AubergineShallow/digital8mm/CLOUD-START-HERE.md

# GS8 D2 · cloud-polish copy

**Fork: `r5-cloud-polish-20261007`.** This independent copy starts from the stable desktop r5 capture of
6 October 2026, 14:04–14:05 UTC, with verified CAD exports captured by 14:11:53 UTC. Later desktop work is a separate
history. Extract into a new folder; do not overwrite or blindly merge into the active desktop project.

## Current result

**r6 (2026-10-08)** settles the print order and orientation and fixes the minor findings of the 2026-10-06 audit
(`cad/gs8-d2-v1/HANDOFF.md`, top section; `audit/d2-readiness-2026-10-06/RESPONSE.md`):
- **Kowa:** 28 categories, 27 passing plus `mass_com`, which is now report-only. 833 pass + 19 information rows, no
  failures, stubs or unclassified thin spots.
- **Fujinon:** 28 categories, 830 pass + 19 information rows.
- The new `print_overhang` category passes for all 12 parts and the centring gauge.
- The release audit passes 20 / 86 / 4.

The cloud-polish result it builds on, kept for the record:
- **Kowa:** 27 passing CAD categories; 748 pass + 18 information rows, no failures, stubs or unclassified thin spots.
- **Fujinon:** 27 passing categories; 745 pass + 18 information rows, no failures, stubs or unclassified thin spots.
- Independent audits verify every required source/output/gate-document hash, actual STL meshes, fresh STEP,
  producer-bound coupons/common tests, both-lens linkage and complete runtime/manifest coverage.
- **Tests:** 65 CAD regressions + 73 focused tests; the full collar check passes for both lenses. The D2/EVF package
  passes 256 host tests; the post planner passes 66, the existing recorder 110, and native numerical models 69.
- **Physical qualification: unchanged.** All 53 physical gates remain open. Nothing was printed, sliced, measured,
  assembled, powered, purchased or deployed by this pass. These results do not establish fabrication or operation readiness.
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
