AubergineShallow/digital8mm/visual-review/REVIEW.md

# D2 visual and ergonomic review

Final review, 2026-10-07 SGT. Reviewed the original r5 render pixels, source design/control contracts, corrected panel pixels, and the final cloud-polish assembly/part STEP. The final Kowa receipt is 806c7b381e1133a5e69c2d1547d915ac305bec2e1cb5e5cf168f74d81eae4832. All dimensions below are CAD/source values, not physical measurements.

Both lens variants have passing computed CAD/integrity reports. All 53 physical gates remain open. The gallery is an intended-finish visualization of the separate cloud-polish fork, not a fabricated or commissioned camera.
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
