AubergineShallow/digital8mm/cad/gs8-d2-v1/airflow/out/domain/slice-1.5-xm7.png

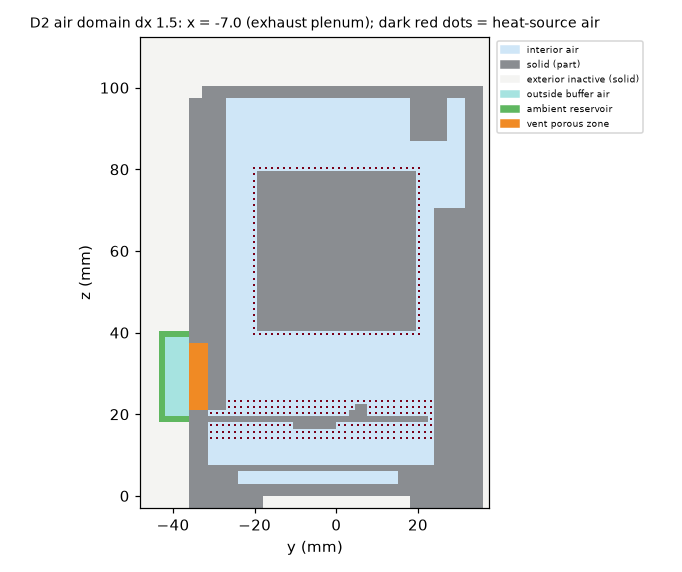
cad/gs8-d2-v1/airflow/out/domain/slice-1.5-xm7.png
