AubergineShallow/digital8mm/cad/gs8-d2-v1/airflow/out/domain/slice-1.5-ym10.png

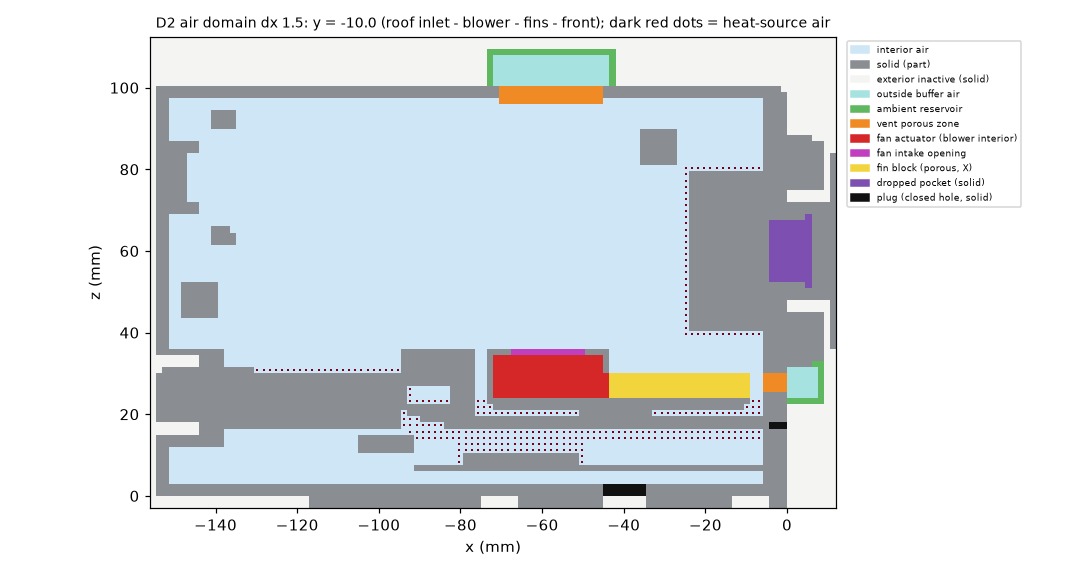
cad/gs8-d2-v1/airflow/out/domain/slice-1.5-ym10.png
