AubergineShallow/digital8mm/cad/gs8-d2-v1/airflow/out/domain/slice-2.0-ym10.png

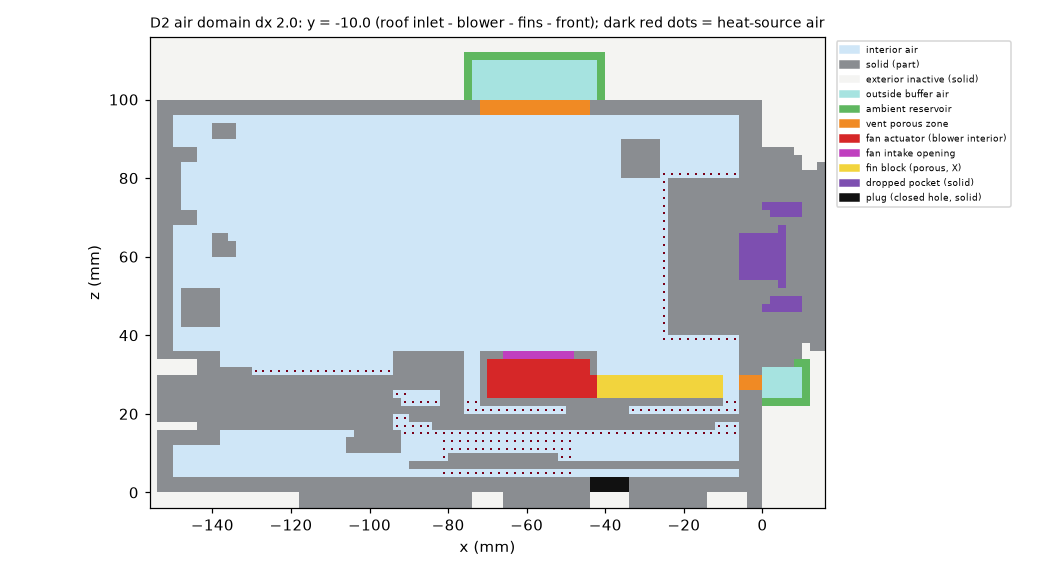
cad/gs8-d2-v1/airflow/out/domain/slice-2.0-ym10.png
