AubergineShallow/digital8mm/cad/gs8-d2-v1/airflow/out/figures/2.0-finaxis/pressure_slices.png

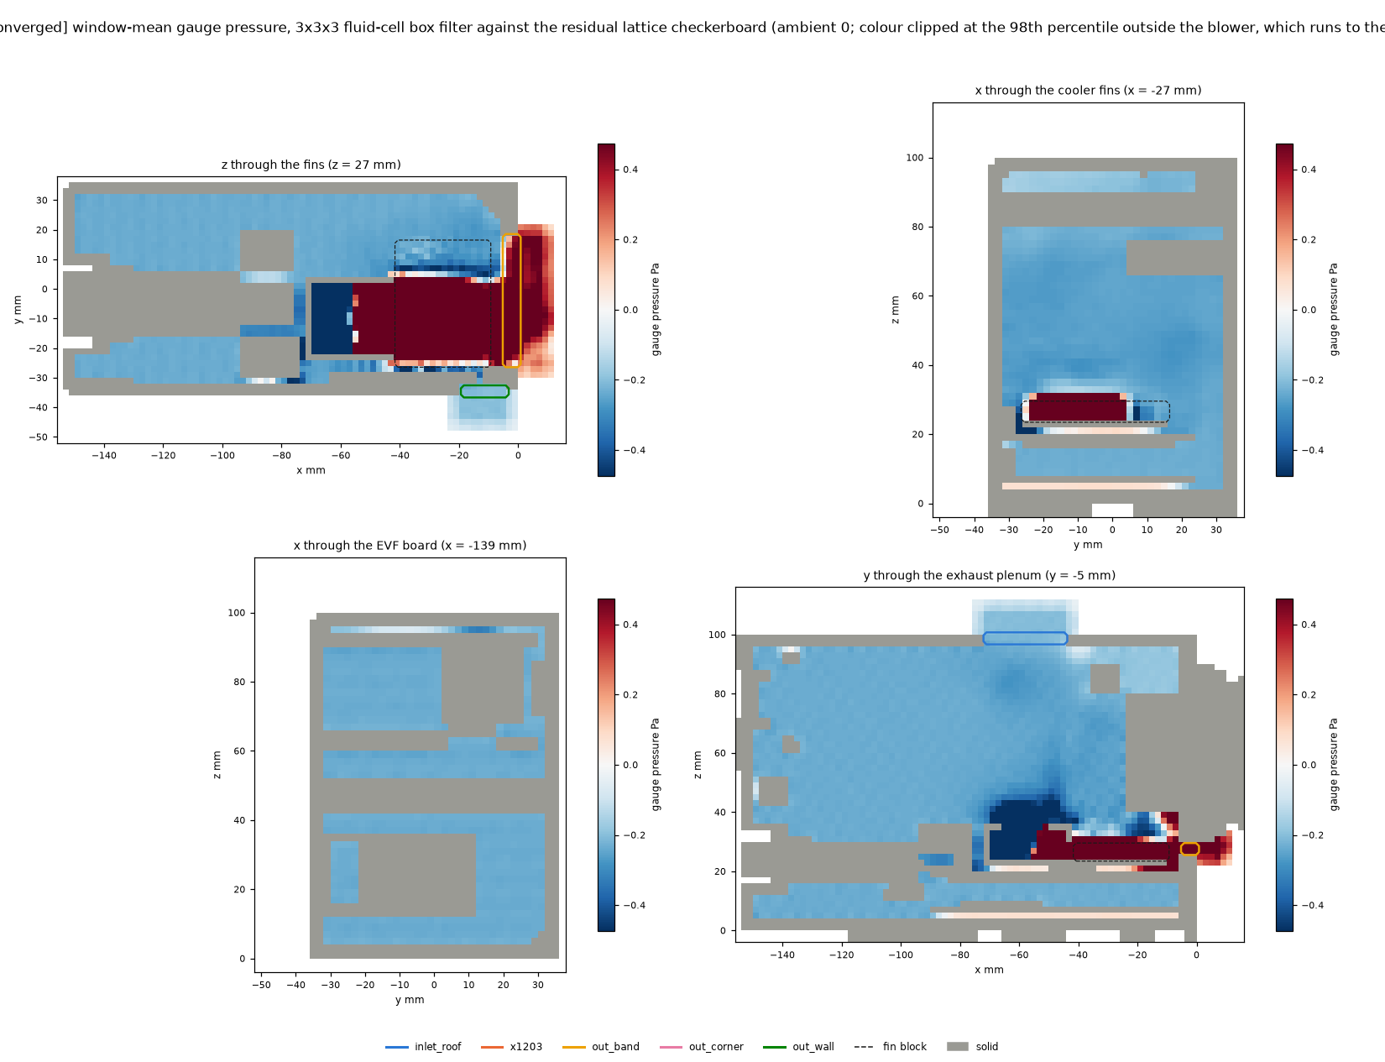
cad/gs8-d2-v1/airflow/out/figures/2.0-finaxis/pressure_slices.png
