AubergineShallow/digital8mm/cad/gs8-d2-v1/airflow/out/figures/2.0-finaxis/temp_S2__adiabatic.png

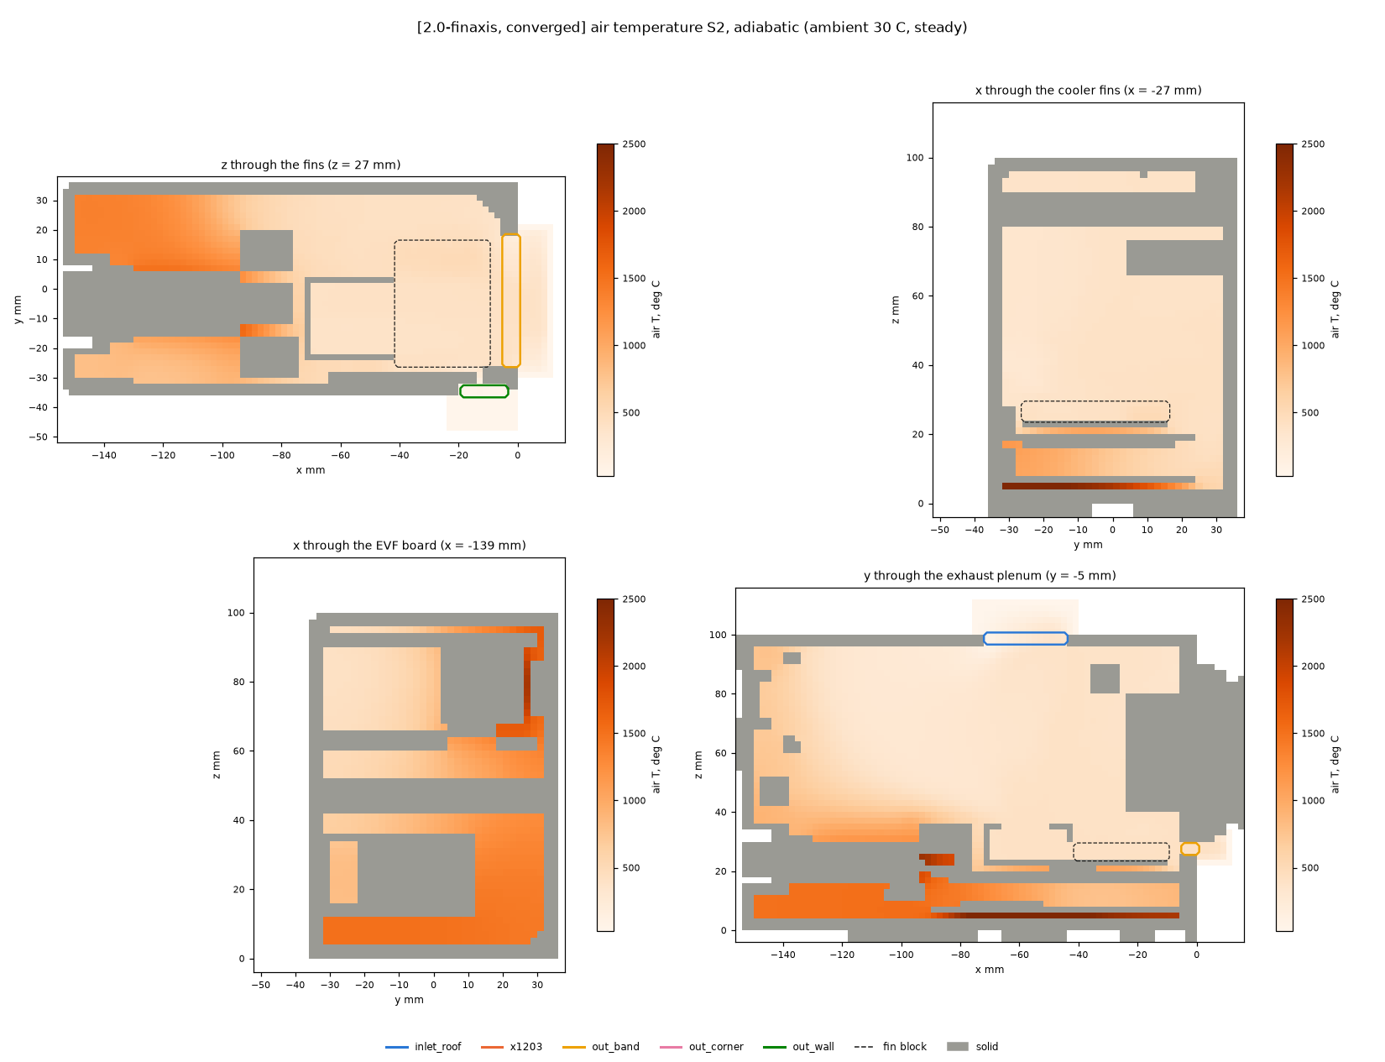
cad/gs8-d2-v1/airflow/out/figures/2.0-finaxis/temp_S2__adiabatic.png
