AubergineShallow/digital8mm/cad/gs8-d2-v1/airflow/out/figures/zzztest/speed_slices.png

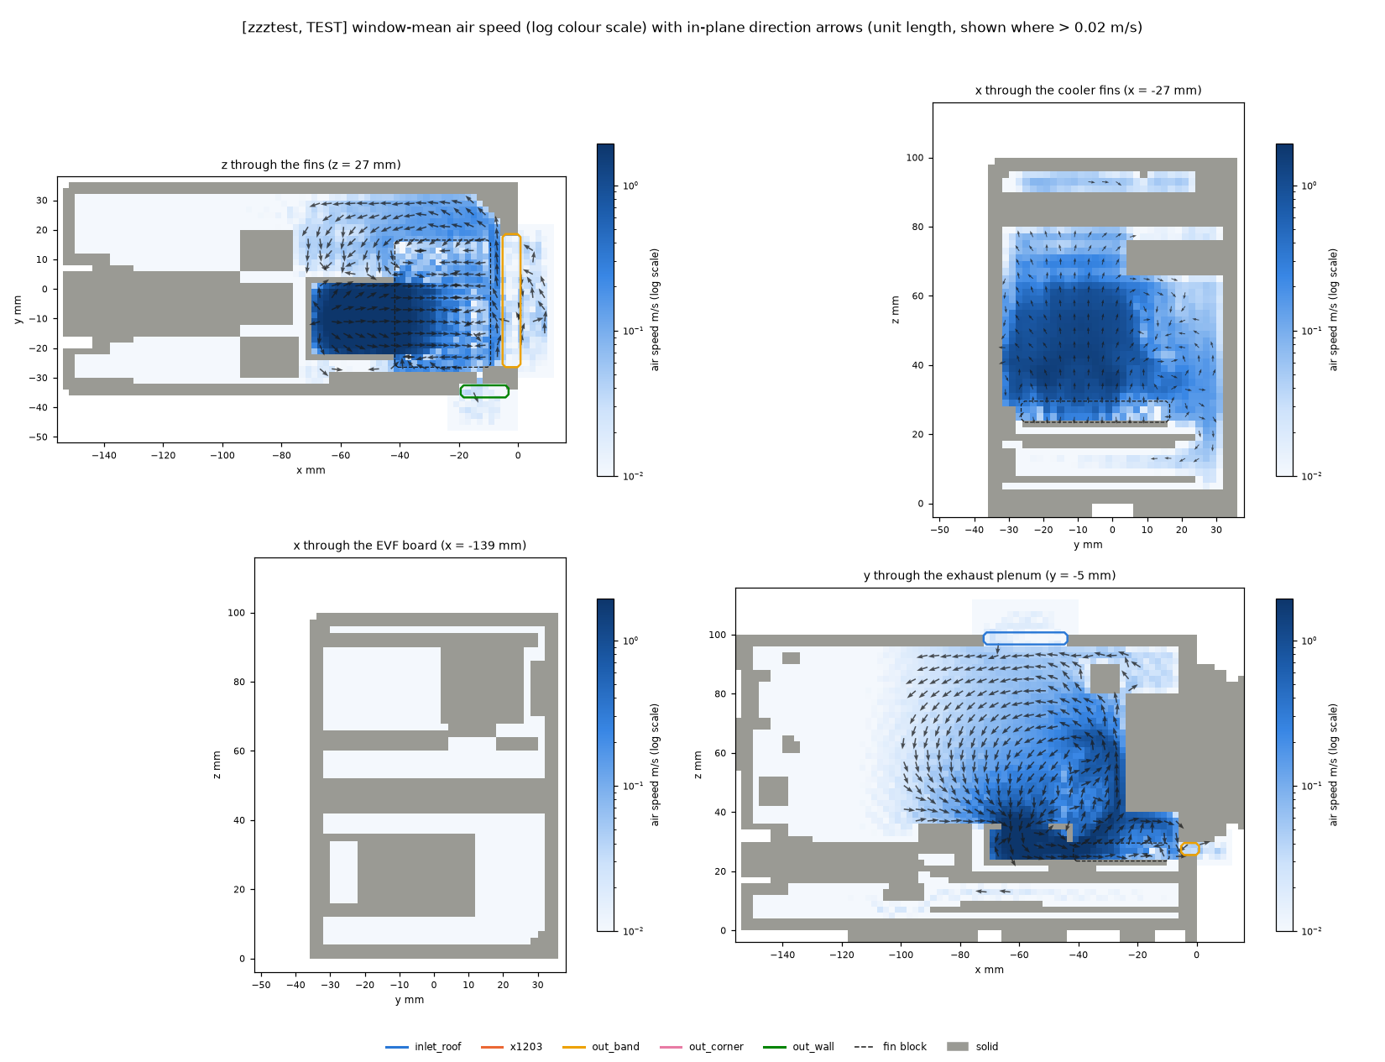
cad/gs8-d2-v1/airflow/out/figures/zzztest/speed_slices.png
