AubergineShallow/digital8mm/cad/gs8-d2-v1/airflow/out/figures/zzztest/streamlines.png

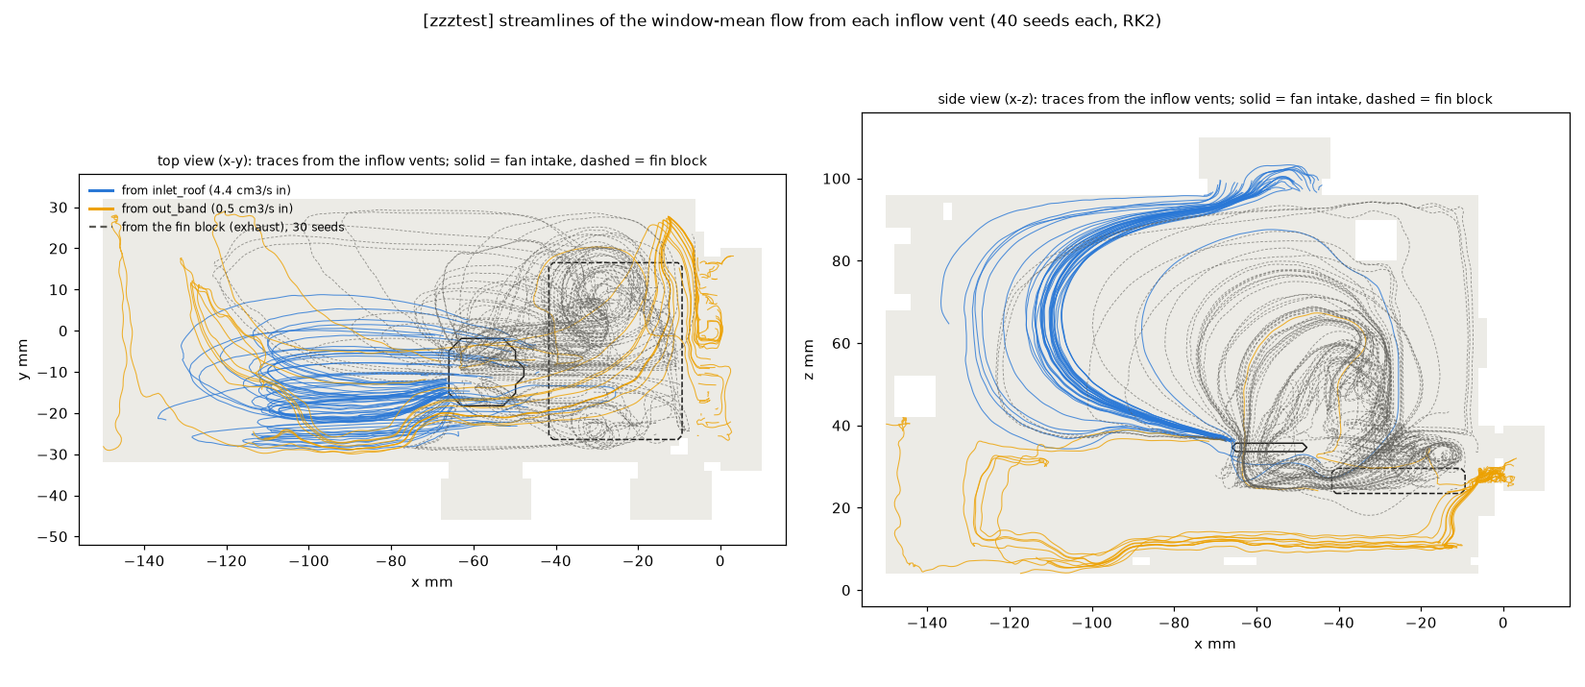
cad/gs8-d2-v1/airflow/out/figures/zzztest/streamlines.png
