AubergineShallow/digital8mm/cad/gs8-d2-v1/airflow/out/variants/compare-throughflow-soc.png

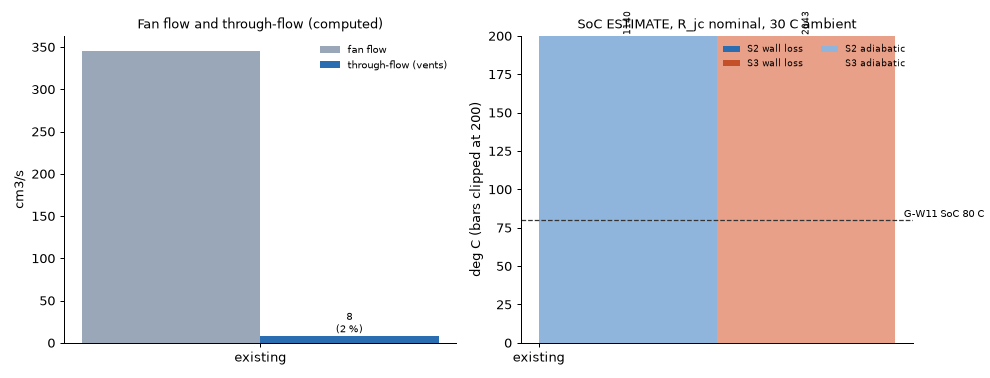
cad/gs8-d2-v1/airflow/out/variants/compare-throughflow-soc.png
