AubergineShallow/digital8mm/cad/gs8-d2-v1/airflow/out/variants/domain-edit-V1.png

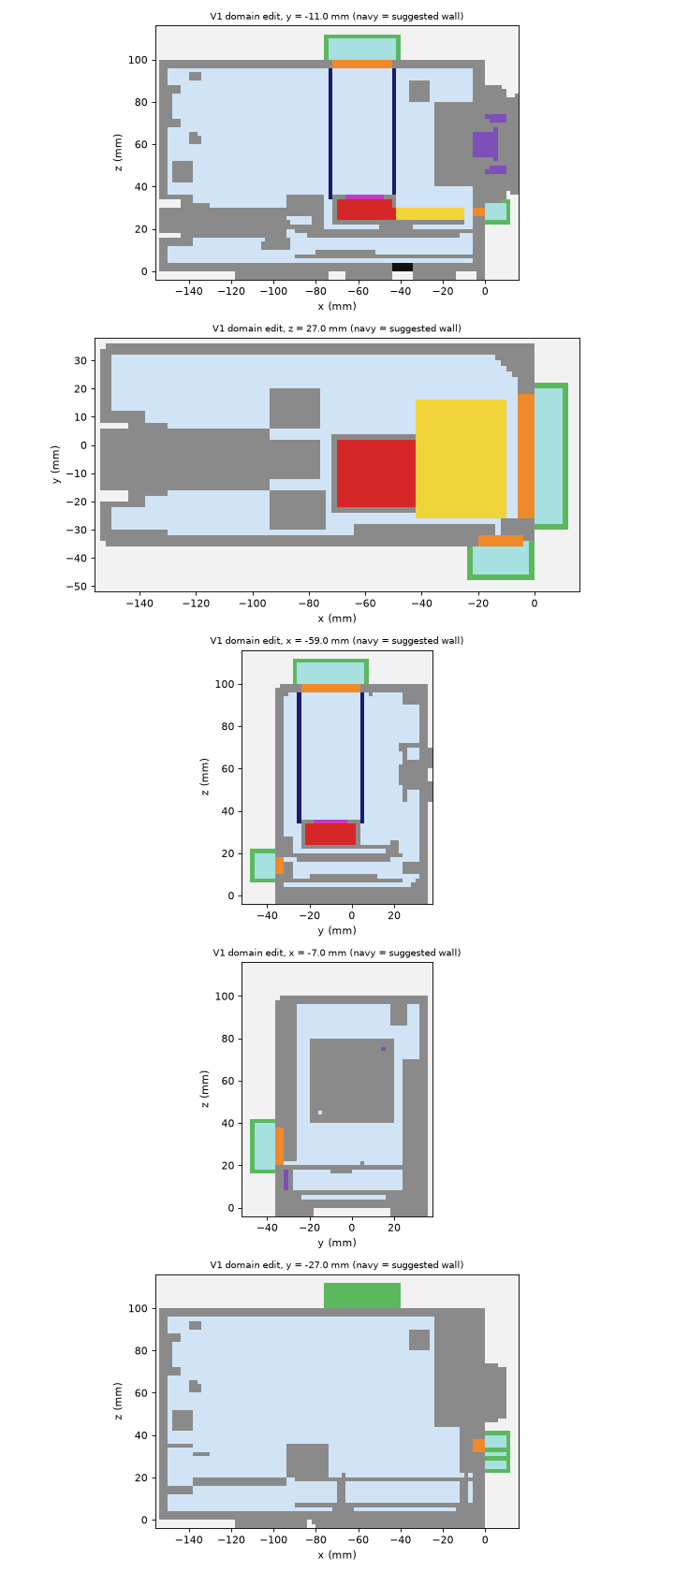
cad/gs8-d2-v1/airflow/out/variants/domain-edit-V1.png
