AubergineShallow/digital8mm/cad/gs8-d2-v1/airflow/out/variants/velocity-z27.png

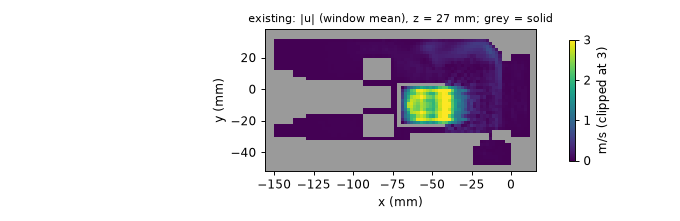
cad/gs8-d2-v1/airflow/out/variants/velocity-z27.png
