AubergineShallow/digital8mm/cad/gs8-d2-v1/candidate-fr1/preview/mobile.png

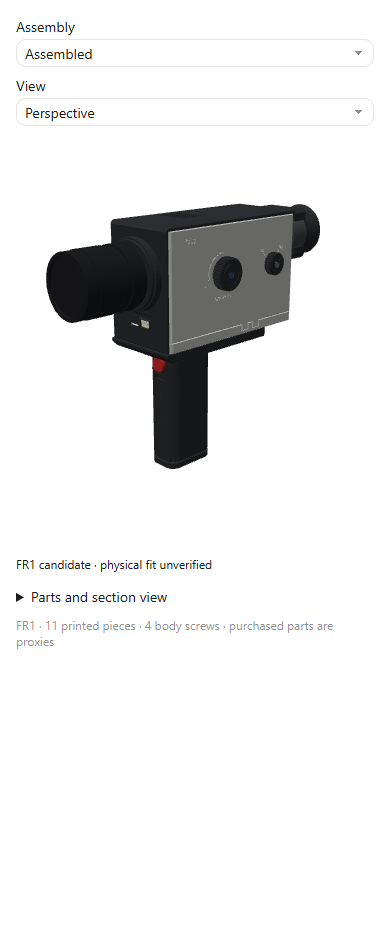
cad/gs8-d2-v1/candidate-fr1/preview/mobile.png
