AubergineShallow/digital8mm/cad/gs8-d2-v1/out/_fujinon-cloud-polish-20261007/renders/section-base-edge-x91.png

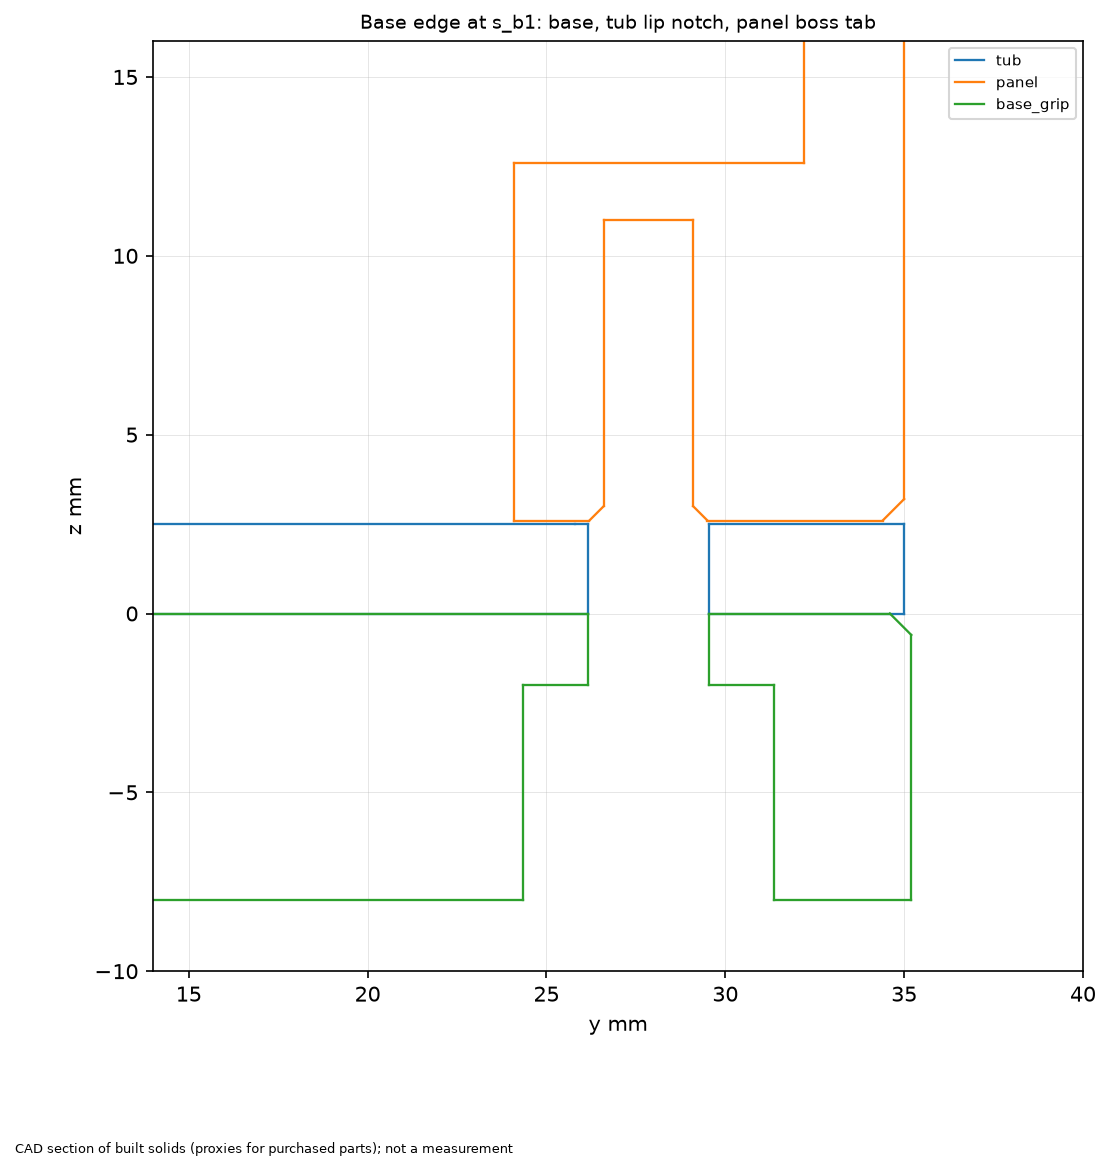
cad/gs8-d2-v1/out/_fujinon-cloud-polish-20261007/renders/section-base-edge-x91.png
