AubergineShallow/digital8mm/visual-review/renders/collar_pinch.png

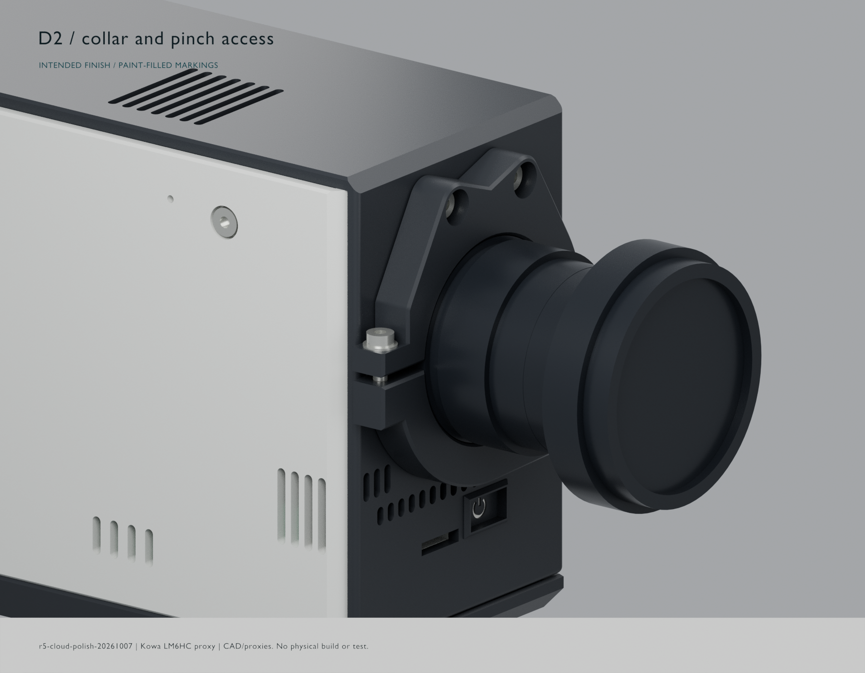
visual-review/renders/collar_pinch.png
