AubergineShallow/digital8mm/visual-review/renders/controls-raw.png

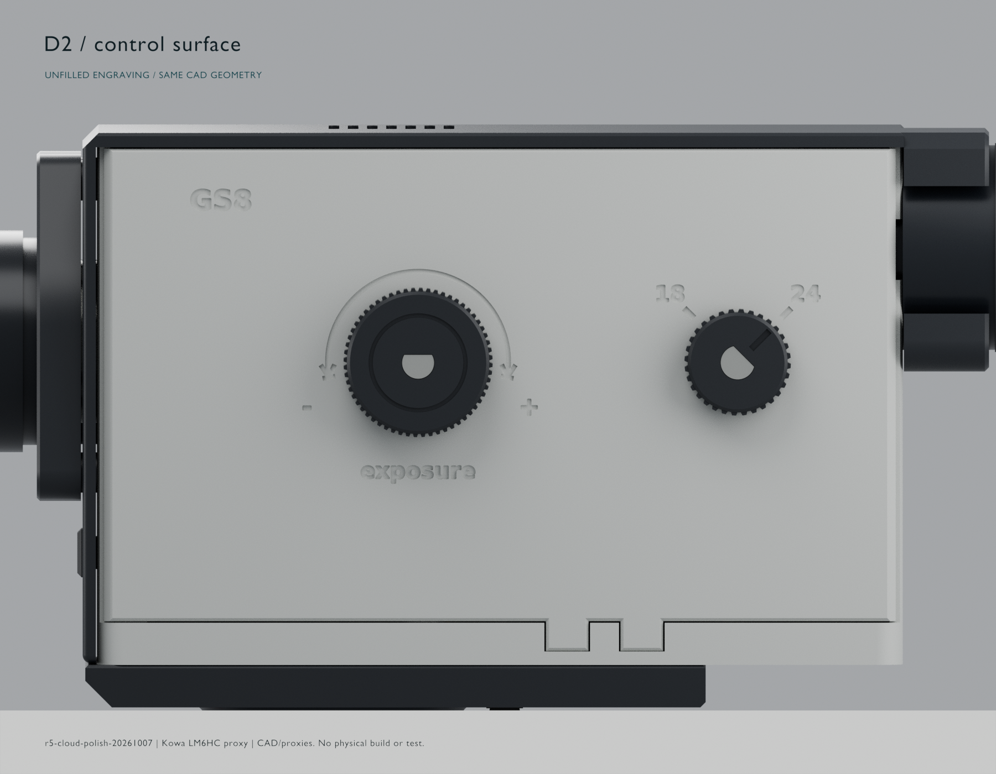
visual-review/renders/controls-raw.png
