AubergineShallow/digital8mm/visual-review/renders/hero.png

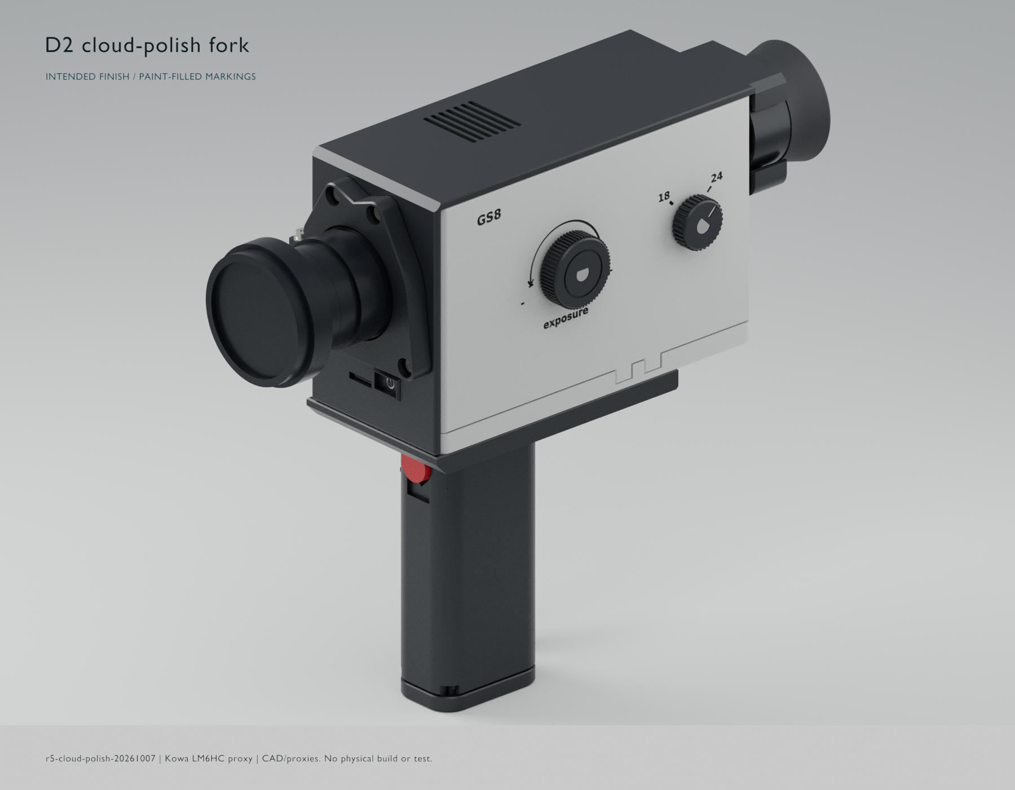
visual-review/renders/hero.png
