AubergineShallow/digital8mm/visual-review/renders/rear.png

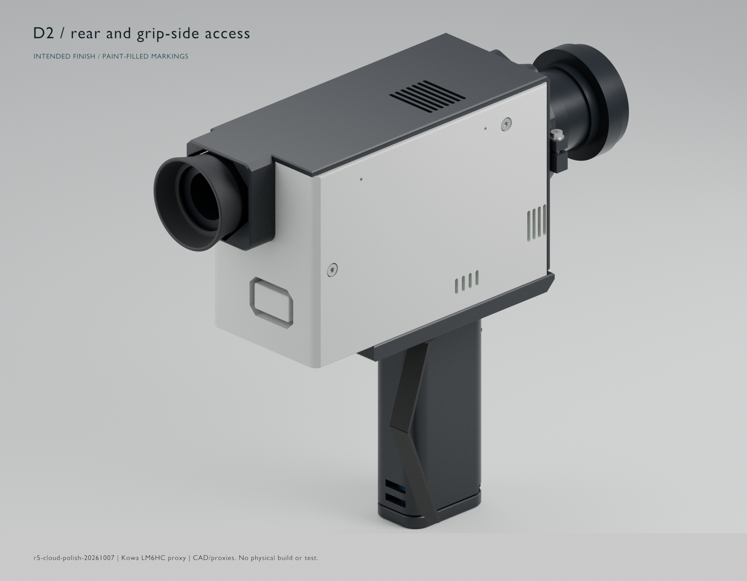
visual-review/renders/rear.png
