AubergineShallow/digital8mm/visual-review/renders/service.png

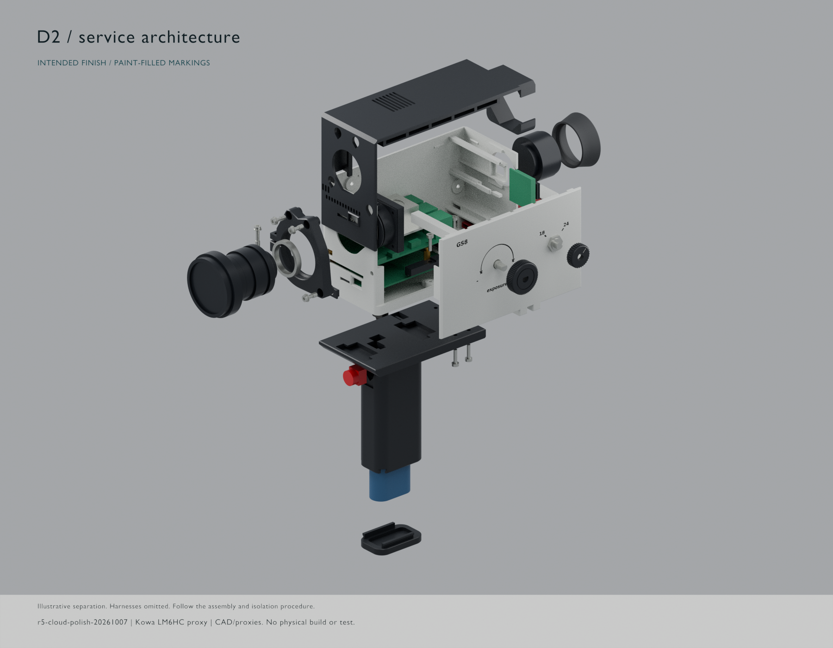
visual-review/renders/service.png
