AubergineShallow/digital8mm/cad/gs8-d2-v1/airflow/out/meshes/plunger.stl

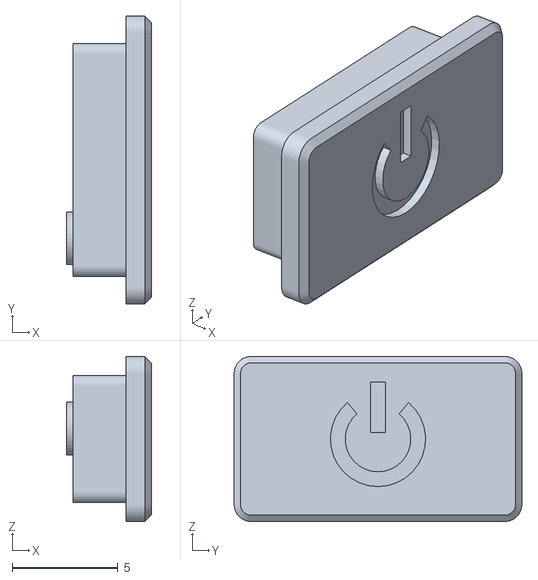
[picture p52: CAD file, 2026-10-08]
cad/gs8-d2-v1/airflow/out/meshes/plunger.stl
4.00 x 13.6 x 7.80
