AubergineShallow/digital8mm/cad/gs8-d2-v1/out/_fujinon-cloud-polish-20261007/stl/modifiers/tub__mod_s_r1.stl

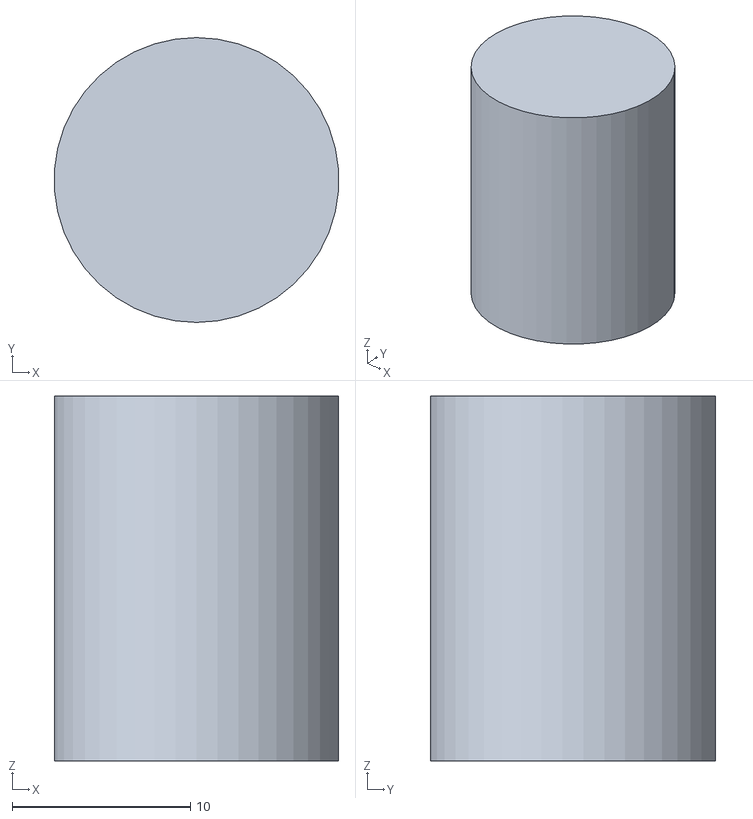
[picture p53: CAD file, 2026-10-08]
cad/gs8-d2-v1/out/_fujinon-cloud-polish-20261007/stl/modifiers/tub__mod_s_r1.stl
16.0 x 16.0 x 20.5
