AubergineShallow/digital8mm/cad/gs8-d2-v1/out/stl/coupons/collar_part.stl

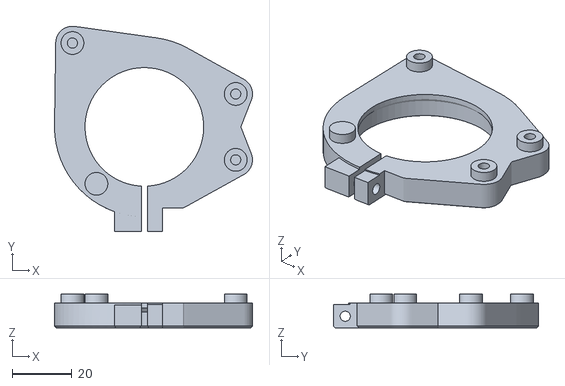
[picture p54: CAD file, 2026-10-08]
cad/gs8-d2-v1/out/stl/coupons/collar_part.stl
66.1 x 68.6 x 11.3
