AubergineShallow/digital8mm/audit/d2-readiness-2026-10-05/rebuild-kowa/stl/panel.stl

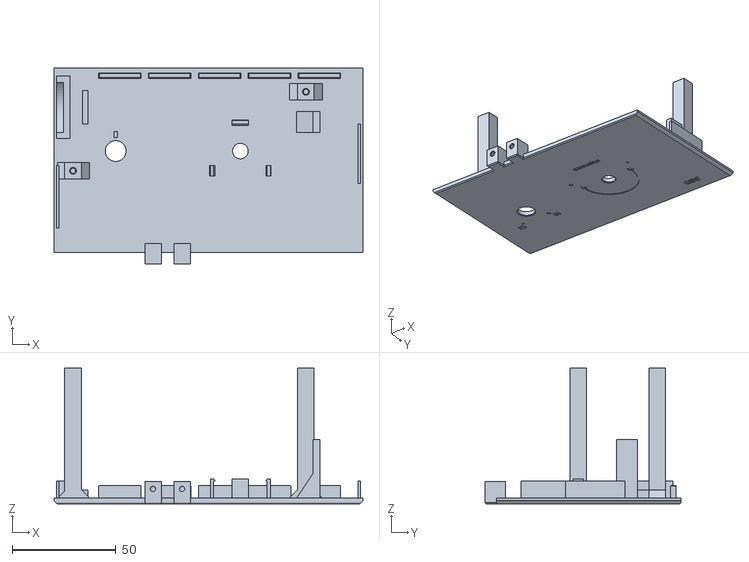
[picture p55: CAD file, 2026-10-08]
audit/d2-readiness-2026-10-05/rebuild-kowa/stl/panel.stl
148.6 x 94.4 x 65.4
