AubergineShallow/digital8mm/audit/d2-readiness-2026-10-06/rebuild-kowa/stl/stick_sleeve.stl

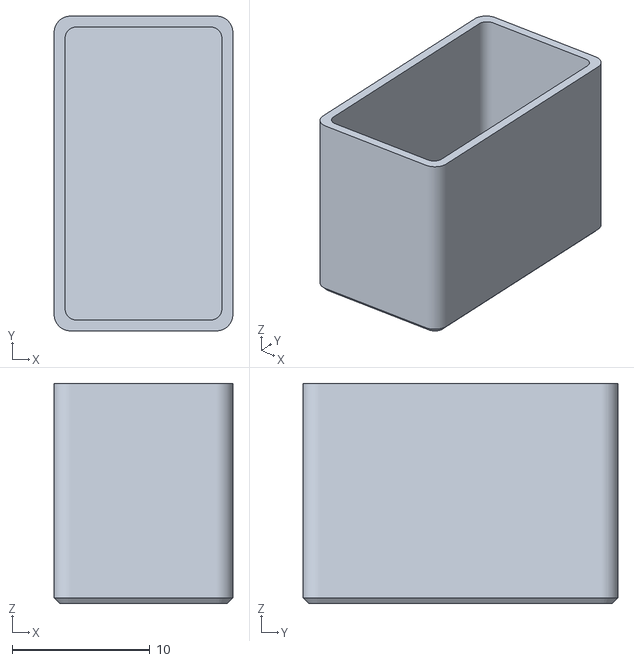
[picture p56: CAD file, 2026-10-08]
audit/d2-readiness-2026-10-06/rebuild-kowa/stl/stick_sleeve.stl
13.0 x 22.9 x 16.0
