AubergineShallow/digital8mm/cad/gs8-d2-v1/airflow/out/meshes/gs_camera.stl

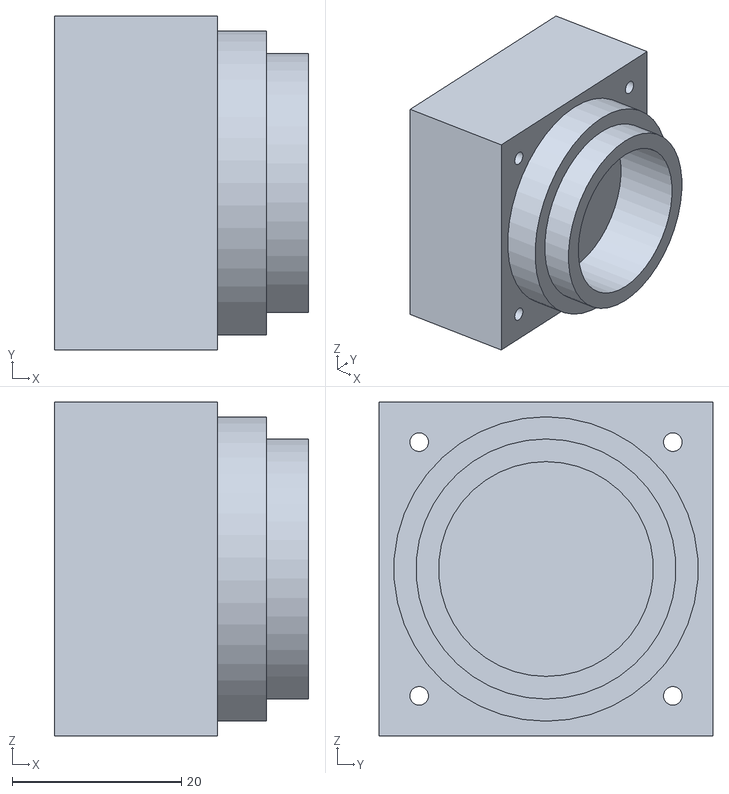
[picture p57: CAD file, 2026-10-08]
cad/gs8-d2-v1/airflow/out/meshes/gs_camera.stl
30.1 x 39.5 x 39.5
