AubergineShallow/digital8mm/cad/gs8-d2-v1/out/stl/coupons/collar_tub_front.stl

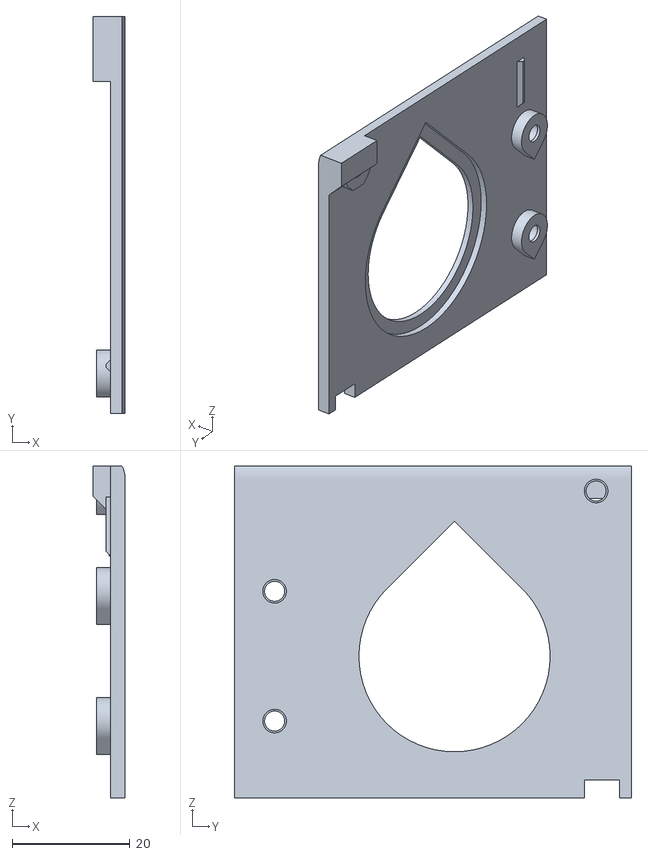
[picture p58: CAD file, 2026-10-08]
cad/gs8-d2-v1/out/stl/coupons/collar_tub_front.stl
5.50 x 67.3 x 56.2
