AubergineShallow/digital8mm/audit/d2-readiness-2026-10-05/rebuild-kowa/stl/hood.stl

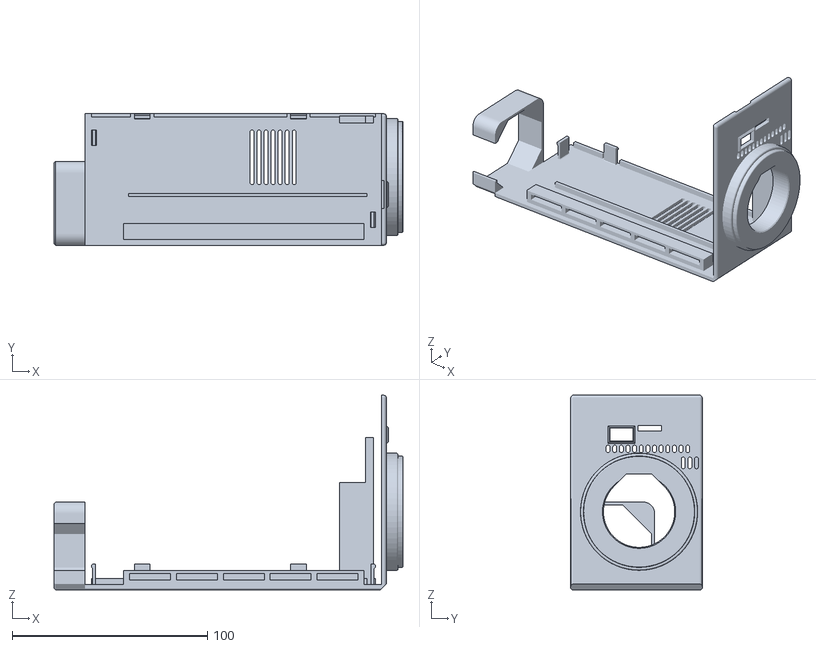
[picture p59: CAD file, 2026-10-08]
audit/d2-readiness-2026-10-05/rebuild-kowa/stl/hood.stl
178.7 x 67.3 x 99.7
