AubergineShallow/digital8mm/cad/gs8-d2-v1/airflow/out/meshes/encoder.stl

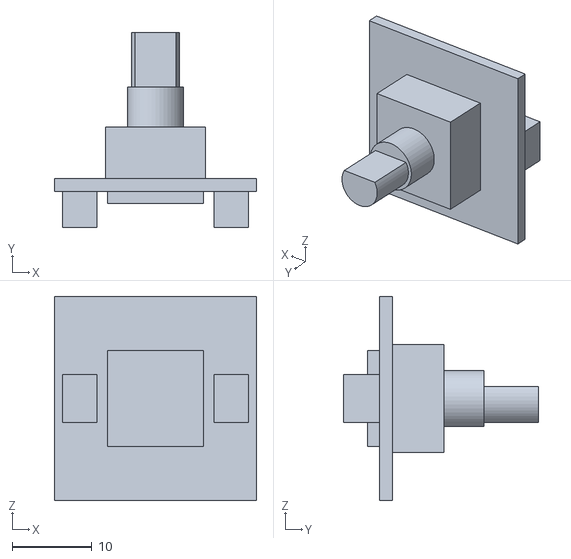
[picture p60: CAD file, 2026-10-08]
cad/gs8-d2-v1/airflow/out/meshes/encoder.stl
25.3 x 24.4 x 25.6
