AubergineShallow/digital8mm/cad/gs8-d2-v1/out/_fujinon-cloud-polish-20261007/step/parts/tub.step

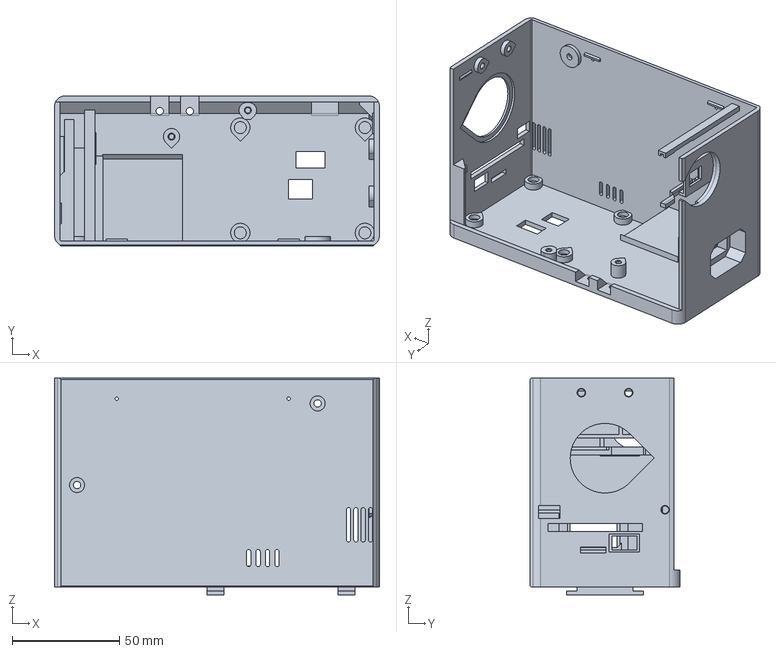
[picture p61: CAD file, 2026-10-09]
cad/gs8-d2-v1/out/_fujinon-cloud-polish-20261007/step/parts/tub.step
151.3 x 70.0 x 101.0 mm
