AubergineShallow/digital8mm/cad/gs8-d2-v1/out/step/parts/knob_exp.step

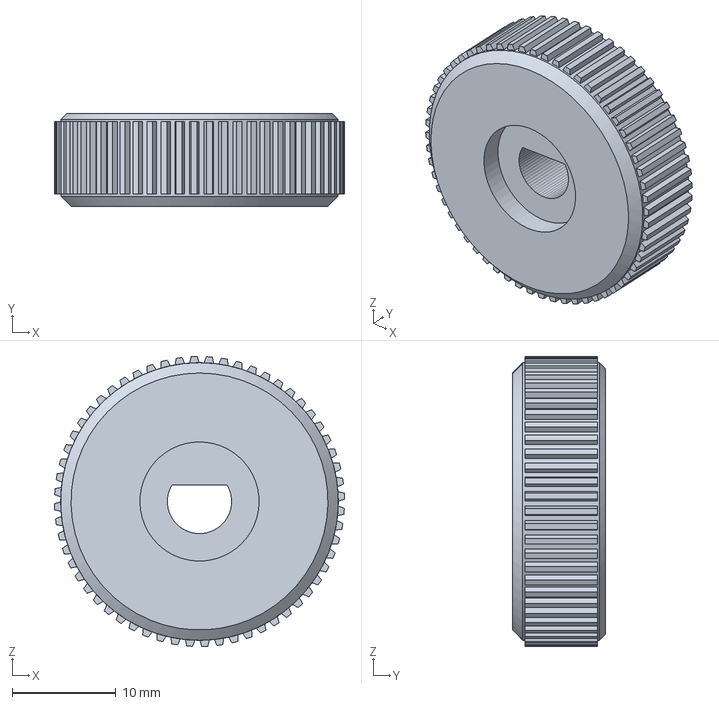
[picture p62: CAD file, 2026-10-09]
cad/gs8-d2-v1/out/step/parts/knob_exp.step
28.0 x 9.00 x 28.0 mm
