AubergineShallow/digital8mm/cad/gs8-d2-v1/out/stl/coupons/hood_ledge_ret.stl

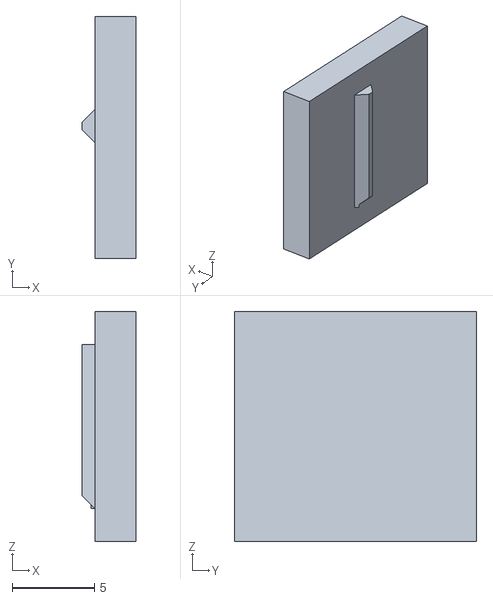
[picture p63: CAD file, 2026-10-08]
cad/gs8-d2-v1/out/stl/coupons/hood_ledge_ret.stl
3.30 x 14.8 x 14.0
