AubergineShallow/digital8mm/audit/d2-readiness-2026-10-05-r3/rebuild-fr1/stl/base_grip.stl

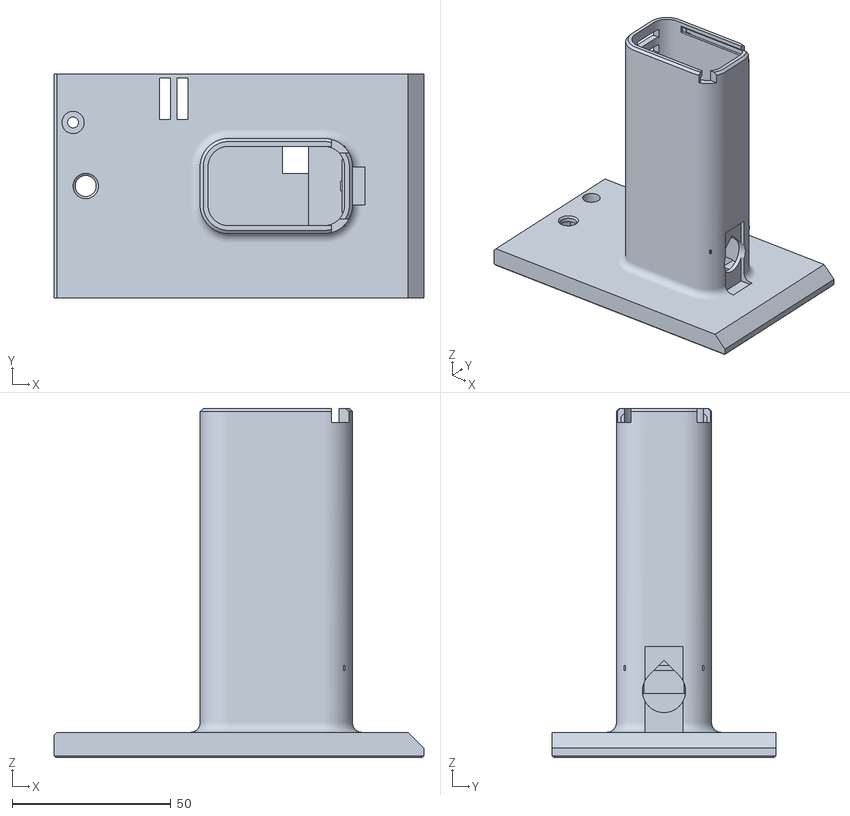
[picture p64: CAD file, 2026-10-08]
audit/d2-readiness-2026-10-05-r3/rebuild-fr1/stl/base_grip.stl
116.5 x 70.4 x 110.0
