AubergineShallow/digital8mm/cad/gs8-d2-v1/airflow/out/meshes/hmx039.stl

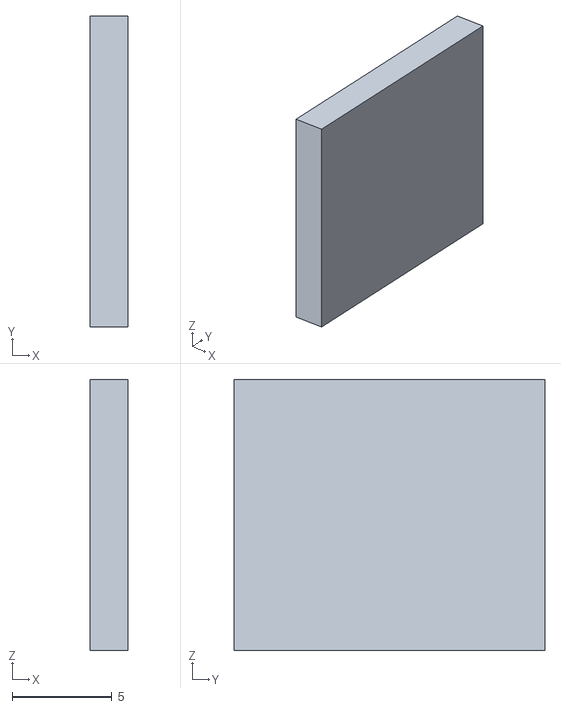
[picture p65: CAD file, 2026-10-08]
cad/gs8-d2-v1/airflow/out/meshes/hmx039.stl
1.93 x 15.6 x 13.6
