AubergineShallow/digital8mm/cad/gs8-d2-v1/out/step/parts/cap.step

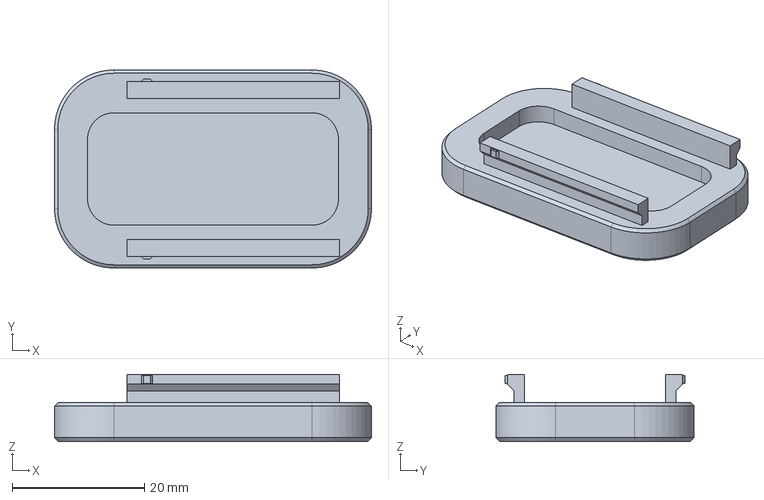
[picture p66: CAD file, 2026-10-09]
cad/gs8-d2-v1/out/step/parts/cap.step
48.0 x 30.0 x 10.2 mm
