AubergineShallow/digital8mm/cad/gs8-d2-v1/out/stl/coupons/evf_stop_panel.stl

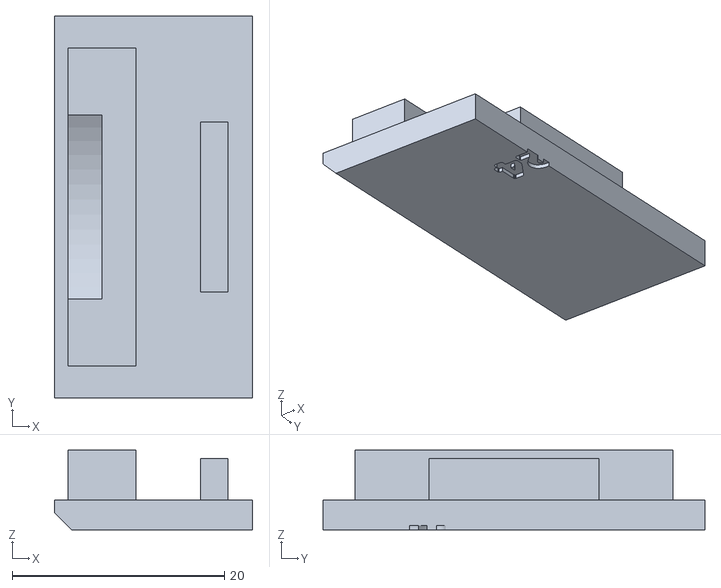
[picture p67: CAD file, 2026-10-08]
cad/gs8-d2-v1/out/stl/coupons/evf_stop_panel.stl
18.7 x 36.0 x 7.50
