AubergineShallow/digital8mm/audit/d2-readiness-2026-10-05-r3/rebuild-fr1/stl/panel.stl

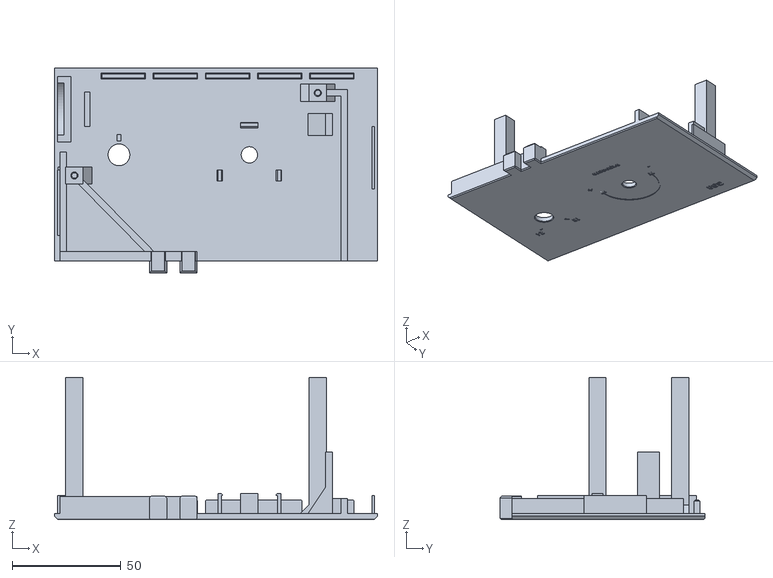
[picture p68: CAD file, 2026-10-08]
audit/d2-readiness-2026-10-05-r3/rebuild-fr1/stl/panel.stl
148.6 x 94.4 x 65.4
