AubergineShallow/digital8mm/cad/gs8-d2-v1/airflow/out/meshes/c_cs_adapter.stl

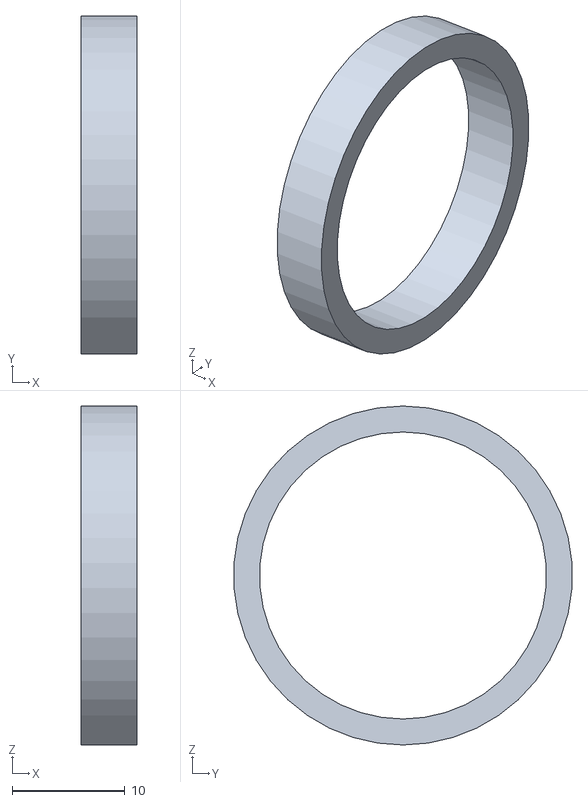
[picture p69: CAD file, 2026-10-08]
cad/gs8-d2-v1/airflow/out/meshes/c_cs_adapter.stl
5.00 x 29.9 x 30.0
