AubergineShallow/digital8mm/cad/gs8-d2-v1/out/_fujinon-cloud-polish-20261007/step/parts/hood.step

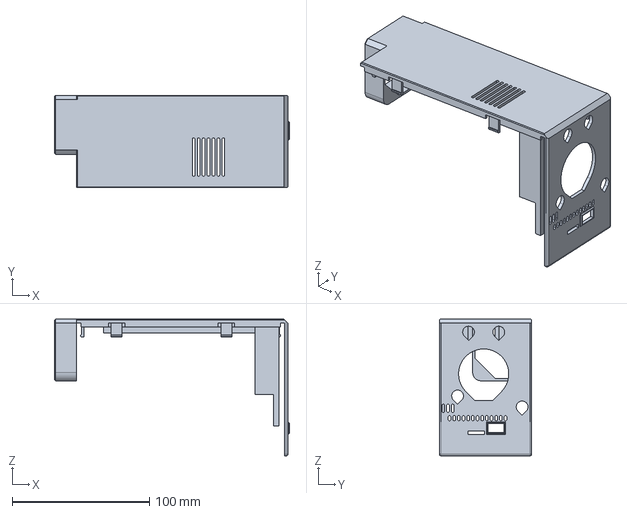
[picture p70: CAD file, 2026-10-09]
cad/gs8-d2-v1/out/_fujinon-cloud-polish-20261007/step/parts/hood.step
171.2 x 67.3 x 99.7 mm
