AubergineShallow/digital8mm/cad/gs8-d2-v1/out/stl/coupons/keyhole_slot.stl

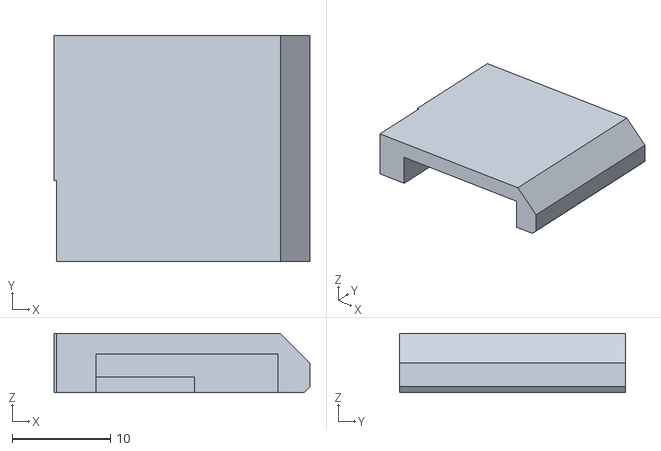
[picture p71: CAD file, 2026-10-08]
cad/gs8-d2-v1/out/stl/coupons/keyhole_slot.stl
26.0 x 23.0 x 6.00
