AubergineShallow/digital8mm/cad/gs8-d2-v1/out/_fujinon-cloud-polish-20261007/step/parts/lens_collar.step

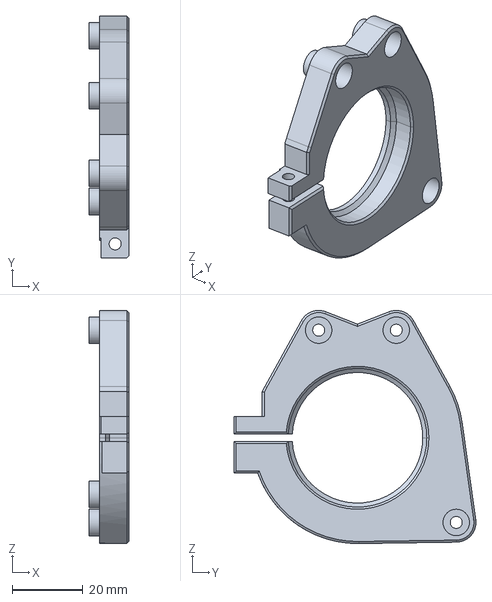
[picture p72: CAD file, 2026-10-09]
cad/gs8-d2-v1/out/_fujinon-cloud-polish-20261007/step/parts/lens_collar.step
11.3 x 68.6 x 66.1 mm
