AubergineShallow/digital8mm/cad/gs8-d2-v1/out/stl/coupons/pt_boss_bottom.stl

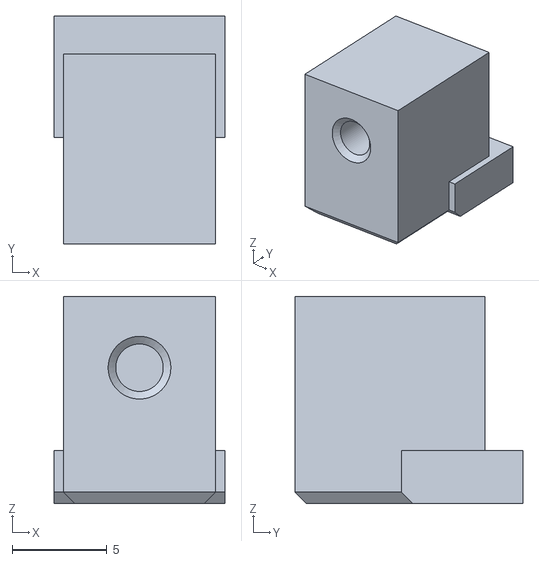
[picture p73: CAD file, 2026-10-08]
cad/gs8-d2-v1/out/stl/coupons/pt_boss_bottom.stl
9.00 x 12.0 x 10.9
