AubergineShallow/digital8mm/audit/d2-readiness-2026-10-06/rebuild-kowa/stl/hood.stl

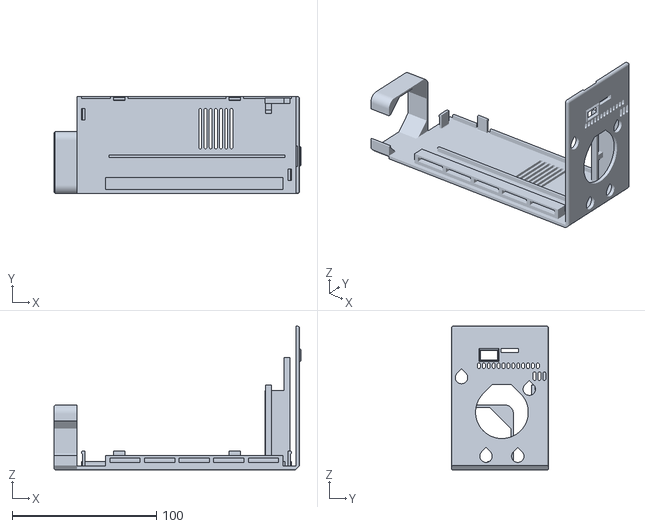
[picture p74: CAD file, 2026-10-08]
audit/d2-readiness-2026-10-06/rebuild-kowa/stl/hood.stl
171.2 x 67.3 x 99.7
