AubergineShallow/digital8mm/cad/gs8-d2-v1/airflow/out/meshes/s_r2.stl

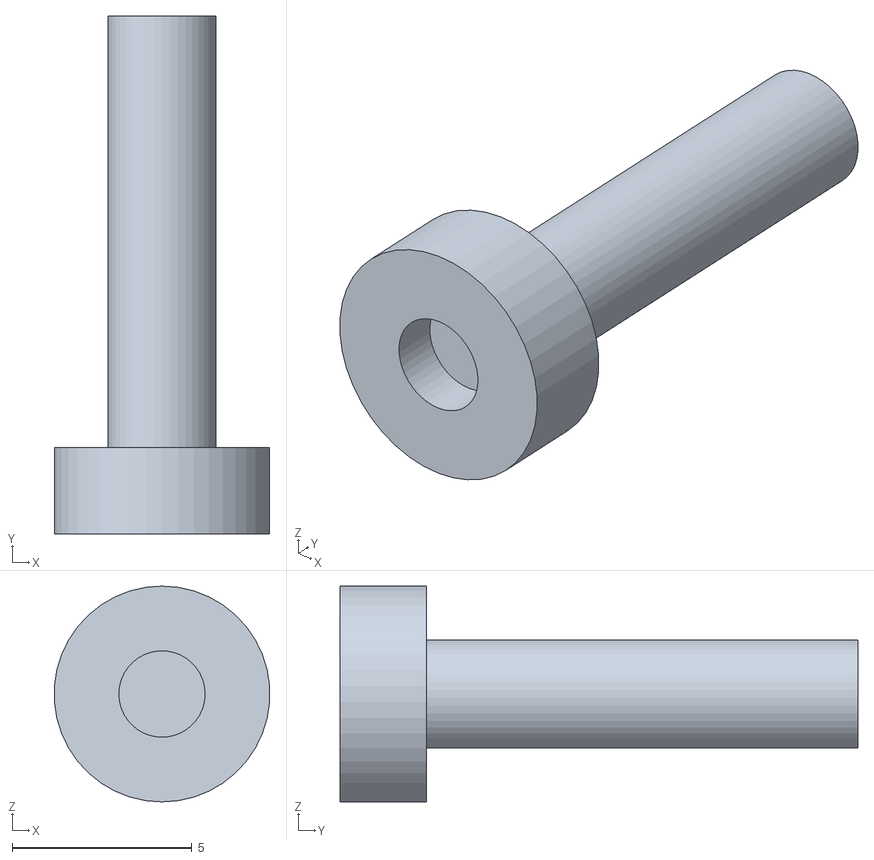
[picture p75: CAD file, 2026-10-08]
cad/gs8-d2-v1/airflow/out/meshes/s_r2.stl
5.98 x 14.4 x 6.00
