AubergineShallow/digital8mm/cad/gs8-d2-v1/out/stl/coupons/encoder_cradle_hook.stl

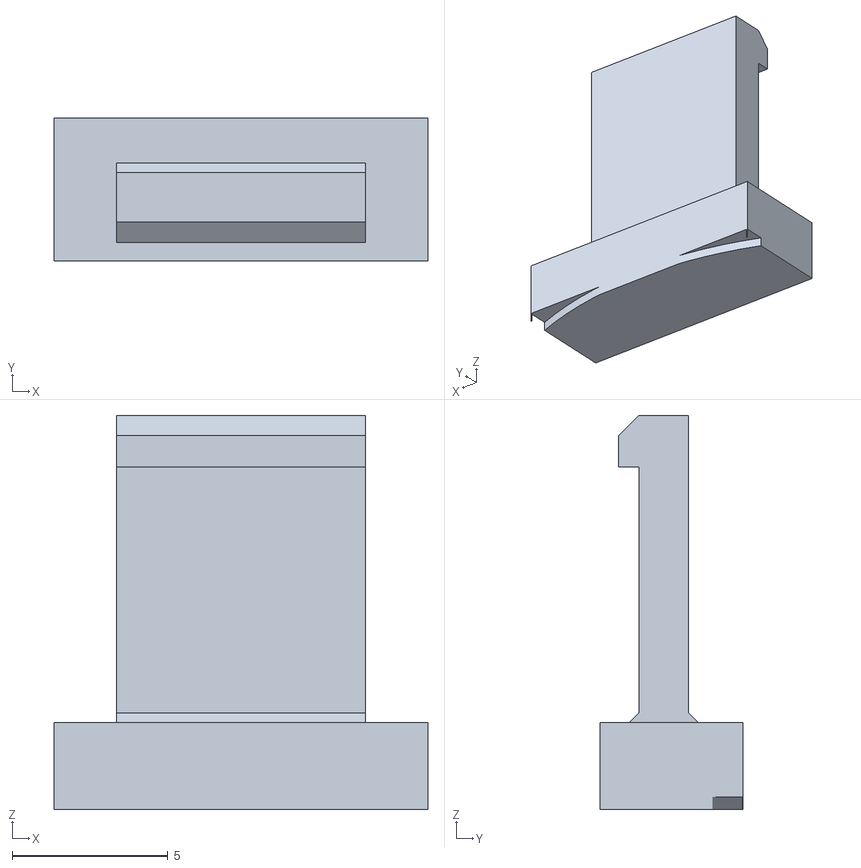
[picture p76: CAD file, 2026-10-08]
cad/gs8-d2-v1/out/stl/coupons/encoder_cradle_hook.stl
12.0 x 4.60 x 12.6
