AubergineShallow/digital8mm/cad/gs8-d2-v1/out/stl/coupons/clearance_comb.stl

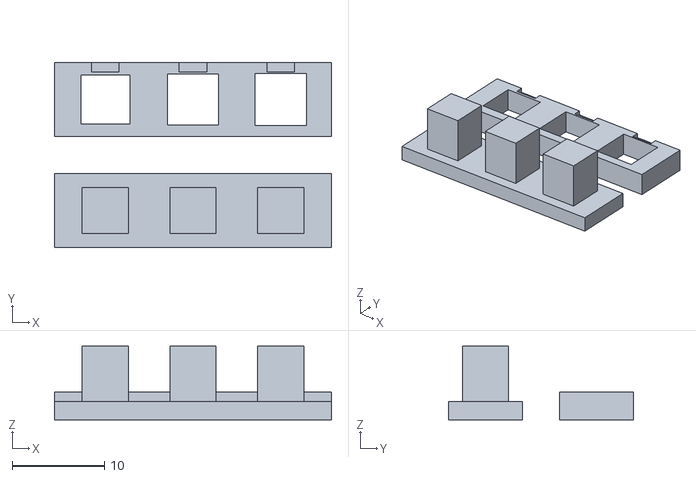
[picture p77: CAD file, 2026-10-08]
cad/gs8-d2-v1/out/stl/coupons/clearance_comb.stl
30.0 x 20.0 x 8.00
