AubergineShallow/digital8mm/audit/d2-readiness-2026-10-06/rebuild-kowa/stl/lens_collar.stl

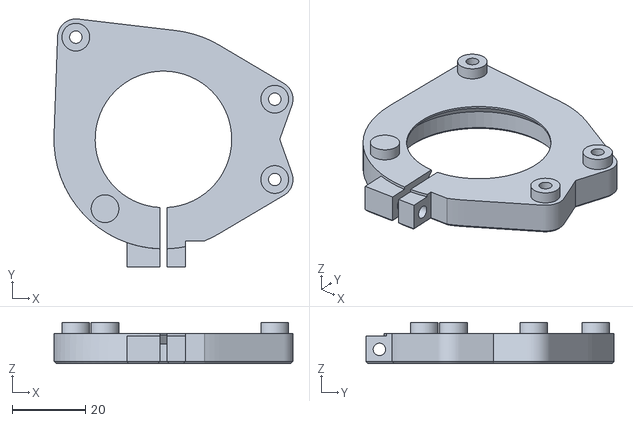
[picture p78: CAD file, 2026-10-08]
audit/d2-readiness-2026-10-06/rebuild-kowa/stl/lens_collar.stl
65.5 x 68.0 x 11.3
