AubergineShallow/digital8mm/cad/gs8-d2-v1/out/stl/coupons/coupon-pi-keeper-pi.stl

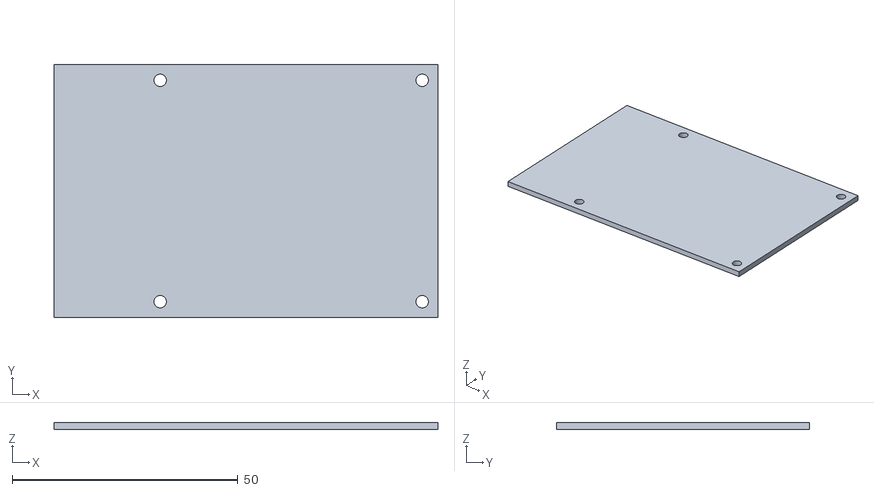
[picture p79: CAD file, 2026-10-08]
cad/gs8-d2-v1/out/stl/coupons/coupon-pi-keeper-pi.stl
85.0 x 56.0 x 1.60
