AubergineShallow/digital8mm/cad/gs8-d2-v1/out/stl/coupons/knob_bore_ladder_sw.stl

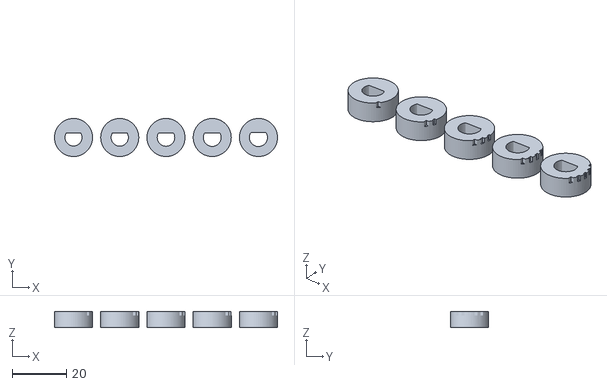
[picture p80: CAD file, 2026-10-08]
cad/gs8-d2-v1/out/stl/coupons/knob_bore_ladder_sw.stl
82.0 x 14.0 x 6.00
