AubergineShallow/digital8mm/cad/gs8-d2-v1/out/stl/coupons/tongue.stl

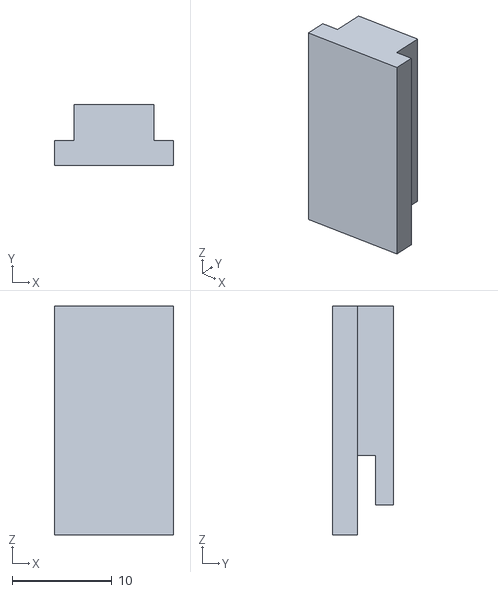
[picture p81: CAD file, 2026-10-08]
cad/gs8-d2-v1/out/stl/coupons/tongue.stl
12.0 x 6.15 x 23.0
