AubergineShallow/digital8mm/cad/gs8-d2-v1/out/stl/coupons/pt_boss_post.stl

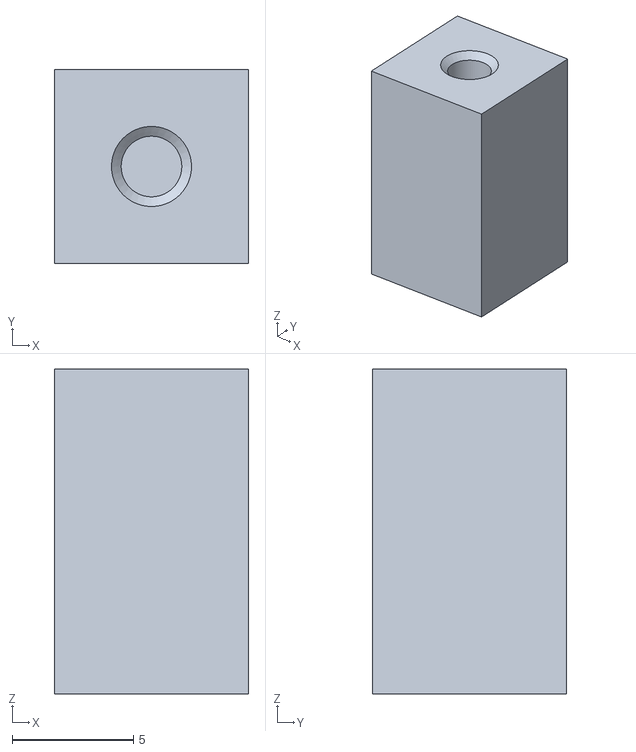
[picture p82: CAD file, 2026-10-08]
cad/gs8-d2-v1/out/stl/coupons/pt_boss_post.stl
8.00 x 8.00 x 13.4
