AubergineShallow/digital8mm/cad/gs8-d2-v1/out/stl/coupons/base_edge_panel.stl

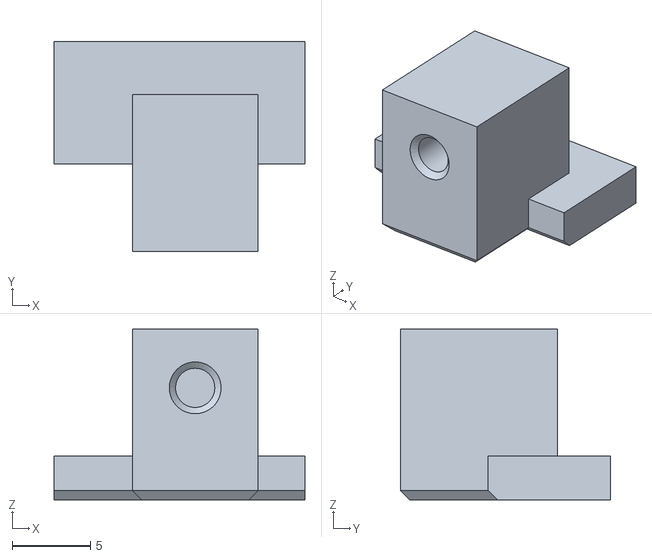
[picture p83: CAD file, 2026-10-08]
cad/gs8-d2-v1/out/stl/coupons/base_edge_panel.stl
16.0 x 13.4 x 10.9
