AubergineShallow/digital8mm/cad/gs8-d2-v1/airflow/out/meshes/run_button.stl

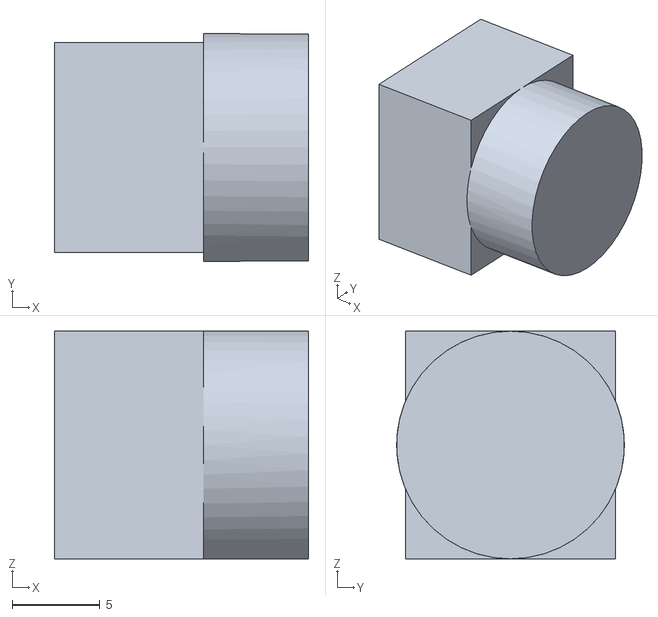
[picture p84: CAD file, 2026-10-08]
cad/gs8-d2-v1/airflow/out/meshes/run_button.stl
14.5 x 13.0 x 13.0
