AubergineShallow/digital8mm/cad/gs8-d2-v1/out/stl/coupons/base_edge_tub.stl

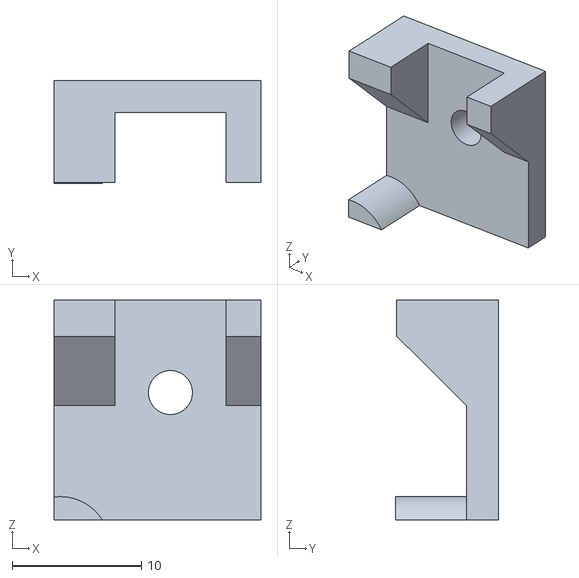
[picture p85: CAD file, 2026-10-08]
cad/gs8-d2-v1/out/stl/coupons/base_edge_tub.stl
16.0 x 8.00 x 17.0
