AubergineShallow/digital8mm/cad/gs8-d2-v1/out/stl/coupons/collar_hood_plate.stl

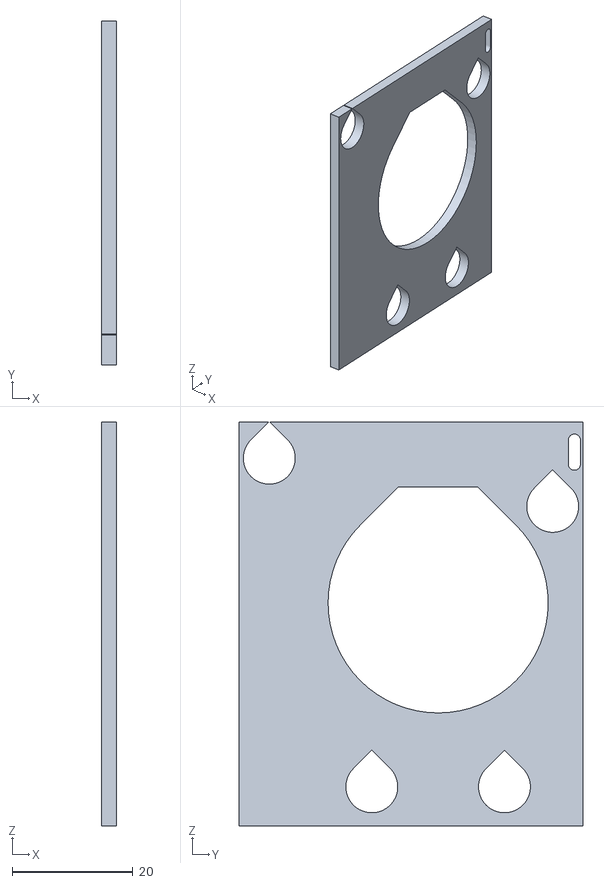
[picture p86: CAD file, 2026-10-08]
cad/gs8-d2-v1/out/stl/coupons/collar_hood_plate.stl
2.50 x 57.0 x 67.0
