AubergineShallow/digital8mm/cad/gs8-d2-v1/airflow/out/meshes/usb_stick.stl

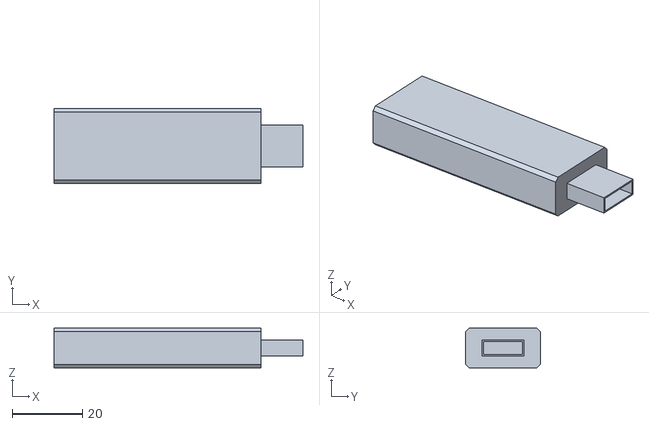
[picture p87: CAD file, 2026-10-08]
cad/gs8-d2-v1/airflow/out/meshes/usb_stick.stl
71.0 x 21.3 x 11.4
