AubergineShallow/digital8mm/cad/gs8-d2-v1/out/stl/coupons/hood_hook.stl

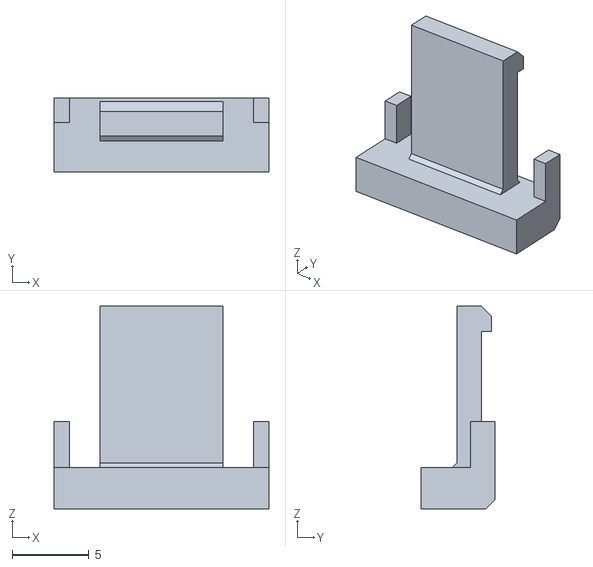
[picture p88: CAD file, 2026-10-08]
cad/gs8-d2-v1/out/stl/coupons/hood_hook.stl
14.0 x 4.85 x 13.2
