AubergineShallow/digital8mm/cad/gs8-d2-v1/guide/BLOCKERS-2026-10-08.md

# D2 assembly blocker review (2026-10-08)

Status: final (2026-10-08, review 16:33-17:00 MPST). Blocker-review agent for the IKEA-guide session; the table ids BX-1..BX-17 and C-1..C-16 are stable.

Scope: physical assemblability of cad/gs8-d2-v1 following ASSEMBLY.md (s2 B0/B1, steps 1-10, s7 service order) and
electronics/gs8-d2-v1/WIRING.md s7. Read-only review; no CAD rebuild. Geometry from `layout.py` (imported), the r6
`out/checks.json` (16:05 build) and the per-part STEP files in `out/step/parts/` (assembly pose). Scripts: session
scratchpad `blockers/` (not in the repo).

## Verdict

**1 BLOCKER, 4 MAJOR, 12 MINOR, 16 CLEARED.** The D2 can be assembled, but not exactly as written. The one blocker is step 6: the HDMI plug cannot be mated outside the body and then slid in with the EVF pair. The mated plug hits the tub's EVF bottom rail about 24.5 mm before home. The `evf_pair_in` sweep missed this because the plug is not in its moving set (BX-1). The same clash blocks service item 7 in reverse. The four MAJOR items each need a sequence or hardware change in the guide. (BX-2) The 150 mm QT lead is too short to plug the encoder with the panel held "beside the body". (BX-3) Mating the XT30 at the grip mouth is not length-checked, and the step-1 tie "to a standoff" can leave the junction about 28 mm inside the bay. (BX-4) The step-8 hold "by the metal lens mount" has no clean grip: the 10 mm housing band sits between the front wall and a PCB/cover that stand proud of it, with about 6 mm free below it. (BX-5) Pressing knob_exp on at step 9 loads only the encoder's 0.4 mm cradle hooks, with nothing behind them. The straight-driver rule holds: all 11 screws (including s_c1..s_c4, s_j, s_k1 and s_k2) are computed at their own step in the tool-13 envelope (C-1). No solder joint is needed after the body is closed. Everything here is computed or estimated from CAD proxies: nothing was printed or bought, and no hand ever entered the model.

## Findings

| id | class | step | finding | evidence | fix / guide wording |
|---|---|---|---|---|---|
| BX-1 | BLOCKER | 6 (and s7 item 7) | The EVF board cannot slide home with the HDMI plug already mated "outside the body". The mated right-angle plug hangs below the board's lower edge (ko_hdmi_evf: x -144.8..-136.8, z 52..63.8). On the -Y 45 slide it meets the tub's EVF bottom rail. The rail is gapped only at y 3..18 (gap 4..17 + 1.0 clear), and its body below the groove floor stays full width from y 18 to its end at y 28.5. The plug stops about 24.5 mm before home. | Swept the ko_hdmi_evf section along `evf_pair_in` (y 4 -> 62) against `out/step/parts/tub.step`: 63.3 mm3 of tub, bbox x -139.95..-136.8, y 18.0..28.5, z 61.5..63.75. Hood: 0. Final pose (y 4..17): 0. The `sweeps` row for `evf_pair_in` passes only because its moving set is `hmx039` + `evf_board`: the plug is not in it, and ko_hdmi_evf is not in that sweep's keep-out list. printed_tub.py:290-330: the "no -X groove wall beyond g0" cut is only z zf..zf+dep, so the rail body below zf stays. | CAD: extend the bottom-rail cut under the plug's x span (x <= px1) over the full rail height from g1 to yend (keep the +X spine), and add the mated plug (ko_hdmi_evf box) to the `evf_pair_in` moving set. Guide, until fixed: mate only the OLED flex outside. Slide the pair home, then plug the HDMI upward into the board through the rail gap (y 4..17) from the open left side; check by hand that this works on the first print. |
| BX-2 | MAJOR | 8 | QT lead too short for "hold the panel beside the body" while plugging the JST-SH into the encoder. The lead is dressed at step 4 along the right wall and across behind the blower inlet. The estimate stops at the encoder envelope (z 44), not at the socket. The modelled QT sockets are on the encoder back at mid-height (z 54..60), about 14-17 mm further along the lead. So the free end reaches only about 0-7 mm past its final socket position, or about 15-22 mm if the 15 mm end allowance is used up. The socket sits about 8-12 mm inside the panel's inner face. The panel can therefore be held only about 15-20 mm off its seat: a slot too narrow for fingers to push a 1.0 mm-pitch JST-SH home. Nothing computes this pose. | `cable_routes` row qt: length 150, est 117.6, allowance 15, slack 17.4, end_gap 0.2 to the encoder box. Route ends at ko_lead_cross (x -84..-74, y up to 20, z up to 44). cots.py:271: QT sockets at x -72.5 / -53.5, y 19.6..24.1, z 54..60. Split plane y 32.2. No check models a panel-off mating pose (grep: no hand/reach check in checks.py). | Best: a 200-300 mm JST-SH-to-socket lead (re-run `cable_routes` with slack >= 40 mm), coiled in ko_lead_cross. Guide, with the 150 mm lead: before step 5, leave the cross run loose (not tied), pull the QT end out, tilt the panel out from its bottom edge (lip side) about 25 deg rather than holding it off parallel, plug the JST-SH with tweezers backing the socket, then fold the lead back while the panel goes on. Mate the 18/24 PH (slack 47.7 mm) first. |
| BX-3 | MAJOR | 1, 10 (s5 Fit, s7 P3-P4) | Grip-mouth XT30 mating is not length-checked, and the step-1 "strain-relief tie to a standoff" can make it impossible. Taut, the 180 mm pigtail leaves about 28.6 mm of wire past the grip mouth (no tie detour, assumed pad position). The nearest kit standoffs are 28.7 / 29.7 mm from the route's wrap point at the port edge (x -38). A tie there and back costs about 57 mm, which leaves the XT30 about 28 mm inside the bay: a blind mate in a 25 x 43 mm bay, and P4 "unplug by the housings" becomes hard. | Estimate (box-centre polyline, the `cable_routes` method): pads at ko_pig_wrap top (-38, 25.1, 10) to the pigtail-hole top 38.7 mm, then a straight drop to the bay mouth z -110 of 112.7 mm: 180 - 151.4 = 28.6 mm. `PI['holes']` standoffs (-9.5, 20.2) and (-67.5, 20.2). The pad position is open (WIRING W-1, Q2; `COTS['x1203']`). `cable_routes` checks only the final pose (slack 75.7). | Define the tie point on the route (a tie slot by ko_pig_wrap, or on the pi_keeper), not "a standoff". Or set the pigtail to about 220 mm after G-W2 locates the pads; check that the extra coil fits ko_xt30 above the pack. Add a computed "XT30 face >= 15 mm out of the grip mouth" check. Guide: at G-W2, measure pads-to-mouth with a string before cutting the pigtail. |
| BX-4 | MAJOR | 8 (also s7 6a, lens swap) | "Finger and thumb hold the camera by its metal lens mount" cannot be done as written. The reachable metal is a band 10.35 mm long (housing dia 35.5, x -17.2..-6.85). It sits between the front wall (x -5.2) and the PCB/cover, which stand 1.25 / 2.0 mm proud of it on every side (PCB 38 sq, cover 39.5 sq). A fingertip (about 14-16 mm) will also bear on the PCB/cover edge. Below the band there is about 6 mm to the cooler/exhaust (z 42.25 vs 36.3), so no thumb fits under it. The right side is reachable only by curling a finger over the top (about 19.5 mm gap to the hood roof). So the B-7 promise (no thread torque through the housing-to-PCB joint) is not physically assured. | `CAM['housing']` d 35.5 x 10.35; `cam_hf_x()` -6.85; `X_FW_IN` -5.2; `CAM['pcb']` 38, `CAM['cover']` 39.5 sq on axis (0, 60); `COTS['cooler']` z top 36.3, ko_exhaust z top 36.2; `ZT1` 97.3. | Guide: thumb on the left side of the mount band, index finger over the top and down the right side of the band. Press forward (+X) only; never squeeze the cover. Thread the lens with fingertip torque only until it stops, with no final "snug". Better (CAD): a printed "camera steady" fork for the 10 mm band, inserted from the left, or a grip flat on the BFAR. |
| BX-5 | MAJOR | 9 | Pressing knob_exp onto the encoder shaft with the panel closed loads only the 3 cradle hook teeth (0.4 mm). The press pushes the encoder inward (-Y), away from the panel face. Nothing inside the body backs the encoder: the HDMI run below it is a keep-out, and there is no hook under the PCB. A firm press fit can pop the encoder off its cradle inside the closed body; recovery means panel off (4 PT drives on the tally). | printed_small.py:38 knob note "Press onto the D shaft" (bore set by the D-bore ladder coupon, `FDM['KNOB_BORE_OFFSET']`). `ENCODER['cradle_hooks']` tooth 0.4, "no hook under the PCB (ko_hdmi_run)". | Guide: press knob_exp on at step 2 (bench, panel off), backing the encoder PCB with a thumb. The knobs then travel with the panel (the `panel_on` path stays outside the body) and "ride out on their shafts" in service (s7 item 4). knob_fps on the nut-held switch is not affected. If it stays at step 9: twist the knob on lightly; never push hard. |
| BX-6 | MINOR | 5 | The plunger has no retention while the hood plate comes down. The flange sits in a 0.4 mm recess, and the finger holding it must leave before the plate's channel reaches it, so the plunger can fall out forward. | `PLUNGER` flange in a 0.4 recess; `hood_pocket` channel open at the plate foot. | Guide: tilt the body nose-up (rest it on the rear face) so the plunger stays in by gravity, then lower the hood straight down relative to the body. |
| BX-7 | MINOR | 6 | Foam pad order is ambiguous. The pad (1.0 mm) shares the 3.0 mm OLED pocket with the OLED (1.93 mm), but the sweeps treat it as already placed (an obstacle for `eyepiece_in` and `evf_pair_in`). A loose pad has nothing to stand against before the board arrives, and a sliding OLED would drag it. | `EVF['oled_cell']` pocket x -148..-145; `COTS['foam_pad']` x -146.07..-145.07; `sweeps` obstacle lists. | Guide: stick the pad to the OLED back (or the board's -X face) first, then slide it in as part of the tethered pair. |
| BX-8 | MINOR | 7 | The 9-layer FPC S-fold (about 119 mm of slack) has to be formed in ko_fpc_loop (12.8 x 17.5 x 19.4 mm) through the open left side, under the hood, behind the camera. | `cable_routes` fpc slack 119.1; harness-schedule routing note; ko_fpc_loop. | Guide: pre-fold the S-fold on the bench (bend r >= 1, hold it with a Kapton strip) before the camera goes in; check that it does not touch the blower inlet. |
| BX-9 | MINOR | 6 | Tucking the 5 V PH junction into ko_5v_end (x -136.5..-130, y -24..1.5, z 64..70) means reaching 30-56 mm in from the left opening, under the hood, just ahead of the board that has just gone in. | KEEPOUTS ko_5v_end. | Guide: use the 120 mm tweezers. Lay the junction before the board's last 10 mm of travel. |
| BX-10 | MINOR | 4 | Header sockets are tight. The even-row Dupont housings (pin 6, 34) sit about 1.2 mm from the right-wall inner face (y -32.5), and the odd row (1/3/5, 33/37/39) about 0.7 mm from the cooler edge (y -25.55). Fingers cannot grip the housings from the sides. | `PI['y']` -32.3 edge; `Y_RW_IN` -32.5; `COTS['cooler']` y0 -25.55; ko_qt_lead / ko_run_leads. | Guide: seat each housing straight down with closed tweezer tips on its top, then pull-test each one. Single 1-pin housings (or a 1x2 for 37/39) are fine; do not use a 1x3 or 2x3 shell. |
| BX-11 | MINOR | 4 | Hold the stack by its USB end and port edge only: its right and front edges end 0.2 / 0.35 mm from the walls. The pigtail and run lead must lie flat under the X1203 (ko_pig_under / ko_run_floor, 3.1 mm tall) while the stack comes down the last 5 mm, and that space is blind. | KEEPOUTS ko_pig_under z 2.7..5.8, ko_run_floor z 2.7..5.8; `COTS['x1203']` z0 6.0. | Guide: pre-form both leads and hold them to the floor with Kapton tape. Pull the XT30 gently down from the grip mouth as the stack descends. Check 4: look under the port edge before the keeper goes in. |
| BX-12 | MINOR | 3, 8 | Driver-handle margins depend on the real torque screwdriver. The s_j handle is 2.35 mm from the strap (flexible); the s_c4 handle is 6.5 mm from the hood. | `driver` rows s_j (handle gap 2.35, strap) and s_c4 (6.5, hood); BOM D2-77 "handle dia <= 30". | Buy-check tool 13: handle dia <= 30. With a 1/4 in hex holder, use a >= 50 mm PH1 power bit whose turned shank (<= 6.5) covers at least the first 8 mm; the counterbores are dia 7, up to 6 mm deep. Hold the strap aside for s_j. |
| BX-13 | MINOR | 8 | Before the knobs are on, the encoder D shaft (to y 44) and the cut switch shaft (to y 42) stand 7-9 mm proud of the panel. Laying the body on its panel side to drive s_r1/s_r2 vertically rests it on the shafts. The eyepiece is also loose rearward until the panel's EVF cap clamps it. | `ENCODER['shaft']` y 37.2..44; step 2 cut to y 42.0; s7 item 4 (EVF cap clamps the spigot). | Guide: drive s_r1/s_r2 with the body upright (driver horizontal), or on a folded towel with a gap for the shafts. Keep the body level or nose-down between steps 6 and 8. |
| BX-14 | MINOR | 2 | Sawing the 18/24 shaft after the switch is fitted puts the hacksaw load into the nut, the anti-rotation tab and the printed panel. | Step 2 text; tool 7. | Guide: support the panel face on a block next to the shaft, or cut the shaft in a vise before fitting (7.0 above the panel face; measure the nut/washer stack). |
| BX-15 | MINOR | 7 | Thumb on the centring gauge vs the collar-screw lines: the gauge is about 44.3 dia x 24.4 long (front face about x 19.8). The s_c1/s_c2 bits pass 8 mm above its rim. The s_c3 line (y 28, z 36) passes the lower-left of the gauge face. | `out/stl/tools/collar_gauge.stl` extents 44.3 x 44.3 x 24.4; screw table. | Guide: thumb on the upper-right of the gauge face while driving s_c3; on the lower half while driving s_c1/s_c2. |
| BX-16 | MINOR | 3 | The run lead (250 mm, two Dupont sockets) has to stay clear of the tub-floor / base interface during the 10 mm slide, and is then fished blind through a 6 x 7.5 mm hole. | FLOOR_HOLES run_lead x -34..-28, y 1.5..9; BASE_OPENING; ko_run_drop z -14.2..2.7. | Guide: before the slide, let the socket end hang down the grip bay (not lying flat on the base). After s_j, push it up from the open grip mouth with a finger while the tweezers take it through the floor hole. |
| BX-17 | MINOR | s7 item 9 (service) | Hood release: the s7 text says the dia 1.5 pins "stay in by friction" in dia 1.6 holes while the hood is lifted. The deflected hook tooth pushes each pin back out along its axis, and the nominal 0.1 mm clearance gives no designed friction, so the two releases may not stay made. Then one person needs both pins held plus the hood lifted. | `HOOD_RELEASE` hole_d 1.6, pin_d 1.5, push 0.55; ASSEMBLY.md s7 item 9. | Guide: if a pin does not stay in, hold both pins with one strip of tape across the right wall (or a rubber band round the body), then lift the hood. Physical gate G-SNAP-2 should record whether the pins stay. |

### Cleared (checked, no blocker)

| id | step | point checked | result / evidence |
|---|---|---|---|
| C-1 | 3, 4, 7, 8 | Straight-driver audit really covers all 11 screws: s_b1, s_b2, s_r1, s_r2, s_k1, s_k2, s_j, s_c1..s_c4 | `checks.json` `driver`: 11/11 pass, each at its own step with that step's full present set (s_c1..s_c3 at step 7 without the lens; s_c4 at step 8 with lens and panel). Envelope: bit dia 6.5 x 40 + handle dia 30 x 100 (= tool 13 spec). Tightest: bit 0.25 mm in the dia 7 counterbores, s_c4 bit 0.75 to the collar relief. `service_driver` 11/11 pass. Note: the centring gauge is not in the s_c1..s_c3 audit set; checked by hand: rim 8 mm below the s_c1/s_c2 bits, front face about x 19.8 vs handle start x 43.3 (BX-15). |
| C-2 | 4, s7 10 | XT30 through the pigtail hole and the base / bay passage | Prism of a 10.2 x 5.2 XT30 (long side along X) through the hole footprint: tub 0 mm3. base_grip 0 down to z -20; below that the run-button cradle wall (x > -36.9) is in the way, so steer the XT30 rearward once in the bay. Long side along Y hits the tub (hole 9 mm in Y). Guide: "XT30 long side front-to-back". The sleeved fuse (OD 5) passes. |
| C-3 | 3, 4 | Run-lead Dupont ends through the 6 x 7.5 floor hole | 2 x 1-pin housings side by side (2.54 x 5.1): tub 0, base 0. A 1x3 shell (7.6 long) would not pass: keep separate sockets. |
| C-4 | 7 | FPC reach for "plug it into the camera outside the body" | 200 mm; direct CAM1-to-camera-at-start-pose distance about 41 mm; route slack 119 mm. |
| C-5 | 6 | HDMI / 5 V reach for the tethered pair at the +45 start pose | Direct distance: HDMI0 to the board plug about 114 mm (+20 allowance) of 200; USB 2 port to the board about 88 mm (+20) of 200. Reach is fine; only the plug-vs-rail clash (BX-1) blocks. |
| C-6 | 6 (alt. sequence for BX-1) | In-situ HDMI plugging from below through the rail gap | Computed (16:57): a column under the receptacle (x -146..-137, y 4..17, z 37..63.8) and the hand path from the open left side (y 4..32.2, z 40..60) hold 0 mm3 of tub, hood or pi_keeper, and no COTS box present at step 6 overlaps them. That leaves about 27 mm for plug plus fingers, before the HDMI coil is laid. Confirm by hand on the first print. |
| C-7 | 8 | 18/24 PH junction mating with the panel off | `cable_routes` fps_lead slack 47.7 mm plus the 50 mm switch pigtail: enough to mate it outside. |
| C-8 | 7 | Order of collar, gauge and camera | Collar and gauge go on with the camera out; the gauge pulls out forward (cones only); `camera_in` sweep has the collar as an obstacle and passes; s7 6b/6c reverse it (camera out before the collar). Consistent with `layout.INSERTIONS`. |
| C-9 | 8 | Lens thumb screws reachable once the lens is in the collar | KEEPOUTS ko_lens_thumb (full rings at x 13.1..16.9 and 31.7..35.5, r 24) are kept free of printed parts (`lens_support` thumb_keepouts). |
| C-10 | 3 | Tripod nut "press" | Nut AF 11.1 in pocket AF 11.4: a slip fit; the flat bar only seats it. |
| C-11 | 3 | Run cap through the grip-face hole | Cap dia 13.0 in the dia 13.6 hole. |
| C-12 | B1 | Heat-set inserts: access and backing | Tub empty, front face up; TL/TR bosses near the open top, LL merged into rib_l (x -12.1..-5.2, y 24.1..32.2, z 2.5..41), so it is backed. Collar lug insert from below with the collar off the body. |
| C-13 | 4 | FPC latch at CAM1, HDMI0 and USB 2 plugging after the keeper | ko_fpc_up / ko_hdmi_pi / ko_usb_evf are clear of the keeper (`keepouts` 97/97); access from above (top open) and from the open left side. |
| C-14 | 5 | microSD through the front slot after the hood | `sd_in` sweep passes; slot z 15.9..18.6 vs card 1.0; card tip ends about 3.5 mm inside the slot, so tweezers can push it. Guide note: check on receipt whether the Pi 5 slot is push-push. If it is, removal is "push to release", not "pull" (s6, s7 item 8). |
| C-15 | 7, 8 | Camera path past the roll fin, panel keeper finger past the FPC | `camera_in` and `panel_on` sweeps pass; keeper finger z 66..76 is clear of ko_fpc_cam (z 39.4..47) and ko_fpc_loop (z <= 56). |
| C-16 | s7 | Service order vs assembly order | s7 items 2-11 reverse steps 3-9 and `INSERTIONS`; hood needs collar off (feet through the plate); microSD out before the stack; isolation P1-P4 first. Exception: s7 item 7 ("part the HDMI outside the body") inherits BX-1. The HDMI must be unplugged through the rail gap before the pair slides out. |

## Notes

- **Method.** Clashes: a cadquery boolean of a swept box against the assembly-pose part STEP files (`out/step/parts`,
  16:05 build). Lead lengths: a polyline through the centres of the overlaps of consecutive keep-out boxes (the same
  method as `checks.check_cable_routes`), plus explicit end points. Hand access: clearances read from `layout.py`
  and the `COTS` boxes, against a fingertip of 14-16 mm and a thumb of 18-20 mm.
- **BX-1 is the only item that a printed tub would turn into a hard stop.** The cheapest unblock is a sequence
  change. Mate the OLED flex outside, slide the pair in, then plug the HDMI from below through the rail gap (C-6),
  then mate the 5 V PH. Service reverses this: unplug the HDMI through the gap first, then slide the pair out.
- **Suggested guide wording.**
  - Step 6: "Mate the OLED flex outside the body and close the latch. Slide the OLED and the board in together. Then
    push the HDMI plug up into the board through the gap under it. Then mate the 5 V junction and tuck it."
  - Step 8: "Tilt the panel out from its bottom edge. Plug the QT with tweezers."
  - Move from step 9 to step 2: "Press the exposure knob on while your thumb backs the encoder."
  - Step 10: "If the XT30 does not reach out of the grip mouth, stop. Do not mate it blind inside the bay."
- **Not checked** (no evidence in the repo, or too costly for the time box):
  - the OLED kit-flex path during the pair slide;
  - the real Pi 5 microSD slot type (push-push or friction);
  - the X1203 pad position (Q2);
  - real COTS dimensions (every envelope is a proxy until MEASURED-PARTS is filled);
  - the encoder cradle-hook pull-out force (G-ENC-1) and the knob press force (D-bore ladder coupon).
- **Prior audit items.** B-7 (lens hold) and M-V-MPS-3 (board-slot gap) were closed in text, or at the final pose
  only. BX-4 and BX-1 are new physical evidence against those closures, not re-reports.

## r7 status (2026-10-09; the record above is unchanged)

- r7: BX-1 fixed in CAD (SPEC-C1) — no geometry change: the EVF pair slides in with the HDMI unplugged, then the HDMI is plugged up through the rail gap in the body; `evf_pair_in` passes, the planted r6 order fails (60-66 mm3 of tub), new `mate_paths` check: plug path 0 mm3, every hand/tool corridor 0 mm3, 10.0 mm fingertip room; fix-up: no floor-edge lever (the tub top at z 36 is only the stick-guide block), the push comes from the guide top or straight up from the open well (`acc_hdmi_evf_push_well`, 43 mm room; tool 10 only as an upright push stick), service pliers corridor `acc_hdmi_evf_pliers_svc`; `mate_paths` 13/13 in the trial build; first-print gate G-EVF-3.
- r7: BX-7 fixed in CAD (SPEC-C1) — the foam pad is stuck to the OLED back (PSA, BOM D2-45) and moves with the pair in `evf_pair_in` and `evf_out`.
- r7: BX-9 fixed in CAD (SPEC-C1) — the 5 V PH junction is mated with the pair held about 60 mm out, rides in above the bottom rail and is pushed into `ko_5v_end` with the 120 mm tweezers once the board is home (`acc_5v_tuck` corridor 0 mm3); its reach row `usb_5v_evf` comes with MATE_POSES (SPEC-C2 slot).
- r7: C-16 fixed in CAD (SPEC-C1) — s7 item 7 now unplugs the HDMI in place first (pliers, tool 15, fingertip backing the slab), then slides the pair out, then the eyepiece; `removals` `evf_out` passes with the eyepiece as an obstacle.
- r7: BX-5 fixed in CAD (SPEC-C5) — both knobs are pressed on at bench step 2 with a thumb behind the encoder board, on a 0.2 mm paper shim, and ride in with the panel (`panel_on` sweep 0 mm3); new `handling` check: knob_exp press 0.0 mm3 on rigid parts (1.44 on the snap-tooth zones, thumb column 0.0), knob_fps rigid 15.92; physical gate G-ENC-1 pull-out >= 25 N.
- r7: BX-13 fixed in CAD (SPEC-C5) — the panel screws are driven with the camera on its hood roof on a folded cloth, a block <= 25 mm against the left side, stopped from sliding; fix-up: at the bench edge, right face within about 20 mm of it, so the s_r1/s_r2 driver handle and hand pass beyond the edge (`handling` driver-plane rule, overhang -Y 20 mm; hood_down margin 2.7, tip angle 29.2 deg); set down only on its right side (right_down_8 52.6 deg, right_down_10 39.8 deg); never on its left side, never on its grip end (it tips at about 6 deg, so base-down is hand-held); `driver` s_b1/s_b2/s_r1/s_r2 pass.
- r7: BX-14 fixed in CAD (SPEC-C5) — the 18/24 shaft is measured in place (P), then cut off the panel in soft vise jaws (P - 6.9) and the switch refitted; final 6.7-7.1 above the face, recorded at G-MP-SW.
- r7: BX-2 fixed in CAD (SPEC-C2) — the QT lead is 250 mm (240-270, Adafruit 4397 spliced to Pololu 5521, WIRING W-QT) and is plugged with the panel 60 mm off; fix-up: a helper holds the body upright, the panel is propped on a block about 110 mm tall, the PH junction is mated first with both hands (`fps_ph` two pinch boxes), then the QT plug with a fingernail push; `mate_reach` qt_enc slack 35.2 at 240 mm, hand box 0 mm3 and wholly outside the body; spares fold into `ko_lead_stow` (`cable_stow` 2288 <= 2542 mm3); `sweeps` panel_on carries the plug and passes. Physical gate G-QT-1.
- r7: BX-10 fixed in CAD (SPEC-C2) — single 1-pin header housings (a 1x2 only on 33/34 or 37/39), seated with open tweezer tips straddling the wire and tug-tested at step 4; `header_housings` gaps cooler 0.68, kit 0.75, wall 1.13, hood 2.27 (>= 0.3), plus completeness rows (each used pin exactly one housing; 10 rows pass); `ko_run_leads` widened to x -64.5. Physical gate G-HDR-1.
- r7: BX-3 fixed in CAD (SPEC-C3) — the pigtail is cut to L_cut = 200 mm + the G-W2 pads-to-W length and strain-relieved by a neutral-cure RTV bead at the pads (no standoff tie); new `lead_access` check: XT30 face 28.4 mm out of the mouth (>= 15), required length 190, cut range worst 17.4; fix-up: `pigtail_drop` stops the cut above 25 mm pads-to-W (G-W5 drop 0.15 V), the junction is re-posed flat on the pack top under the run button, female end to the rear, fuse beside it (`pigtail_store` fill 0.149, exits 8.0 / 8.0 mm against 7.2), step 10 is done on the right side with the pack in the palm; `mate_reach` xt30 slack 13.4. Physical gates G-W2, G-MP-PACK (rigid XT30 exit 0.8 mm at most: to measure).
- r7: BX-11 fixed in CAD (SPEC-C3) — the pigtail leg is formed into a U at the W mark (x -37.5) and taped under the X1203 at bench step 1, so it comes down with the stack; the lane moved 0.5 off the keeper (`pigtail_wrap_clear` 0.000, `lane_separation` 1.0); `pi_in` carries the leg as riders, 0 mm3.
- r7: BX-16 fixed in CAD (SPEC-C3) — the run lead is threaded up through the base passage and the rear end of the floor hole (now x -41.5..-28) before the tub is lowered, then taped in its lane; `run_lead_window` 3.5 >= 3.2 at the start of the slide; base_grip STL unchanged.
- r7: BX-4 fixed in CAD (SPEC-C4) — the hood roll fin is replaced by a two-tine tab catch, so the camera's metal lock tab takes the lens-thread torque and nobody holds the camera; new `roll_catch` check: first contact 3.25 deg (1.76..4.77), cover/PCB never first, window 0.679 / 0.129; fix-up: step 8 turns lens and camera back off the tine before s_c4 (`lens_turn_back_lint`), the step-10 level check is done every time, `lens_hold_lint` also scans the guide, and `roll_catch` is in the audit's expected categories; physical gates G-CAM-1 (head side), G-CAM-2.
- r7: not fixed in CAD this round: BX-6, BX-12, BX-17 (SPEC-C6 not landed), BX-15 (SPEC-C4 5b: its part-done hunks were rolled back at the release, so the collar gauge stays the r6 part) and BX-8 (SPEC-C4 5c, not landed). Their interim tips stay on guide pages 3b, 5a, 7a, 7b and B0.
