AubergineShallow/digital8mm/audit/d2-readiness-2026-10-05-r3/rebuild-fr1/renders/section-evf-board-z78.png

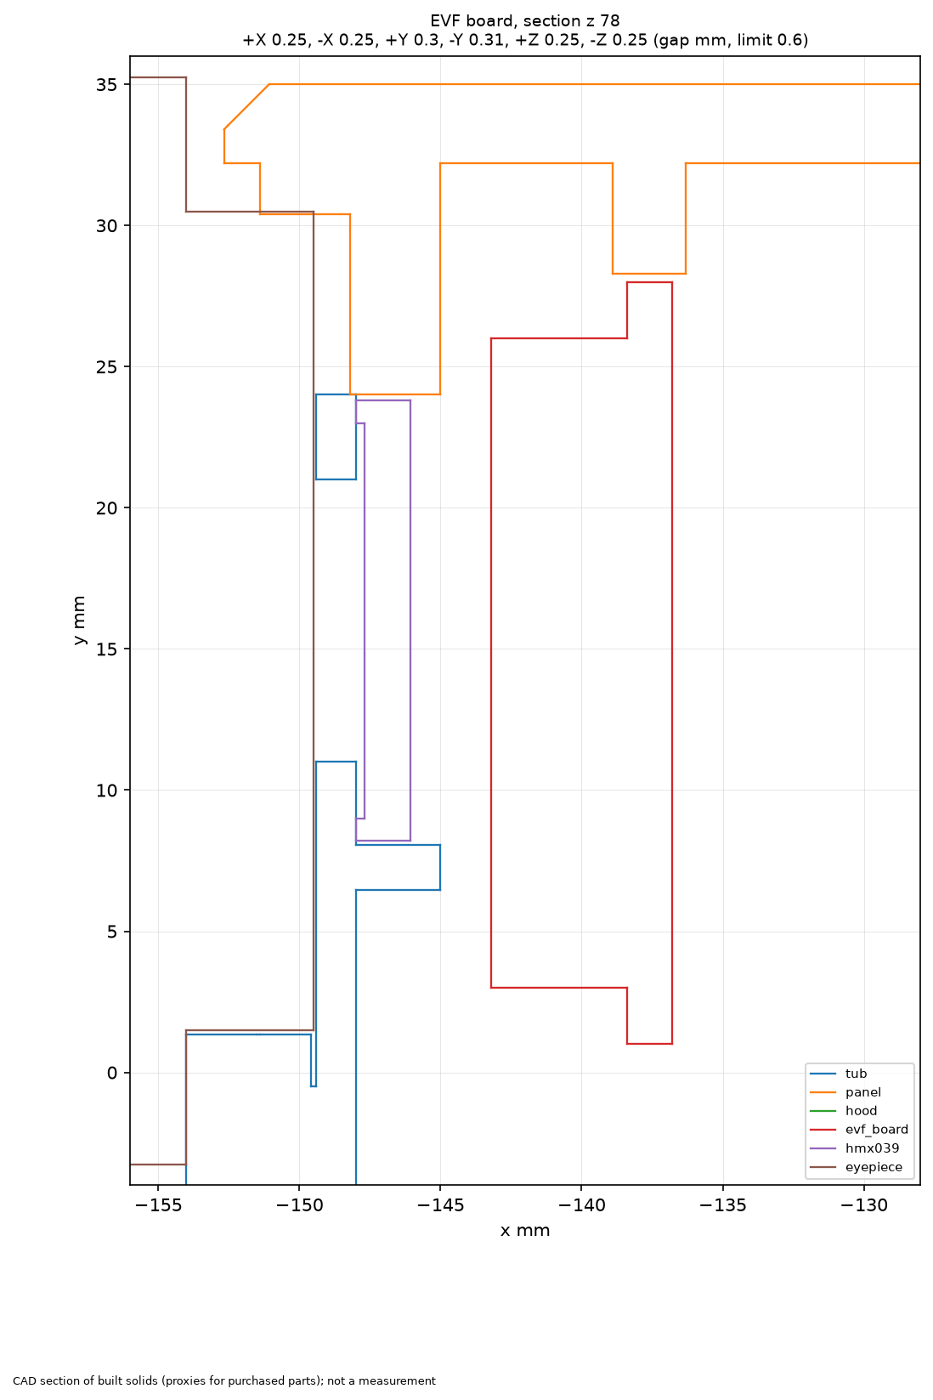
audit/d2-readiness-2026-10-05-r3/rebuild-fr1/renders/section-evf-board-z78.png
