AubergineShallow/digital8mm/audit/d2-readiness-2026-10-06/rebuild-kowa/renders/section-j7-z90.png

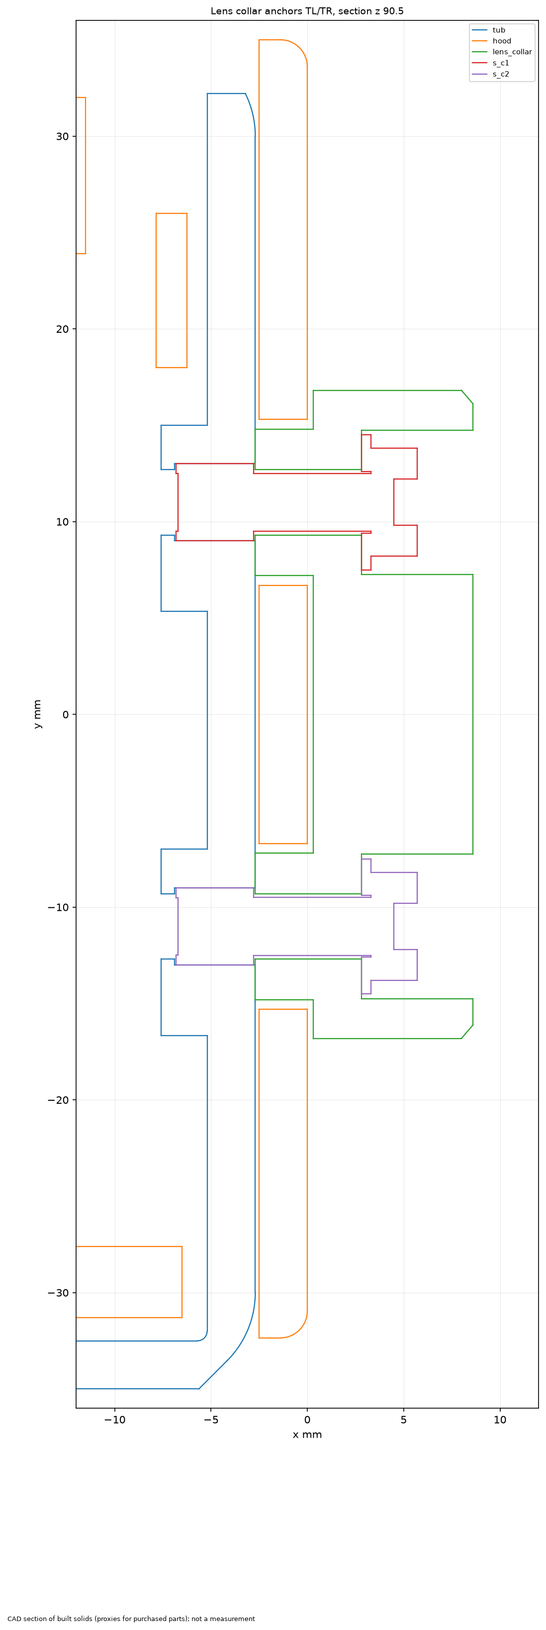
audit/d2-readiness-2026-10-06/rebuild-kowa/renders/section-j7-z90.png
