AubergineShallow/digital8mm/cad/gs8-d2-v1/checks.py

# SPDX-License-Identifier: MIT
"""GS8 D2: assembly checks (SPEC.md section 6). Pure functions over a row table; build_d2.py calls them.

rows: {id: dict(shape=cq.Shape (assembly frame, final pose), kind='printed'|'cots'|'hardware', stub=bool, ...)}
Every check returns dict(check=..., status='pass'|'fail'|'stub'|'info', ...). 'stub' means a printed module is not
written yet and its envelope box stands in: the result is computed but cannot pass. Only computed checks say pass;
purchased parts are proxies; nothing is printed, bought or measured.
"""
import math

import cadquery as cq
import numpy as np

import d2_common as dc

V = cq.Vector
VOL_TOL = 0.05            # mm3, exact OCP boolean (SPEC s6.1)
SWEEP_TOL = 0.5           # mm3, mesh boolean on tessellations (tolerance 0.05 mm)
CARRY_SOFT_MM = 1.0       # r7 C1: a carried rigid plug may press a 'cable' keep-out (flexible bundle) this deep
MESH_TOL, MESH_ANG = 0.05, 0.2

# Cable ends as COTS ids (derived from layout.CABLES frm/to text; see NOTES.md interface request).
CABLE_ENDS = {'fpc': ('pi5', 'gs_camera'), 'hdmi': ('pi5', 'evf_board'), 'usb_5v': ('pi5', 'evf_board'),
              'oled_flex': ('hmx039', 'evf_board'), 'qt': ('encoder', 'pi5'), 'run_lead': ('run_button', 'pi5'),
              'fps_lead': ('switch_1824', 'pi5'), 'pigtail': ('x1203', 'xt30_pair'), 'pack_lead': ('pack', 'xt30_pair')}


def _r(x, n=3):
    return None if x is None else round(float(x), n)


def bb_tuple(shape):
    b = shape.BoundingBox()
    return (b.xmin, b.xmax, b.ymin, b.ymax, b.zmin, b.zmax)


def bb_overlap(a, b, m=0.0):
    return a[0] < b[1] + m and b[0] < a[1] + m and a[2] < b[3] + m and b[2] < a[3] + m and a[4] < b[5] + m and b[4] < a[5] + m


def box_bb(b):
    return (b['x'][0], b['x'][1], b['y'][0], b['y'][1], b['z'][0], b['z'][1])


def common(a, b):
    """Exact OCP boolean common; returns (volume, shape or None)."""
    try:
        c = a.intersect(b)
        v = c.Volume()
        return v, (c if v > 1e-9 else None)
    except Exception as e:     # noqa: BLE001
        return float('nan'), str(e)


# ------------------------------------------------------------------------------------------- mates
def mate_table(L):
    t = {}
    for a, b, kind in L.MATES:
        t[frozenset((a, b))] = kind
    return t


def screw_pierces(L):
    """{screw id: set of part ids it is allowed to pierce} = joins + the part named first in 'into'."""
    out = {}
    for s in L.SCREWS:
        out[s['id']] = set(s['joins']) | {s['into'].split()[0]}
    return out


# ------------------------------------------------------------------------------------------- 1. interference
def check_interference(L, rows):
    mates = mate_table(L)
    pierce = screw_pierces(L)
    ids = [i for i in rows if rows[i].get('shape') is not None]
    bbs = {i: bb_tuple(rows[i]['shape']) for i in ids}
    out = []
    for n, a in enumerate(ids):
        for b in ids[n + 1:]:
            if not bb_overlap(bbs[a], bbs[b]):
                continue
            kind = mates.get(frozenset((a, b)))
            sa, sb = a.startswith('s_'), b.startswith('s_')
            if (sa and b in pierce[a]) or (sb and a in pierce[b]):
                continue                                   # PT screw in its pilot (exempt by id prefix s_)
            if sa and sb:
                continue
            allowed = None
            if kind is not None:
                if kind.startswith('interference'):
                    allowed = float(kind.split()[1])
                else:
                    continue                               # contact / slide / clearance / press / thread: excluded
            v, cs = common(rows[a]['shape'], rows[b]['shape'])
            stub = rows[a].get('stub') or rows[b].get('stub')
            row = dict(pair=[a, b], mate=kind, volume_mm3=_r(v, 4))
            if isinstance(cs, str):
                row.update(status='fail', error=cs)
            elif allowed is not None:
                # thin-layer depth estimate: 2 V / A (a crush layer of thickness t over footprint S has V = S t,
                # A ~ 2 S); exact enough to tell a 0.1 crush from a real clash
                depth = 0.0 if cs is None else 2.0 * v / max(1e-9, cs.Area())
                row.update(allowed_depth=allowed, depth=_r(depth), method='depth = 2 V / A of the common solid')
                row['status'] = 'pass' if depth <= allowed + VOL_TOL else 'fail'
            else:
                row['status'] = 'pass' if v <= VOL_TOL else 'fail'
                if cs is not None:
                    row['where'] = [_r(x, 2) for x in bb_tuple(cs)]
            if stub:
                row['status'] = 'stub'
            if row['status'] != 'pass' or allowed is not None:
                out.append(row)
            else:
                out.append(dict(pair=[a, b], status='pass', volume_mm3=row['volume_mm3']))
    return out


def check_mate_overlap(L, rows):
    """Declared contact / slide / clearance mates may touch but not overlap: volume <= VOL_TOL (SPEC s6.1 excludes
    them from check 1; this is the stricter companion check). The two control-knob D bores have positive
    nominal clearance even though actual printed retention is coupon-fit ('press'); their proxies must not overlap."""
    out = []
    for a, b, kind in L.MATES:
        k = kind.split()[0]
        nominal_control = frozenset((a, b)) in (frozenset(('knob_exp', 'encoder')),
                                                frozenset(('knob_fps', 'switch_1824')))
        if k not in ('contact', 'slide', 'clearance') and not nominal_control:
            continue
        if rows.get(a, {}).get('shape') is None or rows.get(b, {}).get('shape') is None:
            continue
        if not bb_overlap(bb_tuple(rows[a]['shape']), bb_tuple(rows[b]['shape'])):
            out.append(dict(pair=[a, b], mate=kind, volume_mm3=0.0, status='pass'))
            continue
        v, cs = common(rows[a]['shape'], rows[b]['shape'])
        row = dict(pair=[a, b], mate=kind, volume_mm3=_r(v, 4))
        row['status'] = 'pass' if v <= VOL_TOL else 'fail'
        if cs is not None and not isinstance(cs, str):
            row['where'] = [_r(x, 2) for x in bb_tuple(cs)]
        if rows[a].get('stub') or rows[b].get('stub'):
            row['status'] = 'stub'
        out.append(row)
    return out


# ------------------------------------------------------------------------------------------- 2. clearance zones
def clearance_zones(L):
    """(name, part a, part b, zone box (x0,x1,y0,y1,z0,z1), stated clearance)."""
    Z = []
    hk = L.HOOK
    zlo, zhi = L.ZT1 - hk['length'] - 3.5, L.ZT1 - 0.5
    for h in L.HOOD_HOOKS:
        half = hk['w'] / 2 + 1.5
        if h['wall'] == 'right':
            zb = (h['x'] - half, h['x'] + half, h['y_face'] - 0.5, h['y_face'] + 4.0, zlo, zhi)
        elif h['wall'] == 'front':
            zb = (h['x_face'] - 4.0, h['x_face'] + 0.5, h['y'] - half, h['y'] + half, zlo, zhi)
        else:
            zb = (h['x_face'] - 0.5, h['x_face'] + 4.0, h['y'] - half, h['y'] + half, zlo, zhi)
        Z.append(('J1 hook %s to ledge' % h['id'], 'hood', 'tub', zb, hk['play']))
    g = L.HOOD_RAIL['box']
    Z.append(('J2 panel tongue in hood groove', 'hood', 'panel',
              (g['x'][0] - 1, g['x'][1] + 1, g['y'][0] - 0.5, L.SPLIT - 0.1, g['z'][0] - 0.5, L.ZT1 - 0.05), L.SL))
    for t in L.TONGUES:
        p = t['base_pocket']
        Z.append(('J4 %s in base pocket' % t['id'], 'tub', 'base_grip',
                  (p['x'][0] - 1, p['x'][1] + 1, p['y'][0] - 1, p['y'][1] + 1, p['z'][0] - 0.5, -0.05), L.SL))
    ly, lz = L.LENS_AXIS
    # r5 step 1 (J7-R; minimum change to keep checks.py running: CAM 'wall_bore_d'/'ring' and HOOD 'turret_b' are gone).
    #     The 2 "camera ring in tub/hood bore" zones (premise: a dia 36 ring in dia 36.5 bores, wrong camera model) are
    #     replaced by the real-stack equivalents of judge 3 s6.9: BFAR in the tub counterbore (stated = lip gap 0.5, the
    #     axial catch; radial 0.75), adapter in the tub lip (0.825), adapter in the hood plate bore (2.875).
    C = L.CAM
    rc = C['cb_d'] / 2 + 0.5
    Z.append(('J7 BFAR in tub counterbore', 'gs_camera', 'tub',
              (C['cb_x'][0] - 0.25, C['lip_x'] + 0.3, ly - rc, ly + rc, lz - rc, lz + rc), C['lip_gap']))
    rl = C['lip_d'] / 2 + 1.0
    Z.append(('J7 adapter in tub lip', 'c_cs_adapter', 'tub',
              (C['lip_x'] + 0.05, L.XT1 - 0.05, ly - rl, ly + rl, lz - rl, lz + rl),
              round(C['lip_d'] / 2 - C['adapter']['d'] / 2, 4)))
    rb = L.HOOD['bore_d'] / 2 + 1.0
    Z.append(('J7 adapter in hood plate bore', 'c_cs_adapter', 'hood',
              (L.HOOD['plate_x'][0] + 0.05, L.HOOD['plate_x'][1] - 0.05, ly - rb, ly + rb, lz - rb, lz + rb),
              round(L.HOOD['bore_d'] / 2 - C['adapter']['d'] / 2, 4)))
    hb = L.HOOD['housing']
    Z.append(('J8 eyepiece barrel in housing', 'eyepiece', 'hood', box_bb(hb), L.EVF['diopter_clear']))
    K = getattr(L, 'PI_KEEPER', None)
    if K is not None and 'pi_keeper' in L.PARTS:      # FIXER r2 (M-V-MPS-8): panel bosses slide under the keeper bridge
        bb = K['bridge']
        Z.append(('J9 keeper bridge over panel bosses', 'pi_keeper', 'panel',
                  (bb['x'][0], bb['x'][1], bb['y'][0], bb['y'][1], bb['z'][0] - 1.0, bb['z'][0] + 1.0), L.SL))
    pb = L.PI_BUTTON
    Z.append(('J10 plunger nib to Pi button', 'plunger', 'pi5',
              (pb['x_face'] - 0.6, L.PLUNGER['nib']['a'][1] + 0.2, pb['y'] - 3.0, pb['y'] + 3.0, 18.0, 24.5),
              L.PLUNGER['nib']['a'][0] - pb['x_face']))
    return Z


def check_clearances(L, rows):
    out = []
    for name, a, b, zb, stated in clearance_zones(L):
        row = dict(check=name, pair=[a, b], zone=[_r(x, 2) for x in zb], stated=stated, need=_r(0.9 * stated))
        if a not in rows or b not in rows or rows[a].get('shape') is None or rows[b].get('shape') is None:
            row.update(status='n/a', error='partner not in this run')
            out.append(row)
            continue
        zs = cq.Solid.makeBox(zb[1] - zb[0], zb[3] - zb[2], zb[5] - zb[4], V(zb[0], zb[2], zb[4]))
        pa, pb_ = rows[a]['shape'].intersect(zs), rows[b]['shape'].intersect(zs)
        if pa.Volume() < 1e-6 or pb_.Volume() < 1e-6:
            row.update(status='stub' if (rows[a].get('stub') or rows[b].get('stub')) else 'fail',
                       error='feature absent in zone (%s %.3f, %s %.3f mm3)' % (a, pa.Volume(), b, pb_.Volume()))
            out.append(row)
            continue
        v, _ = common(pa, pb_)
        d = 0.0 if v > VOL_TOL else pa.distance(pb_)
        row.update(min_gap=_r(d), overlap_mm3=_r(v, 4))
        row['status'] = 'pass' if d >= 0.9 * stated - 1e-6 else 'fail'
        if rows[a].get('stub') or rows[b].get('stub'):
            row['status'] = 'stub'
        out.append(row)
    return out


# ------------------------------------------------------------------------------------------- 3. keep-outs
def check_keepouts(L, rows):
    out = []
    for pid, r in rows.items():
        if r.get('kind') != 'printed' or r.get('shape') is None:
            continue
        sbb = bb_tuple(r['shape'])
        for kid, kb in L.KEEPOUTS.items():
            if not bb_overlap(sbb, box_bb(kb), -1e-6):
                continue
            v, _ = common(r['shape'], dc.box_solid(kb))
            st = 'pass' if v <= VOL_TOL else ('stub' if r.get('stub') else 'fail')
            out.append(dict(part=pid, keepout=kid, volume_mm3=_r(v, 4), status=st))
    return out


# ------------------------------------------------------------------------------------------- 3b. cable routes (r4)
ROUTE_PASSAGE = 1.0          # consecutive route boxes must share a patch >= this in 2 axes (no gap, no edge touch)
ROUTE_END_TOL = 1.0          # each chain end box must reach (gap <= this) one of the cable's two end parts
ROUTE_ALLOWANCE = (10.0, 0.10)   # service allowance: max(10 mm, 10 % of the cable length)


def _ko(b):
    return [b['x'][0], b['x'][1], b['y'][0], b['y'][1], b['z'][0], b['z'][1]]


def _box_gap(a, b):
    """Largest axis gap between 2 boxes (<= 0 = they touch or overlap)."""
    return max(max(a[2 * i], b[2 * i]) - min(a[2 * i + 1], b[2 * i + 1]) for i in range(3))


def check_cable_routes(L):
    """r4 (wiring maturity): every cable in L.CABLES with a route ('via' keep-out chain) is checked on the boxes alone:
    (a) each pair of consecutive boxes overlaps with a passage >= ROUTE_PASSAGE in 2 axes; (b) the first and last box
    reach the cable's two end parts (CABLE_ENDS, COTS boxes) within ROUTE_END_TOL; (c) an ESTIMATED route length (a
    polyline from the first box centre through the centres of the box-to-box overlaps to the last box centre, plus half
    the largest dimension of each end box) plus a service allowance is within the cable length. Bend radius is NOT
    checked here (the boxes do not carry the cable's path inside them): it stays with the bench gates (G-HDMI,
    MEASURED-PARTS). A direct plug-to-plug lead (no via) is 'info'."""
    out = []
    for c in registry(L, 'CABLES'):
        via = list(c.get('via') or [])
        row = dict(cable=c['id'], length_mm=c['length'], via=via)
        if not via:
            out.append(dict(row, status='info', note='direct plug-to-plug lead, no modelled route (%s)'
                            % ' - '.join(c.get('ends') or ())))
            continue
        missing = [k for k in via if k not in L.KEEPOUTS]
        if missing:
            out.append(dict(row, status='fail', error='route boxes not in KEEPOUTS: ' + ', '.join(missing)))
            continue
        bs = [_ko(L.KEEPOUTS[k]) for k in via]
        probs = []
        for (ka, a), (kb, b) in zip(zip(via, bs), zip(via[1:], bs[1:])):
            ov = [min(a[2 * i + 1], b[2 * i + 1]) - max(a[2 * i], b[2 * i]) for i in range(3)]
            if min(ov) < -1e-6:
                probs.append('%s -> %s: gap %.2f mm' % (ka, kb, -min(ov)))
            elif sorted(ov)[1] < ROUTE_PASSAGE - 1e-6:
                probs.append('%s -> %s: passage only %.2f x %.2f mm' % (ka, kb, sorted(ov)[1], sorted(ov)[2]))
        est = _route_polyline(L, via)[0]
        allow = max(ROUTE_ALLOWANCE[0], ROUTE_ALLOWANCE[1] * c['length'])
        # r7 C2 (SPEC-C2 3.2-2): plug-point rule. A cable with a MATE_POSES plug point (W, or far for an inline row) must
        #     end its chain at that point, not only at the end part's (whole-board) COTS box.
        ppd = None
        for mp in getattr(L, 'MATE_POSES', None) or []:
            if mp.get('cable') != c['id'] or mp.get('both_moving') or not (mp.get('W') or mp.get('far')):
                continue
            pp = _plug_point(L, mp.get('W') or mp.get('far'))
            d = _pt_box_dist(pp, bs[-1])
            ppd = d if ppd is None else max(ppd, d)
            if d > ROUTE_END_TOL + 1e-9:
                probs.append('last box %s ends %.2f mm from the %s plug point %s (> %.1f)'
                             % (via[-1], d, mp['id'], [_r(x, 2) for x in pp], ROUTE_END_TOL))
        if est + allow > c['length'] + 1e-6:
            probs.append('estimated route %.1f + allowance %.1f > cable length %d mm' % (est, allow, c['length']))
        ends = [e for e in (c.get('ends') or ()) if (L.COTS.get(e) or {}).get('box')]
        end_gap = None
        if len(ends) != 2:
            probs.append('end parts with a box: %s (need 2)' % ends)
        else:
            e0, e1 = (_ko(L.COTS[e]['box']) for e in ends)
            end_gap = min(max(_box_gap(bs[0], e0), _box_gap(bs[-1], e1)),
                          max(_box_gap(bs[0], e1), _box_gap(bs[-1], e0)))
            if end_gap > ROUTE_END_TOL:
                probs.append('chain ends %.1f mm from its end parts %s' % (end_gap, ', '.join(ends)))
        row.update(est_route_mm=_r(est, 1), allowance_mm=_r(allow, 1), slack_mm=_r(c['length'] - est - allow, 1),
                   end_gap_mm=None if end_gap is None else _r(end_gap, 2), problems=probs,
                   status='fail' if probs else 'pass', estimate=True)
        if ppd is not None:
            row['plug_point_mm'] = _r(ppd, 2)          # r7 C2
        if probs:
            row['error'] = '; '.join(probs)
        out.append(row)
    return out


# ------------------------------------------------------------------------------------------- 3c. mating poses (r7 C2)
STOW_FILL = 0.25             # r7 C2: usable fraction of a stow box for a folded lead bundle (design value; G-QT-1)
STOW_BLOWER_MIN = 2.0        # r7 C2: plan distance of a stow box from the cooler blower footprint
STOW_INFO_HOME = {'fpc': 'ko_fpc_loop S-fold by design (home check: cable_routes fpc fold row, SPEC-C4; P2-6)',
                  'hdmi': 'ko_hdmi_coil'}
MATE_POSE_TOL = 0.01         # r7 C2: a mating pose must lie on its insertion's path polyline within this
TAIL_D = 3.0                 # r7 C2: lead tail tested as a dia 3 cylinder from the anchor point to the plug


def _route_polyline(L, via, end_point=None):
    """r7 C2 (SPEC-C2 3.2-1): the cable_routes length estimate. end_point None: first box centre -> centres of the
    box-to-box overlaps -> last box centre, plus half the largest dimension of each end box (the r4 estimate, exact).
    With a point: the polyline ends at the point of the last box nearest to it (clamp) instead of adding its half.
    -> (length, points, last-box point)"""
    bs = [_ko(L.KEEPOUTS[k]) for k in via]
    pts = [[(bs[0][2 * i] + bs[0][2 * i + 1]) / 2 for i in range(3)]]
    for a, b in zip(bs, bs[1:]):
        pts.append([(max(a[2 * i], b[2 * i]) + min(a[2 * i + 1], b[2 * i + 1])) / 2 for i in range(3)])

    def half(b):
        return max(b[1] - b[0], b[3] - b[2], b[5] - b[4]) / 2
    if end_point is None:
        last = [(bs[-1][2 * i] + bs[-1][2 * i + 1]) / 2 for i in range(3)]
        tail = half(bs[0]) + half(bs[-1])
    else:
        last = [min(max(end_point[i], bs[-1][2 * i]), bs[-1][2 * i + 1]) for i in range(3)]
        tail = half(bs[0])
    pts.append(last)
    return sum(math.dist(p, q) for p, q in zip(pts, pts[1:])) + tail, pts, tuple(last)


def _pt_box_dist(p, b):
    """Distance from point p to box b = (x0, x1, y0, y1, z0, z1)."""
    return math.sqrt(sum(max(b[2 * i] - p[i], 0.0, p[i] - b[2 * i + 1]) ** 2 for i in range(3)))


def _plug_point(L, spec):
    """r7 C2: a MATE_POSES plug point. Numbers as given; ('qt_socket', i): wire exit W of the SH plug in encoder socket
    i (the layout.qt_plug_point formula on L.ENCODER / L.PLUG, so moved data moves it); ('switch_lugs',): (SWITCH_1824
    c x, body a0, c z)."""
    if isinstance(spec[0], str):
        if spec[0] == 'qt_socket':
            e = L.ENCODER
            q, pl = e['qt_socket'], L.PLUG['jst_sh_4']
            i = spec[1] if len(spec) > 1 else 0
            return (e['c'][0] + q['dx'][i] - q['w'] / 2 - pl['len'], (q['y0'] + e['pcb']['y'][0]) / 2, e['c'][1])
        if spec[0] == 'switch_lugs':
            sw = L.SWITCH_1824
            return (sw['c'][0], sw['body']['a'][0], sw['c'][1])
        raise ValueError('unknown plug point %r' % (spec,))
    return tuple(float(x) for x in spec)


def _on_path(path, d, tol=MATE_POSE_TOL):
    for a, b in zip(path, path[1:]):
        ab = [b[i] - a[i] for i in range(3)]
        n2 = sum(x * x for x in ab)
        t = 0.0 if n2 == 0 else max(0.0, min(1.0, sum((d[i] - a[i]) * ab[i] for i in range(3)) / n2))
        if math.dist(d, [a[i] + ab[i] * t for i in range(3)]) <= tol:
            return True
    return False


def _cross(a, b):
    return (a[1] * b[2] - a[2] * b[1], a[2] * b[0] - a[0] * b[2], a[0] * b[1] - a[1] * b[0])


def _hand_box(rear, axis, row, env):
    """r7 C2: hand envelope (a, t, r): a behind `rear` along -axis, t along axis x row, r along row, centred on the
    line; returned as the axis-aligned box of its corners (exact for axis-aligned axis/row, larger otherwise)."""
    a, t, r = env
    nrm = math.sqrt(sum(x * x for x in axis)) or 1.0
    ax = [x / nrm for x in axis]
    th = _cross(ax, row)
    cs = [[rear[i] - sa * a * ax[i] + st * t * th[i] + sr * r * row[i] for i in range(3)]
          for sa in (0.0, 1.0) for st in (-0.5, 0.5) for sr in (-0.5, 0.5)]
    return tuple(f(c[i] for c in cs) for i in range(3) for f in (min, max))


def _out_of_mm(box, out_of):
    """(signed axis, plane, margin): how far the whole box lies beyond plane + margin on that side (>= 0 holds)."""
    sgn, ax = out_of[0][0], 'xyz'.index(out_of[0][1])
    return (box[2 * ax] - out_of[1] - out_of[2]) if sgn == '+' else (out_of[1] - out_of[2] - box[2 * ax + 1])


def _pose_targets(L, rows, n, disp, exclude, cache):
    """r7 C2: parts present at insertion n's step (later same-step movers absent), its moving set displaced by disp:
    COTS parts as their boxes, printed parts and screws as their shapes (only when rows is given).
    -> [(id, manifold, bbox)]"""
    import manifold3d as m3
    ins = L.INSERTIONS[n]
    later = set()
    for o in L.INSERTIONS[n + 1:]:
        if o['step'] == ins['step']:
            later |= set(o['moving'])
    mv = set(ins['moving'])
    out = []
    for i in L.present_at(ins['step']):
        if i in later or i in exclude:
            continue
        d = tuple(disp) if i in mv else (0.0, 0.0, 0.0)
        cb = (L.COTS.get(i) or {}).get('box')
        if cb is not None:
            b = box_bb(cb)
        elif rows is not None and (rows.get(i) or {}).get('shape') is not None:
            b = bb_tuple(rows[i]['shape'])
        else:
            continue
        b = (b[0] + d[0], b[1] + d[0], b[2] + d[1], b[3] + d[1], b[4] + d[2], b[5] + d[2])
        if cb is not None:
            out.append((i, _bb_cube(m3, b), b))
            continue
        if i not in cache:
            cache[i] = manifold_of(rows[i]['shape'])
        out.append((i, cache[i].translate(list(d)), b))
    return out


def _tail_manifold(p0, p1, d=TAIL_D):
    import manifold3d as m3
    import numpy as np
    u = np.array(p1, float) - np.array(p0, float)
    h = float(np.linalg.norm(u))
    if h < 1e-6:
        return None
    u /= h
    e1 = np.cross(u, [1.0, 0, 0] if abs(u[0]) < 0.9 else [0, 1.0, 0])
    e1 /= np.linalg.norm(e1)
    e2 = np.cross(u, e1)
    mat = np.column_stack([e1, e2, u, np.array(p0, float)])
    return m3.Manifold.cylinder(h, d / 2, d / 2, 16).transform(mat)


def _hits_of(m, mbb, targets, tol=SWEEP_TOL):
    out = []
    for o, om, obb in targets:
        if not bb_overlap(mbb, obb, -1e-6):
            continue
        v = (m ^ om).volume()
        if v > tol:
            out.append(dict(obstacle=o, volume_mm3=_r(v, 2)))
    return out


def check_mate_reach(L, rows=None, cache=None):
    """r7 C2 (SPEC-C2 3.2-3 + Plan edits P2-1/P2-4/P2-5): one row per MATE_POSES entry. Pose on the insertion path;
    reach with checks.reach_margin (plug rows: length_min - fixed - tail - margin >= 0; inline rows: r1 + r2 >= d and
    the junction window midpoint >= junction_out beyond the opening); an oriented hand envelope and a dia 3 tail path
    against every part present in the mating pose (COTS boxes always, printed shapes when rows is given; <= SWEEP_TOL);
    the whole hand box beyond the opening (out_of). Sub-results named in a row's `info` are reported, not failed."""
    import manifold3d as m3
    cache = {} if cache is None else cache
    cab = {c['id']: c for c in L.CABLES}
    out = []
    for mp in getattr(L, 'MATE_POSES', None) or []:
        row = dict(id=mp['id'], cable=mp.get('cable'), step=mp.get('step'), insertion=mp.get('insertion'),
                   estimate=True)
        n = _ins_index(L, mp.get('insertion'))
        if mp.get('both_moving'):
            out.append(dict(row, status='info', note='both ends ride in one moving set'))
            continue
        if n is None or mp.get('cable') not in cab:
            out.append(dict(row, status='fail', error='unknown insertion or cable'))
            continue
        if mp.get('reach') == 'pigtail':
            fn = globals().get('_pigtail_mate_row')       # SPEC-C3 (S4) owns the pigtail reach model
            if fn is None:
                out.append(dict(row, status='fail', error='pigtail reach model missing (SPEC-C3 / S4)'))
                continue
            out.append(fn(L, mp, row, rows, cache))
            continue
        ins, c = L.INSERTIONS[n], cab[mp['cable']]
        disp = tuple(float(x) for x in mp['disp'])
        probs, info = [], []
        if not _on_path(ins['path'], disp):
            probs.append('mate pose %s not on the insertion path of %s' % (list(disp), ins['id']))
        lmin = (c.get('length_range') or (c['length'],))[0]
        m = reach_margin(L, lmin)
        via = list(c.get('via') or [])
        if mp.get('anchor') not in via:
            out.append(dict(row, status='fail', error='anchor %s not in the %s via' % (mp.get('anchor'), c['id'])))
            continue
        sub = via[:via.index(mp['anchor']) + 1]
        inline = bool(mp.get('inline_of') or mp.get('inline'))
        pt = _plug_point(L, mp['far'] if inline else mp['W'])
        ptd = tuple(pt[i] + disp[i] for i in range(3))
        fixed, _pts, apt = _route_polyline(L, sub, end_point=ptd)
        row.update(pose=list(disp), length_min=lmin, margin=_r(m, 1), fixed_mm=_r(fixed, 1),
                   anchor=mp['anchor'], anchor_pt=[_r(x, 2) for x in apt])
        row_ax = mp.get('row', (0, 0, 1))
        hb2 = None                                       # r7 fix-up: the far-side pinch of a two-hand inline mate
        if inline:
            pig = float(mp['pigtail']) if 'pigtail' in mp else float(c.get('pigtail') or 0.0)
            r1 = lmin - fixed - m
            r2 = max(0.0, pig - reach_margin(L, pig)) if pig > 0 else 0.0
            d = math.dist(apt, ptd)
            t0, t1 = max(0.0, d - r2), min(d, r1)
            u = [(ptd[i] - apt[i]) / d for i in range(3)] if d > 1e-9 else [0.0, 1.0, 0.0]
            mid_t = (t0 + t1) / 2
            mid = tuple(apt[i] + u[i] * mid_t for i in range(3))
            op = mp.get('opening', ('+y', L.SPLIT))
            jo = _out_of_mm((mid[0], mid[0], mid[1], mid[1], mid[2], mid[2]), (op[0], op[1], 0.0))
            row.update(r1_mm=_r(r1, 1), r2_mm=_r(r2, 1), pigtail_mm=pig, d_mm=_r(d, 1),
                       window=[[_r(apt[i] + u[i] * t0, 1) for i in range(3)], [_r(apt[i] + u[i] * t1, 1)
                                                                              for i in range(3)]],
                       window_mid=[_r(x, 1) for x in mid], junction_out_mm=_r(jo, 1),
                       slack_mm=_r(r1 + r2 - d, 1))
            if r1 < 0 or r1 + r2 < d - 1e-9:
                probs.append('junction cannot be reached: r1 %.1f + r2 %.1f < d %.1f' % (r1, r2, d))
            elif jo < mp.get('junction_out', 15.0) - 1e-9:
                probs.append('junction window midpoint %.1f beyond the opening < %.1f'
                             % (jo, mp.get('junction_out', 15.0)))
            hb = _hand_box(tuple(mid[i] + u[i] * L.HAND_ENVELOPES[mp['hand']][0] / 2 for i in range(3)), u, row_ax,
                           L.HAND_ENVELOPES[mp['hand']])
            tail_to = mid
            if mp.get('hand2'):
                # r7 fix-up (VERIFY-C2): an inline pair is mated with two hands, one pinch per housing: the body-side
                #   pinch lies behind the junction J (toward the anchor), the far-side pinch ahead of it. J is the
                #   window point nearest the midpoint at which the body-side pinch is wholly beyond the opening.
                e2 = L.HAND_ENVELOPES[mp['hand2']]
                jt = None
                tt = mid_t
                while tt <= t1 + 1e-9:
                    jp = tuple(apt[i] + u[i] * tt for i in range(3))
                    if _out_of_mm(_hand_box(jp, u, row_ax, e2), mp['out_of']) >= -1e-9:
                        jt = tt
                        break
                    tt += 0.5
                jt = t1 if jt is None else jt
                jp = tuple(apt[i] + u[i] * jt for i in range(3))
                hb_near = _hand_box(jp, u, row_ax, e2)
                hb_far = _hand_box(tuple(jp[i] + u[i] * e2[0] for i in range(3)), u, row_ax, e2)
                hb = hb_near
                hb2 = hb_far
                row.update(junction_at=[_r(x, 1) for x in jp], hand2=mp['hand2'])
                tail_to = jp
        else:
            tail = math.dist(apt, ptd)
            slack = lmin - fixed - tail - m
            row.update(tail_mm=_r(tail, 1), slack_mm=_r(slack, 1))
            if slack < -1e-9:
                probs.append('lead short by %.1f mm in the mating pose (L %d, fixed %.1f, tail %.1f, margin %.1f)'
                             % (-slack, lmin, fixed, tail, m))
            hb = _hand_box(ptd, mp['axis'], row_ax, L.HAND_ENVELOPES[mp['hand']])
            tail_to = ptd
        ex = {mp['end']}
        tg = _pose_targets(L, rows, n, disp, ex, cache)
        hh = _hits_of(_bb_cube(m3, hb), hb, tg)
        oo = _out_of_mm(hb, mp['out_of'])
        if hb2 is not None:
            hh = hh + _hits_of(_bb_cube(m3, hb2), hb2, tg)
            oo = min(oo, _out_of_mm(hb2, mp['out_of']))
            row['hand_box2'] = [_r(x, 2) for x in hb2]
        tm = _tail_manifold(apt, tail_to)
        th = [] if tm is None else _hits_of(tm, tuple(f(apt[i], tail_to[i]) + s * TAIL_D / 2 for i in range(3)
                                                      for f, s in ((min, -1), (max, 1))), tg)
        row.update(hand=mp['hand'], hand_box=[_r(x, 2) for x in hb], hand_hits=hh, out_of=list(mp['out_of']),
                   out_of_mm=_r(oo, 2), tail_hits=th, targets=len(tg), shapes=rows is not None)
        for nm, bad, msg in (('hand', hh, 'hand envelope hits %s' % ', '.join(h['obstacle'] for h in hh)),
                             ('out_of', oo < -1e-9, 'hand envelope %.2f mm short of %s' % (-oo, mp['out_of'])),
                             ('tail', th, 'tail path blocked by %s' % ', '.join(h['obstacle'] for h in th))):
            if bad:
                (info if nm in (mp.get('info') or ()) else probs).append(msg)
        if info:
            row.update(info_only=info, gate=mp.get('gate'))
        if probs:
            row['error'] = '; '.join(probs)
        out.append(dict(row, problems=probs, status='fail' if probs else 'pass'))
    return out


# ------------------------------------------------------------------------------------------- 3d. lead access (r7 C3)
LEAD_CLEAR_TOL = 0.01        # r7 C3: pigtail_wrap_clear volume tolerance (a 0.5 mm keeper sliver is < SWEEP_TOL)
LEAD_WINDOW_STEP = 0.5       # r7 C3: run_lead_window sampling along base_on


def _pig_cable(L):
    return next(c for c in L.CABLES if c['id'] == 'pigtail')


def _pigtail_path(L):
    """r7 C3 (SPEC-C3 3.2-1): W_top = (Wx, Wy + w_top_dy, ko_pig_wrap z1) -> the overlap centres of the via boxes from
    the first box to ko_pig_drop (the cable_routes polyline points, _route_polyline) -> the hole top (centre of
    FLOOR_HOLES['pigtail'], z = ko_pig_drop z1). -> (path_in length, points)"""
    P, K = L.PIGTAIL, L.KEEPOUTS
    via = list(_pig_cable(L)['via'])
    sub = via[:via.index('ko_pig_drop') + 1]
    wx, wy = P['wrap_entry']
    fh = L.FLOOR_HOLES['pigtail']
    pts = ([(wx, wy + P['w_top_dy'], K[sub[0]]['z'][1])] + [tuple(p) for p in _route_polyline(L, sub)[1][1:-1]]
           + [((fh['x'][0] + fh['x'][1]) / 2, (fh['y'][0] + fh['y'][1]) / 2, K['ko_pig_drop']['z'][1])])
    return sum(math.dist(a, b) for a, b in zip(pts, pts[1:])), pts


def _pt_seg_dist(p, a, b):
    ab = [b[i] - a[i] for i in range(3)]
    n2 = sum(x * x for x in ab)
    t = 0.0 if n2 == 0 else max(0.0, min(1.0, sum((p[i] - a[i]) * ab[i] for i in range(3)) / n2))
    return math.dist(p, [a[i] + ab[i] * t for i in range(3)])


def _pigtail_face_out(L, pad=None, length=None):
    """r7 C3 (SPEC-C3 3.2-1, Plan edits P3-1/P3-2): the ONE pigtail length model (lead_access rows 1-3 and the xt30
    MATE_POSES row). face_out = L - reach_margin(L) - d_board - path_in - drop - detour + housing_credit: how far the
    XT30 wire end (housing not credited) comes out of the grip mouth with the service allowance kept. d_board: top
    face |x - Wx| + |y - Wy|; underside Manhattan(pad, hole centre) - path_in (min 0). detour: 2 x the distance from
    the tie point to the route polyline (pad, W_top, ..., hole top); tie at='pad' gives 0."""
    P = L.PIGTAIL
    pad = P['pad'] if pad is None else pad
    Lc = float(_pig_cable(L)['length'] if length is None else length)
    path_in, pts = _pigtail_path(L)
    drop = pts[-1][2] - L.GRIP['bay']['z'][0]
    (wx, wy), (x, y) = P['wrap_entry'], pad['xy']
    top = pad.get('face', 'top') == 'top'
    d_board = abs(x - wx) + abs(y - wy) if top else max(0.0, abs(x - pts[-1][0]) + abs(y - pts[-1][1]) - path_in)
    at = (P.get('tie') or {}).get('at', 'pad')
    if isinstance(at, str):
        if at != 'pad':
            raise ValueError('PIGTAIL tie at %r: use \'pad\' or an (x, y, z) point' % (at,))
        detour = 0.0
    else:
        poly = [(x, y, L.PI['x1203_z'][1] if top else L.PI['x1203_z'][0])] + list(pts)
        detour = 2.0 * min(_pt_seg_dist(at, a, b) for a, b in zip(poly, poly[1:]))
    credit = float(P.get('housing_credit') or 0.0)
    allow = reach_margin(L, Lc)
    taut = Lc - d_board - path_in - drop - detour + credit
    return dict(length_mm=Lc, face_out_mm=taut - allow, taut_mm=taut, allowance_mm=allow, d_board_mm=d_board,
                path_in_mm=path_in, drop_mm=drop, detour_mm=detour, housing_credit_mm=credit)


def _pigtail_required_len(L, pad=None):
    """Smallest cut_round step whose face_out >= face_out_min (None if none up to 5 m)."""
    P = L.PIGTAIL
    for k in range(1, int(5000 / P['cut_round']) + 1):
        if _pigtail_face_out(L, pad, k * P['cut_round'])['face_out_mm'] >= P['face_out_min'] - 1e-9:
            return k * P['cut_round']
    return None


def _pigtail_pad_samples(L):
    """The 4 X1203 corners on both faces, the cots.py XH header estimate and the assumed pad (10 samples)."""
    P = L.PIGTAIL
    R = P['pad_range']
    out = [('%s (%.1f, %.1f)' % (f, x, y), dict(face=f, xy=(x, y))) for f in R['faces'] for x in R['x'] for y in R['y']]
    if R.get('xh'):
        out.append(('xh estimate top (%.1f, %.1f)' % tuple(R['xh']), dict(face='top', xy=tuple(R['xh']))))
    out.append(('assumed pad', dict(P['pad'])))
    return out


def _pigtail_mate_row(L, mp, row, rows, cache):
    """r7 C3 (SPEC-C3 3.2, Plan edit P3-1): the xt30 MATE_POSES row. Slack = _pigtail_face_out(L, pad) -
    face_out_min (one length model, one number with lead_access pigtail_xt30_mouth). Plus: the pose on the insertion
    path; the pose puts W at least out_of margin beyond the mouth; the hand box (both housings held: it spans a from
    W along the draw-out axis `axis`, t along axis x row, r along row) against every part present in the pose (COTS
    boxes always, printed shapes when rows is given; <= SWEEP_TOL) and wholly beyond the mouth (out_of); the dia 3 tail
    path from the anchor to W."""
    import manifold3d as m3
    n = _ins_index(L, mp['insertion'])
    ins, P, c = L.INSERTIONS[n], L.PIGTAIL, _pig_cable(L)
    disp = tuple(float(x) for x in mp['disp'])
    probs, info = [], []
    if not _on_path(ins['path'], disp):
        probs.append('mate pose %s not on the insertion path of %s' % (list(disp), ins['id']))
    fo = _pigtail_face_out(L)
    slack = fo['face_out_mm'] - P['face_out_min']
    via = list(c.get('via') or [])
    if mp.get('anchor') not in via:
        return dict(row, status='fail', error='anchor %s not in the %s via' % (mp.get('anchor'), c['id']))
    W = _plug_point(L, mp['W'])
    ptd = tuple(W[i] + disp[i] for i in range(3))
    # the length model drops vertically from the hole centre (SPEC-C3 3.2-1: drop = hole top to the mouth plane), so the
    #   tail starts on that line at the anchor box bottom, not at the generic clamp corner of the anchor box
    fh, ab = L.FLOOR_HOLES['pigtail'], box_bb(L.KEEPOUTS[mp['anchor']])
    apt = tuple(min(max(v, ab[2 * i]), ab[2 * i + 1]) for i, v in
                enumerate(((fh['x'][0] + fh['x'][1]) / 2, (fh['y'][0] + fh['y'][1]) / 2, ab[4])))
    pose_out = _out_of_mm((ptd[0], ptd[0], ptd[1], ptd[1], ptd[2], ptd[2]), mp['out_of'])
    row.update(pose=list(disp), reach='pigtail', model='_pigtail_face_out (= lead_access pigtail_xt30_mouth)',
               length_mm=fo['length_mm'], face_out_mm=_r(fo['face_out_mm'], 1), face_out_min=P['face_out_min'],
               slack_mm=_r(slack, 1), allowance_mm=_r(fo['allowance_mm'], 1), d_board_mm=_r(fo['d_board_mm'], 1),
               detour_mm=_r(fo['detour_mm'], 1), housing_credit_mm=fo['housing_credit_mm'], anchor=mp['anchor'],
               anchor_pt=[_r(x, 2) for x in apt], W_pose=[_r(x, 2) for x in ptd], tail_mm=_r(math.dist(apt, ptd), 1),
               pose_out_mm=_r(pose_out, 2))
    if slack < -1e-9:
        probs.append('pigtail XT30 comes only %.1f mm out of the mouth (< %.1f): L %.0f, d_board %.1f, detour %.1f'
                     % (fo['face_out_mm'], P['face_out_min'], fo['length_mm'], fo['d_board_mm'], fo['detour_mm']))
    if pose_out < -1e-9:
        probs.append('mate pose puts W %.2f mm short of %s' % (-pose_out, mp['out_of']))
    hb = _hand_box(ptd, tuple(-a for a in mp['axis']), mp.get('row', (1, 0, 0)), L.HAND_ENVELOPES[mp['hand']])
    # `hang` (part on its own lead, not rigid during the mate): the part is lowered along z until its top clears the
    #   hand box, stays a target there, and its lead must span from the end part's lead side to it with the margin
    hg = mp.get('hang')
    tg = _pose_targets(L, rows, n, disp, {mp['end']} | ({hg['part']} if hg else set()), cache)
    if hg:
        hbox = box_bb(L.COTS[hg['part']]['box'])
        extra = min(0.0, hb[4] - (hbox[5] + disp[2]))
        hd = (disp[0], disp[1], disp[2] + extra)
        hbb = (hbox[0] + hd[0], hbox[1] + hd[0], hbox[2] + hd[1], hbox[3] + hd[1], hbox[4] + hd[2], hbox[5] + hd[2])
        tg.append((hg['part'], _bb_cube(m3, hbb), hbb))
        eb = box_bb(L.COTS[mp['end']]['box'])
        lx = eb[1] if hg.get('lead_end') == '+x' else eb[0]       # r7 fix-up: the pack lead (male) end of the pair
        lp = (lx + disp[0], (eb[2] + eb[3]) / 2 + disp[1], (eb[4] + eb[5]) / 2 + disp[2])
        near = tuple(min(max(lp[i], hbb[2 * i]), hbb[2 * i + 1]) if i < 2 else hbb[5] for i in range(3))
        hl = next(c_['length'] for c_ in L.CABLES if c_['id'] == hg['cable'])
        need = math.dist(lp, near) + reach_margin(L, hl)
        row.update(hang=dict(part=hg['part'], cable=hg['cable'], lowered_mm=_r(-extra, 2), lead_mm=hl,
                             need_mm=_r(need, 1), slack_mm=_r(hl - need, 1)))
        if need > hl + 1e-9:
            probs.append('%s cannot hang below the hand on its %s: needs %.1f > %d mm' % (hg['part'], hg['cable'], need,
                                                                                         hl))
    hh = _hits_of(_bb_cube(m3, hb), hb, tg)
    oo = _out_of_mm(hb, mp['out_of'])
    tm = _tail_manifold(apt, ptd)
    th = [] if tm is None else _hits_of(tm, tuple(f(apt[i], ptd[i]) + s * TAIL_D / 2 for i in range(3)
                                                  for f, s in ((min, -1), (max, 1))), tg)
    row.update(hand=mp['hand'], hand_box=[_r(x, 2) for x in hb], hand_hits=hh, out_of=list(mp['out_of']),
               out_of_mm=_r(oo, 2), tail_hits=th, targets=len(tg), shapes=rows is not None)
    for nm, bad, msg in (('hand', hh, 'hand envelope hits %s' % ', '.join(h['obstacle'] for h in hh)),
                         ('out_of', oo < -1e-9, 'hand envelope %.2f mm short of %s' % (-oo, mp['out_of'])),
                         ('tail', th, 'tail path blocked by %s' % ', '.join(h['obstacle'] for h in th))):
        if bad:
            (info if nm in (mp.get('info') or ()) else probs).append(msg)
    if info:
        row.update(info_only=info, gate=mp.get('gate'))
    if probs:
        row['error'] = '; '.join(probs)
    return dict(row, problems=probs, status='fail' if probs else 'pass')


def _keeper_standin(L):
    """Fast stand-in for the pi_keeper solid near the port edge: the bar plus the port finger blocks (kf3/kf4)."""
    K, e = L.PI_KEEPER, L.PI['y'][1]
    out = [box_bb(K['bar'])]
    for f in K['fingers']:
        if f['edge'] == 'port':
            out.append((f['at'] - K['finger_w'] / 2, f['at'] + K['finger_w'] / 2, e - K['reach'],
                        e + K['gap_xy'] + K['finger_block'], L.PI['x1203_z'][1] + K['gap_z'], K['under_z'] + 0.45))
    return out


def _pigtail_store_exits(L, rows, pb, od):
    """r7 fix-up (VERIFY-C3): clear length beyond each x end of the stored XT30 pair box pb, within its (y, z) section,
    to the nearest solid present at step 10 (run_button and pack boxes; base_grip solid when rows is given, else the
    GRIP bay walls). Required: PIGTAIL bend flex_r_od x od + od (+ rigid exit >= 0, unknown: G-MP-PACK)."""
    P = L.PIGTAIL
    need = P['bend']['flex_r_od'] * od + od
    bay = box_bb(L.GRIP['bay'])
    res = {}
    for end, sgn in (('+x', 1), ('-x', -1)):
        x_end = pb[1] if sgn > 0 else pb[0]
        best, who = (bay[1] - x_end) if sgn > 0 else (x_end - bay[0]), 'bay wall'
        for cid in ('run_button', 'pack'):
            b = box_bb(L.COTS[cid]['box'])
            if b[2] < pb[3] and pb[2] < b[3] and b[4] < pb[5] and pb[4] < b[5]:
                d = (b[0] - x_end) if sgn > 0 else (x_end - b[1])
                if -1e-9 <= d < best:
                    best, who = d, cid
        sh = (rows or {}).get('base_grip', {}).get('shape') if rows else None
        if sh is not None:
            lo = [x_end if sgn > 0 else x_end - 30.0, pb[2], pb[4]]
            hi = [x_end + 30.0 if sgn > 0 else x_end, pb[3], pb[5]]
            try:
                c = sh.intersect(cq.Solid.makeBox(hi[0] - lo[0], hi[1] - lo[1], hi[2] - lo[2], V(*lo)))
                if c.Volume() > 0.05:
                    bb = c.BoundingBox()
                    d = (bb.xmin - x_end) if sgn > 0 else (x_end - bb.xmax)
                    if d < best:
                        best, who = max(0.0, d), 'base_grip'
            except Exception:  # noqa: BLE001
                pass
        res[end] = dict(clear_mm=_r(best, 2), nearest=who, need_min_mm=_r(need, 2))
    bad = ['%s end %.1f mm to %s < %.1f' % (e, v['clear_mm'], v['nearest'], need) for e, v in res.items()
           if v['clear_mm'] < need - 1e-9]
    allow = min(v['clear_mm'] - v['need_min_mm'] for v in res.values())
    return dict(ends=res, rigid_exit='unknown (G-MP-PACK), lower bound 0', rigid_allow_mm=_r(allow, 2),
                gate='G-MP-PACK: the rigid solder-cup / heat-shrink length beyond each XT30 housing must be <= '
                     'rigid_allow_mm (measure; else re-pose)', status='fail' if bad else 'pass',
                **({'error': '; '.join(bad)} if bad else {}))


def _pigtail_drop_v(L, l_cut):
    """r7 fix-up (VERIFY-C3): WIRING s4 drop estimate (the G-W5 model) at L_cut: 2 conductors x (L_cut + pack lead) of
    18 AWG + fuse cold + XT30 pair, at the peak current."""
    D = L.PIGTAIL['drop']
    lead = next(c['length'] for c in L.CABLES if c['id'] == 'pack_lead')
    r_mohm = D['mohm_per_m'] * 2 * (l_cut + lead) / 1000.0 + L.PIGTAIL_FUSE['cold_mohm'] + D['xt30_mohm']
    return D['i_peak_a'] * r_mohm / 1000.0


def _pigtail_drop_limit(L):
    """Largest d_board (0.5 mm steps) whose rounded L_cut keeps the drop estimate <= the limit."""
    P = L.PIGTAIL
    d, best = 0.0, None
    while d <= 400.0:
        cut = math.ceil((P['base_len'] + d) / P['cut_round'] - 1e-9) * P['cut_round']
        if _pigtail_drop_v(L, cut) <= P['drop']['limit_v'] + 1e-12:
            best = d
        else:
            break
        d += 0.5
    return dict(d_board_max_mm=best if best is not None else -1.0)


def _pigtail_drop_row(L, smp, dl):
    """pigtail_drop: the assumed pad (PIGTAIL['pad'], Q2) must meet the G-W5 drop estimate, and STEPS[1] must carry
    the stop branch at the computed d_board limit (pads farther from W are never cut to length)."""
    P = L.PIGTAIL
    D = P['drop']
    d0 = _pigtail_face_out(L)['d_board_mm']
    cut0 = math.ceil((P['base_len'] + d0) / P['cut_round'] - 1e-9) * P['cut_round']
    v0 = _pigtail_drop_v(L, cut0)
    lim = dl['d_board_max_mm']
    st1 = next((s for s in L.STEPS if s['step'] == 1), {}).get('action', '')
    need = 'more than %d mm, stop: do not cut' % int(math.floor(lim + 1e-9))
    rows_ = [dict(pad=s['pad'], d_board_mm=s['d_board_mm'], l_cut_mm=s['l_cut_mm'],
                  drop_v=_r(_pigtail_drop_v(L, s['l_cut_mm']), 3),
                  verdict='ok' if s['d_board_mm'] <= lim + 1e-9 else 'stop at step 1 (G-W2)') for s in smp]
    pr = []
    if lim < 0:
        pr.append('no pad position meets the %.2f V limit' % D['limit_v'])
    if v0 > D['limit_v'] + 1e-12:
        pr.append('assumed pad: drop %.3f V > %.2f V at L_cut %.0f' % (v0, D['limit_v'], cut0))
    if need.lower() not in ' '.join(st1.split()).lower():
        pr.append('STEPS[1] lacks the stop branch "%s"' % need)
    return dict(id='pigtail_drop', kind='drop', cable='pigtail', model=D['src'], i_peak_a=D['i_peak_a'],
                limit_v=D['limit_v'], assumed_pad_l_cut_mm=cut0, assumed_pad_drop_v=_r(v0, 3),
                d_board_max_mm=lim, l_cut_max_ok_mm=math.ceil((P['base_len'] + lim) / P['cut_round'] - 1e-9)
                * P['cut_round'], samples=rows_, gate=D['gate'], estimate=True,
                status='fail' if pr else 'pass', **({'error': '; '.join(pr)} if pr else {}))


def check_lead_access(L, rows=None):
    """r7 C3 (SPEC-C3 3.2, BX-3/BX-11/BX-16): pigtail_xt30_mouth (face_out with the allowance, required_len),
    pigtail_range (cut rule over the credible pad range), pigtail_store (fold above the pack: fill with the shared
    leads, U-turn, pack/cap, side gaps info), lane_<cable>_<box> + lane_separation (taped lanes under the stack),
    run_lead_window (threading window along base_on) and pigtail_wrap_clear (keeper vs the lanes grown by form_tol, at
    the final pose and along keeper_in; the keeper solid when rows is given, else the bar + port finger stand-in)."""
    P, K = L.PIGTAIL, L.KEEPOUTS
    fmin = P['face_out_min']
    cab = {c['id']: c for c in L.CABLES}
    pig = cab['pigtail']
    out = []
    # 1. mouth
    fo = _pigtail_face_out(L)
    req = _pigtail_required_len(L)
    r = dict(id='pigtail_xt30_mouth', kind='reach', cable='pigtail', pad=dict(P['pad']), tie=dict(P['tie']),
             face_out_min=fmin, required_len_mm=req, estimate=True, **{k: _r(v, 1) for k, v in fo.items()})
    r['status'] = 'pass' if fo['face_out_mm'] >= fmin - 1e-9 else 'fail'
    if r['status'] == 'fail':
        r['error'] = 'XT30 face out %.1f < %.1f mm (L %.0f; required %s)' % (fo['face_out_mm'], fmin, fo['length_mm'],
                                                                           req)
    out.append(r)
    # 2. pad range with the cut rule
    smp = []
    for name, pad in _pigtail_pad_samples(L):
        d = _pigtail_face_out(L, pad)['d_board_mm']
        raw = P['base_len'] + d
        cut = math.ceil(raw / P['cut_round'] - 1e-9) * P['cut_round']
        smp.append(dict(pad=name, d_board_mm=_r(d, 1), l_raw=raw, l_cut_mm=cut,
                        face_out_raw_mm=_r(_pigtail_face_out(L, pad, raw)['face_out_mm'], 2),
                        face_out_cut_mm=_r(_pigtail_face_out(L, pad, cut)['face_out_mm'], 2)))
    worst = min(smp, key=lambda s: s['face_out_raw_mm'])
    lmax = max(s['l_cut_mm'] for s in smp)
    r = dict(id='pigtail_range', kind='reach', cable='pigtail', base_len=P['base_len'], samples=len(smp),
             worst_pad=worst['pad'], worst_face_out_mm=_r(worst['face_out_raw_mm'], 1),
             worst_face_out_cut_mm=_r(worst['face_out_cut_mm'], 1), l_cut_max_mm=lmax, stock_mm=P['stock_len'],
             rows=[{k: v for k, v in s.items() if k != 'l_raw'} for s in smp], face_out_min=fmin, estimate=True)
    pr = []
    if worst['face_out_raw_mm'] < fmin - 1e-9:
        pr.append('cut rule leaves %.1f mm out at %s (< %.1f)' % (worst['face_out_raw_mm'], worst['pad'], fmin))
    if lmax > P['stock_len'] + 1e-9:
        pr.append('L_cut %.0f > stock %.0f mm' % (lmax, P['stock_len']))
    # r7 fix-up (VERIFY-C3): the cut rule's reach holds over the whole pad range, but G-W5 does not; the samples
    #   past the drop limit are named here with the gate, and pigtail_drop (below) enforces the step-1 stop branch
    dl = _pigtail_drop_limit(L)
    r['drop_limited'] = [s['pad'] for s in smp if s['d_board_mm'] > dl['d_board_max_mm'] + 1e-9]
    if r['drop_limited']:
        r['gate'] = 'G-W2 / G-W5: pads past d_board %.1f mm stop at step 1 (pigtail_drop)' % dl['d_board_max_mm']
    out.append(dict(r, status='fail' if pr else 'pass', **({'error': '; '.join(pr)} if pr else {})))
    out.append(_pigtail_drop_row(L, smp, dl))
    # 3. store above the pack
    S = P['store']
    path_in, pts = _pigtail_path(L)
    zb, pb = box_bb(K[S['zone']]), box_bb(L.COTS['xt30_pair']['box'])
    fx = pb[0] if S.get('female_end') == '-x' else pb[1]          # r7 fix-up: the pigtail enters the female end
    d_fin = math.dist(pts[-1], (fx, (pb[2] + pb[3]) / 2, (pb[4] + pb[5]) / 2))
    stored = [s['l_cut_mm'] - s['l_raw'] + P['base_len'] - path_in - d_fin for s in smp]
    bound = P['base_len'] + P['cut_round'] - path_in - d_fin      # the 5 mm rounding bounds every pad (stricter)
    od, cores = P['od_range'][1], int(pig.get('cores', 2))
    shared = sum(cab[s]['length'] for s in S.get('shared') or () if s in cab)
    vz = _box_vol(zb, zb) - _box_vol(zb, pb)
    fill = (max(stored + [bound]) + shared) * cores * math.pi / 4 * od ** 2 / vz
    width = zb[3] - zb[2]
    uneed = 2 * S['bend_r_od'] * od + 2 * cores * od
    bay, pk, cap = box_bb(L.GRIP['bay']), box_bb(L.COTS['pack']['box']), box_bb(L.CAP['box'])
    inside = all(bay[2 * i] - 1e-9 <= zb[2 * i] and zb[2 * i + 1] <= bay[2 * i + 1] + 1e-9 for i in range(3))
    gaps = dict(y0=_r(pk[2] - bay[2], 2), y1=_r(bay[3] - pk[3], 2), x0=_r(pk[0] - bay[0], 2), x1=_r(bay[1] - pk[1], 2))
    pr = []
    if fill > S['fill_max'] + 1e-9:
        pr.append('store fill %.3f > %.2f' % (fill, S['fill_max']))
    if uneed > width + 1e-9:
        pr.append('U-turn needs %.1f > %.1f mm' % (uneed, width))
    if not inside:
        pr.append('%s not inside GRIP bay' % S['zone'])
    if pk[5] > zb[4] + 1e-9:
        pr.append('pack top %.1f above %s z0 %.1f' % (pk[5], S['zone'], zb[4]))
    if _box_vol(cap, zb) > 1e-9:
        pr.append('cap overlaps %s' % S['zone'])
    out.append(dict(id='pigtail_store', kind='store', cable='pigtail', zone=S['zone'], d_fin_mm=_r(d_fin, 1),
                    stored_mm=[_r(min(stored), 1), _r(max(stored), 1)], stored_bound_mm=_r(bound, 1),
                    shared=list(S.get('shared') or ()), shared_mm=shared, od_max=od, cores=cores,
                    zone_free_mm3=_r(vz, 0), fill=_r(fill, 3), fill_max=S['fill_max'], u_turn_need_mm=_r(uneed, 2),
                    u_turn_width_mm=_r(width, 2), u_turn_margin_mm=_r(width - uneed, 2),
                    free_section_mm=[_r(zb[1] - zb[0], 1), _r(width, 1), _r(pb[4] - zb[4], 1)],
                    pack_top=pk[5], zone_z0=zb[4], side_gaps_info=gaps,
                    loop_can_enter=sorted(k for k, v in gaps.items() if v >= od), estimate=True,
                    status='fail' if pr else 'pass', **({'error': '; '.join(pr)} if pr else {})))
    # r7 fix-up (VERIFY-C3): exits of the stored junction. Along the pair axis (x), the clear length beyond each end
    #   within the pair cross-section must hold the flexed exit bend (flex_r_od x od + od) plus the rigid solder-cup /
    #   heat-shrink length (unknown: lower bound 0, gate G-MP-PACK). Until the junction is re-posed this is OPEN: the
    #   row is marked with the gate (status 'info', never a plain pass); a fill / U-turn failure above still fails.
    ex = _pigtail_store_exits(L, rows, pb, od)
    srow = out[-1]
    srow['exits'] = ex
    if srow['status'] == 'pass' and ex['status'] != 'pass':
        srow.update(status='info', gate='G-MP-PACK (junction exits; re-pose open, VERIFY-C3)',
                    open='junction exits blocked: %s' % ex['error'])
    # 4. lanes + separation
    hmax = L.PI['x1203_z'][0] - L.FLOOR_Z[1]
    tol = P['form_tol']
    lanes = [(c, k) for c in L.CABLES for k in c.get('lanes') or []]
    for c, k in lanes:
        if k not in K:
            out.append(dict(id='lane_%s_%s' % (c['id'], k), kind='lane', status='fail', error='%s not in KEEPOUTS' % k))
            continue
        b = box_bb(K[k])
        w, h = min(b[1] - b[0], b[3] - b[2]), b[5] - b[4]
        nw, nh = int(c.get('cores', 1)) * c['od'], c['od'] + 0.5
        pr = [m for bad, m in ((w < nw - 1e-9, 'width %.2f < %.2f' % (w, nw)),
                               (h < nh - 1e-9, 'height %.2f < %.2f' % (h, nh)),
                               (h > hmax + 1e-9, 'height %.2f > %.2f under the X1203' % (h, hmax))) if bad]
        out.append(dict(id='lane_%s_%s' % (c['id'], k), kind='lane', cable=c['id'], box=k, width_mm=_r(w, 2),
                        need_width_mm=_r(nw, 2), height_mm=_r(h, 2), need_height_mm=_r(nh, 2), max_height_mm=_r(hmax, 2),
                        status='fail' if pr else 'pass', **({'error': '; '.join(pr)} if pr else {})))
    sep, near = [], None
    for c, k in lanes:
        if k not in K:
            continue
        for c2 in L.CABLES:
            if c2['id'] == c['id'] or min(c2['steps']) > max(c['steps']):
                continue
            for k2 in sorted(set(c2.get('via') or []) | set(c2.get('lanes') or [])):
                if k2 not in K:
                    continue
                g = _box_gap(box_bb(K[k]), box_bb(K[k2]))
                if near is None or g < near[0]:
                    near = (g, k, k2)
                if g < tol - 1e-9:
                    sep.append('%s (%s) to %s (%s): %.2f < %.1f' % (k, c['id'], k2, c2['id'], g, tol))
    out.append(dict(id='lane_separation', kind='lane', min_gap_mm=None if near is None else _r(near[0], 2),
                    nearest=None if near is None else [near[1], near[2]], form_tol=tol, problems=sep,
                    status='fail' if sep else 'pass', **({'error': '; '.join(sep)} if sep else {})))
    # 5. run-lead threading window along base_on
    run = cab['run_lead']
    bo = next((i for i in L.INSERTIONS if i['id'] == 'base_on'), None)
    rp, fh = L.base_run_passage(), L.FLOOR_HOLES['run_lead']
    ox, oy, at = None, None, None
    for a, b in zip(bo['path'], bo['path'][1:]) if bo else ():
        if abs(a[2]) > 1e-9 or abs(b[2]) > 1e-9:
            continue
        m = max(1, int(math.ceil(math.dist(a, b) / LEAD_WINDOW_STEP)))
        for j in range(m + 1):
            p = [a[i] + (b[i] - a[i]) * j / m for i in range(3)]
            x_ = min(rp['x'][1] + p[0], fh['x'][1]) - max(rp['x'][0] + p[0], fh['x'][0])
            y_ = min(rp['y'][1] + p[1], fh['y'][1]) - max(rp['y'][0] + p[1], fh['y'][0])
            if ox is None or x_ < ox:
                ox, at = x_, [_r(v, 2) for v in p]
            oy = y_ if oy is None else min(oy, y_)
    ny = int(run.get('cores', 1)) * run.get('od', 0.0)
    pr = []
    if ox is None:
        pr.append('base_on has no z-0 segment')
    else:
        if ox < L.RUN_WINDOW_MIN - 1e-9:
            pr.append('x overlap %.2f < RUN_WINDOW_MIN %.1f at base offset %s' % (ox, L.RUN_WINDOW_MIN, at))
        if oy < ny - 1e-9:
            pr.append('y overlap %.2f < %.2f' % (oy, ny))
    out.append(dict(id='run_lead_window', kind='thread', cable='run_lead', passage=rp, hole=dict(fh),
                    min_x_overlap_mm=None if ox is None else _r(ox, 2), at_offset=at, window_min=L.RUN_WINDOW_MIN,
                    min_y_overlap_mm=None if oy is None else _r(oy, 2), need_y_mm=_r(ny, 2),
                    status='fail' if pr else 'pass', **({'error': '; '.join(pr)} if pr else {})))
    # 6. keeper vs the pigtail lanes grown by form_tol in x
    ki = next((i for i in L.INSERTIONS if 'pi_keeper' in i['moving']), None)
    poses = [(0.0, 0.0, 0.0)] + (list(_path_points(ki['path'], LEAD_WINDOW_STEP)) if ki else [])
    grown = []
    for k in ['ko_pig_wrap'] + [x for x in pig.get('lanes') or [] if x != 'ko_pig_wrap']:
        b = box_bb(K[k])
        grown.append((k, (b[0] - tol, b[1] + tol) + tuple(b[2:])))
    shp = (rows or {}).get('pi_keeper', {}).get('shape') if rows else None
    worst = (0.0, None, None)
    if shp is not None:
        import manifold3d as m3
        km, kb = manifold_of(shp), bb_tuple(shp)
        for k, g in grown:
            gm = _bb_cube(m3, g)
            for p in poses:
                if not bb_overlap((kb[0] + p[0], kb[1] + p[0], kb[2] + p[1], kb[3] + p[1], kb[4] + p[2], kb[5] + p[2]),
                                  g, -1e-6):
                    continue
                v = (gm ^ km.translate(list(p))).volume()
                if v > worst[0]:
                    worst = (v, k, p)
    else:
        for k, g in grown:
            for p in poses:
                v = sum(_box_vol(g, (s[0] + p[0], s[1] + p[0], s[2] + p[1], s[3] + p[1], s[4] + p[2], s[5] + p[2]))
                        for s in _keeper_standin(L))
                if v > worst[0]:
                    worst = (v, k, p)
    st = 'pass' if worst[0] <= LEAD_CLEAR_TOL + 1e-12 else 'fail'
    out.append(dict(id='pigtail_wrap_clear', kind='clear', boxes=[k for k, _g in grown], grown_x_mm=tol,
                    keeper='solid' if shp is not None else 'stand-in (bar + kf3/kf4)', poses=len(poses),
                    max_volume_mm3=_r(worst[0], 3), worst_box=worst[1],
                    at_offset=None if worst[2] is None else [_r(x, 2) for x in worst[2]], tol_mm3=LEAD_CLEAR_TOL,
                    status=st, **({'error': 'keeper in the grown %s: %.3f mm3 > %.2f' % (worst[1], worst[0],
                                                                                        LEAD_CLEAR_TOL)}
                                  if st == 'fail' else {})))
    return out


def check_cable_stow(L):
    """r7 C2 (SPEC-C2 3.2-4): spare = length_max + pigtail - final-pose route estimate (no allowance deducted). Per stow
    box: sum(spare x pi/4 od^2 + junction) <= STOW_FILL x volume; joined to a route box of every naming cable
    (passage >= ROUTE_PASSAGE); no overlap with a COTS box present at the last step; >= STOW_BLOWER_MIN from the blower
    footprint in plan. Routed cables without a stow get an info row with their spare."""
    last = max(s['step'] for s in L.STEPS)
    est = {r['cable']: r.get('est_route_mm') for r in check_cable_routes(L) if r.get('est_route_mm') is not None}
    out, by_box = [], {}
    for c in L.CABLES:
        if not c.get('via') or c['id'] not in est:
            continue
        lmax = (c.get('length_range') or (None, c['length']))[1]
        spare = lmax + float(c.get('pigtail') or 0.0) - est[c['id']]
        if c.get('stow'):
            by_box.setdefault(c['stow'], []).append((c, spare))
        else:
            out.append(dict(kind='spare', cable=c['id'], spare_mm=_r(spare, 1), status='info',
                            home=STOW_INFO_HOME.get(c['id'], 'no named home (follow-up: give it a stow box)')))
    bl = box_bb(L.COTS['cooler']['features']['blower'])
    for k, cs in sorted(by_box.items()):
        probs = []
        if k not in L.KEEPOUTS:
            out.append(dict(kind='stow', stow=k, status='fail', error='stow box not in KEEPOUTS'))
            continue
        sb = box_bb(L.KEEPOUTS[k])
        vol = (sb[1] - sb[0]) * (sb[3] - sb[2]) * (sb[5] - sb[4])
        per = []
        for c, spare in cs:
            sec = math.pi / 4 * float(c['od']) ** 2
            per.append(dict(cable=c['id'], spare_mm=_r(spare, 1), od=c['od'], section_mm2=_r(sec, 2),
                            junction_mm3=c.get('junction_mm3', 0.0), demand_mm3=_r(spare * sec + c.get('junction_mm3', 0.0), 1)))
            joined = False
            for v in c['via']:
                b = box_bb(L.KEEPOUTS[v])
                ov = [min(sb[2 * i + 1], b[2 * i + 1]) - max(sb[2 * i], b[2 * i]) for i in range(3)]
                if min(ov) >= -1e-6 and sorted(ov)[1] >= ROUTE_PASSAGE - 1e-6:
                    joined = True
                    per[-1].setdefault('joined_to', v)
            if not joined:
                probs.append('%s not joined to a route box of %s' % (k, c['id']))
        demand = sum(p_['demand_mm3'] for p_ in per)
        cap = STOW_FILL * vol
        if demand > cap + 1e-6:
            probs.append('demand %.0f mm3 > capacity %.0f mm3 (%.2f x %.0f)' % (demand, cap, STOW_FILL, vol))
        cots_hits = [i for i in L.present_at(last) if (L.COTS.get(i) or {}).get('box') is not None
                     and _box_vol(sb, box_bb(L.COTS[i]['box'])) > 1e-6]
        if cots_hits:
            probs.append('overlaps COTS %s' % ', '.join(cots_hits))
        bd = math.hypot(max(bl[0] - sb[1], 0.0, sb[0] - bl[1]), max(bl[2] - sb[3], 0.0, sb[2] - bl[3]))
        if bd < STOW_BLOWER_MIN - 1e-9:
            probs.append('%.1f mm from the blower footprint in plan (< %.1f)' % (bd, STOW_BLOWER_MIN))
        out.append(dict(kind='stow', stow=k, cables=per, demand_mm3=_r(demand, 0), capacity_mm3=_r(cap, 0),
                        volume_mm3=_r(vol, 0), fill=STOW_FILL, cots_overlap=cots_hits, blower_mm=_r(bd, 1),
                        problems=probs, estimate=True, status='fail' if probs else 'pass',
                        **({'error': '; '.join(probs)} if probs else {})))
    return out


def header_pin_xy(L, n):
    """r7 C2: header pin n (1..40) centre (x, y): pin 1 at the gpio +X end - 1.27, odd row = PI['header_rows_y'][1]."""
    g = L.COTS['pi5']['features']['gpio']
    return (g['x'][1] - 1.27 - L.HDR_HOUSING['pitch'] * ((n - 1) // 2), L.PI['header_rows_y'][n % 2])


def header_housing_boxes(L, sec=None):
    """r7 C2: one box per HEADER_HOUSINGS entry (section `sec`, default the class maximum; length the class maximum)."""
    h = L.HDR_HOUSING
    s = max(h['sec']) if sec is None else sec
    z0 = h['seat_z']
    out = []
    for cab, typ, pins in L.HEADER_HOUSINGS:
        xy = [header_pin_xy(L, p) for p in pins]
        out.append(((cab, typ, tuple(pins)), (min(p[0] for p in xy) - s / 2, max(p[0] for p in xy) + s / 2,
                                              min(p[1] for p in xy) - s / 2, max(p[1] for p in xy) + s / 2,
                                              z0, z0 + max(h['length']))))
    return out


def check_header_housings(L, rows=None):
    """r7 C2 (SPEC-C2 3.2-5): (a) type '1', or '1x2' on 2 used adjacent pins; (b) gap >= min_gap to every COTS box
    present at the last step except pi5; (c) shape distance >= min_gap to every printed part present then (rows);
    (d) the part above the pi5 box top inside the cable's header-end route box; (e) no mutual overlap (class minimum
    section)."""
    h = L.HDR_HOUSING
    last = max(s['step'] for s in L.STEPS)
    pres = L.present_at(last)
    pitch, mg = h['pitch'], h['min_gap']
    pi_top = box_bb(L.COTS['pi5']['box'])[5]
    gb = box_bb(L.COTS['pi5']['features']['gpio'])
    boxes = header_housing_boxes(L)
    small = dict(header_housing_boxes(L, sec=min(h['sec'])))
    cab = {c['id']: c for c in L.CABLES}
    out = []
    for (cn, typ, pins), b in boxes:
        probs = []
        used = set((getattr(L, 'HDR_USED_PINS', {}) or {}).get(cn, ()))
        unused = [p for p in pins if p not in used]
        if unused:
            probs.append('covers unused pin(s) %s' % unused)
        if typ == '1':
            if len(pins) != 1:
                probs.append("type '1' with %d pins" % len(pins))
        elif typ == '1x2':
            ok = len(pins) == 2 and ((pins[0] % 2 == pins[1] % 2 and abs(pins[0] - pins[1]) == 2)
                                     or (min(pins) % 2 == 1 and abs(pins[0] - pins[1]) == 1))
            if not ok:
                probs.append("type '1x2' on non-adjacent pins %s" % (pins,))
        else:
            probs.append('illegal housing type %r (only 1 or 1x2)' % typ)
        cg = sorted(((_box_gap(_ko(L.COTS[i]['box']), list(b)), i) for i in pres if i != 'pi5'
                     and (L.COTS.get(i) or {}).get('box') is not None))
        cmin = cg[0] if cg else (None, None)
        if cmin[0] is not None and cmin[0] < mg - 1e-9:
            probs.append('gap %.2f to COTS %s < %.1f' % (cmin[0], cmin[1], mg))
        pg = []
        if rows is not None:
            hs = dc.box_solid(dict(x=(b[0], b[1]), y=(b[2], b[3]), z=(b[4], b[5])))
            for i in pres:
                if i not in getattr(L, 'PARTS', {}) or (rows.get(i) or {}).get('shape') is None:
                    continue
                if _box_gap(list(bb_tuple(rows[i]['shape'])), list(b)) > 3.0:
                    continue
                d = rows[i]['shape'].distance(hs)
                pg.append((d, i))
                if d < mg - 1e-9:
                    probs.append('distance %.2f to %s < %.1f' % (d, i, mg))
        pg.sort()
        c = cab.get(cn) or {}
        via = list(c.get('via') or [])
        hdr_box = min((v for v in via[:1] + via[-1:]), key=lambda v: _box_gap(_ko(L.KEEPOUTS[v]), list(gb))) \
            if via else None
        above = None
        if b[5] > pi_top + 1e-9:
            if hdr_box is None:
                probs.append('no route box for the part above the pi5 box')
            else:
                kb = box_bb(L.KEEPOUTS[hdr_box])
                ub = (b[0], b[1], b[2], b[3], max(b[4], pi_top), b[5])
                above = max(max(kb[2 * i] - ub[2 * i], ub[2 * i + 1] - kb[2 * i + 1], 0.0) for i in range(3))
                if above > 1e-6:
                    probs.append('top %.2f mm outside %s' % (above, hdr_box))
        sb = small[(cn, typ, tuple(pins))]
        ov = [k for k, o in small.items() if k != (cn, typ, tuple(pins)) and _box_vol(sb, o) > 1e-9]
        if ov:
            probs.append('overlaps housing(s) %s' % ['%s %s' % (k[0], k[2]) for k in ov])
        out.append(dict(cable=cn, type=typ, pins=list(pins), box=[_r(x, 2) for x in b],
                        cots_gap_mm=None if cmin[0] is None else _r(cmin[0], 2), cots_nearest=cmin[1],
                        printed_gap_mm=_r(pg[0][0], 2) if pg else None, printed_nearest=pg[0][1] if pg else None,
                        route_box=hdr_box, top_outside_mm=None if above is None else _r(above, 2),
                        problems=probs, estimate=True, status='fail' if probs else 'pass',
                        **({'error': '; '.join(probs)} if probs else {})))
    # r7 fix-up (VERIFY-C2 minor) rule (f): every used header pin of every cable has exactly one housing
    have = {}
    for cn, _t, pins in getattr(L, 'HEADER_HOUSINGS', []):
        for p in pins:
            have.setdefault(cn, []).append(p)
    for cn, used in sorted((getattr(L, 'HDR_USED_PINS', {}) or {}).items()):
        got = have.get(cn, [])
        miss = sorted(set(used) - set(got))
        dup = sorted({p for p in got if got.count(p) > 1})
        pr = (['used pin(s) %s without a housing' % miss] if miss else []) + (
            ['pin(s) %s in more than one housing' % dup] if dup else [])
        out.append(dict(cable=cn, kind='completeness', used=list(used), housed=sorted(got), status='fail' if pr else
                        'pass', **({'error': '; '.join(pr)} if pr else {})))
    return out


# ------------------------------------------------------------------------------------------- 4. bed fit
def check_bed(L, pid, shape_print):
    bb = shape_print.BoundingBox()
    dims = (bb.xlen, bb.ylen, bb.zlen)
    res = {}
    ok_all = True
    for bed, (BX, BY, BZ) in L.PRINT_BEDS.items():
        ok = dims[2] <= BZ and ((dims[0] <= BX and dims[1] <= BY) or (dims[0] <= BY and dims[1] <= BX))
        res[bed] = ok
        ok_all &= ok
    return dict(part=pid, print_bbox=[_r(x, 2) for x in dims], beds=res, status='pass' if ok_all else 'fail')


# ------------------------------------------------------------------------------------------- meshes
def mesh_of(shape, tol=MESH_TOL, ang=MESH_ANG):
    """(V float64 (n,3), F int (m,3)) with duplicate vertices merged (1e-5 grid)."""
    vs, ts = shape.tessellate(tol, ang)
    Vx = np.array([(v.x, v.y, v.z) for v in vs], dtype=np.float64).reshape(-1, 3)
    F = np.array(ts, dtype=np.int64).reshape(-1, 3)
    if len(Vx) == 0:
        return Vx, F
    key = np.round(Vx / 1e-5).astype(np.int64)
    _, idx, inv = np.unique(key, axis=0, return_index=True, return_inverse=True)
    Vm = Vx[idx]
    Fm = inv.reshape(-1)[F]
    keep = (Fm[:, 0] != Fm[:, 1]) & (Fm[:, 1] != Fm[:, 2]) & (Fm[:, 0] != Fm[:, 2])
    return Vm, Fm[keep]


def manifold_of(shape):
    return manifold_of_tol(shape, MESH_TOL, MESH_ANG)


def manifold_of_tol(shape, tol, ang):
    import manifold3d as m3
    Vm, Fm = mesh_of(shape, tol, ang)
    if len(Fm) == 0:
        return None
    mesh = m3.Mesh(vert_properties=np.ascontiguousarray(Vm, np.float32), tri_verts=np.ascontiguousarray(Fm, np.uint32))
    man = m3.Manifold(mesh)
    if man.is_empty():
        mesh.merge()
        man = m3.Manifold(mesh)
    return None if man.is_empty() else man


# ------------------------------------------------------------------------------------------- 5. thin-wall screen
def _ray_hits(Vm, Fm, O, D, chunk=None, max_len=6.0):
    """Nearest positive hit distance along D (unit) for rays O, up to max_len (Moller-Trumbore, numpy). Rays are
    processed in spatial chunks against only the triangles near them. No hit within max_len -> inf."""
    v0, v1, v2 = Vm[Fm[:, 0]], Vm[Fm[:, 1]], Vm[Fm[:, 2]]
    e1, e2 = v1 - v0, v2 - v0
    tmin = np.minimum(np.minimum(v0, v1), v2)
    tmax = np.maximum(np.maximum(v0, v1), v2)
    out = np.full(len(O), np.inf)
    order = np.lexsort(np.floor(O / 6.0).T[::-1])
    chunk = chunk or 64
    for s in range(0, len(O), chunk):
        idx = order[s:s + chunk]
        lo = O[idx].min(axis=0) - max_len
        hi = O[idx].max(axis=0) + max_len
        sel = np.nonzero(np.all(tmax >= lo, axis=1) & np.all(tmin <= hi, axis=1))[0]
        if len(sel) == 0:
            continue
        for s2 in range(0, len(sel), 40000):
            tri = sel[s2:s2 + 40000]
            o, d = O[idx][:, None, :], D[idx][:, None, :]
            E1, E2, P0 = e1[tri][None], e2[tri][None], v0[tri][None]
            p = np.cross(d, E2)
            det = np.einsum('ijk,ijk->ij', p, np.broadcast_to(E1, p.shape))
            ok = np.abs(det) > 1e-12
            inv = np.where(ok, 1.0 / np.where(ok, det, 1.0), 0.0)
            tv = o - P0
            u = np.einsum('ijk,ijk->ij', tv, p) * inv
            q = np.cross(tv, np.broadcast_to(E1, tv.shape))
            v = np.einsum('ijk,ijk->ij', np.broadcast_to(d, q.shape), q) * inv
            t = np.einsum('ijk,ijk->ij', np.broadcast_to(E2, q.shape), q) * inv
            hit = ok & (u >= -1e-9) & (v >= -1e-9) & (u + v <= 1 + 1e-9) & (t > 1e-4) & (t <= max_len)
            t = np.where(hit, t, np.inf).min(axis=1)
            out[idx] = np.minimum(out[idx], t)
    return out


def thin_wall(L, pid, shape, n=1500, loaded_boxes=(), seed=7):
    """Ray-thickness screen: sample points on the surface (area-weighted), shoot inward along -normal, thickness =
    first exit. Pass: area share under MIN_WALL <= 2 % and under MIN_FEATURE <= 0.5 %, and in loaded zones (bosses,
    posts, pads, hooks) the share under MIN_WALL_LOADED <= 2 %."""
    Vm, Fm = mesh_of(shape, tol=0.08, ang=0.3)
    if len(Fm) == 0:
        return dict(part=pid, status='fail', error='empty mesh')
    a, b, c = Vm[Fm[:, 0]], Vm[Fm[:, 1]], Vm[Fm[:, 2]]
    cr = np.cross(b - a, c - a)
    area = np.linalg.norm(cr, axis=1) / 2
    good = area > 1e-9
    nrm = np.zeros_like(cr)
    nrm[good] = cr[good] / (2 * area[good, None])
    if np.einsum('ij,ij->i', a, cr).sum() < 0:   # orientation: outward normals give positive signed volume
        nrm = -nrm
    rng = np.random.default_rng(seed)
    pick = rng.choice(len(Fm), size=n, p=area / area.sum())
    r1, r2 = rng.random(n), rng.random(n)
    flip = r1 + r2 > 1
    r1[flip], r2[flip] = 1 - r1[flip], 1 - r2[flip]
    P = a[pick] + r1[:, None] * (b[pick] - a[pick]) + r2[:, None] * (c[pick] - a[pick])
    N = nrm[pick]
    th_n = _ray_hits(Vm, Fm, P - N * 1e-3, -N)
    # wall thickness = max over a 30 deg cone of inward rays of (hit distance x cos tilt): a plate of thickness t gives
    # t for every ray, while ridges, knurl teeth and knife edges give the depth of the body behind them (so they are
    # not read as thin walls). th_n (the plain normal ray) is kept for the report.
    ref = np.where(np.abs(N[:, 0:1]) < 0.9, np.array([[1.0, 0, 0]]), np.array([[0, 1.0, 0]]))
    U = np.cross(N, ref)
    U /= np.linalg.norm(U, axis=1)[:, None]
    W = np.cross(N, U)
    th = np.where(np.isfinite(th_n), th_n, 6.0)      # nothing within 6 mm: at least 6 thick
    ct, st = math.cos(math.radians(30.0)), math.sin(math.radians(30.0))
    for k in range(6):
        ph = math.radians(60.0 * k)
        Dk = -N * ct + (U * math.cos(ph) + W * math.sin(ph)) * st
        dk = _ray_hits(Vm, Fm, P - N * 1e-3, Dk)
        th = np.maximum(th, np.where(np.isfinite(dk), dk, 6.0) * ct)
    fin = np.isfinite(th)
    th_f = th[fin]
    P_f = P[fin]
    mw, mf, ml = L.FDM['MIN_WALL'], L.FDM['MIN_FEATURE'], L.FDM['MIN_WALL_LOADED']
    declared = getattr(L, 'THIN_OK', {}).get(pid)          # layout-accepted exception: dict(min=, reason=)
    if declared:      # dict(min=wall threshold, loaded_min=optional loaded-zone threshold, reason=str)
        mw = max(mf, float(declared.get('min', mw)))
        ml = max(mf, float(declared.get('loaded_min', ml)))
    share = lambda m: float(m.sum()) / max(1, len(th_f))   # noqa: E731
    s_wall, s_feat = share(th_f < mw - 0.05), share(th_f < mf - 0.05)
    inl = np.zeros(len(P_f), bool)
    for bx in loaded_boxes:
        inl |= ((P_f[:, 0] >= bx[0]) & (P_f[:, 0] <= bx[1]) & (P_f[:, 1] >= bx[2]) & (P_f[:, 1] <= bx[3]) &
                (P_f[:, 2] >= bx[4]) & (P_f[:, 2] <= bx[5]))
    # r2 R3: no loaded samples -> None (not 0.0): an empty zone set is not evidence of adequate thickness
    s_load = float((th_f[inl] < ml - 0.05).sum()) / max(1, inl.sum()) if inl.any() else None
    order = np.argsort(th_f)[:6]
    ok = s_wall <= 0.02 and s_feat <= 0.005 and (s_load is None or s_load <= 0.02)
    thn = np.where(np.isfinite(th_n), th_n, 6.0)
    return dict(declared_exception=declared, wall_threshold=mw, normal_ray=dict(p1=_r(np.percentile(thn, 1)) if len(thn) else None,
                                share_below_min_wall=_r(float((thn < mw - 0.05).mean()) if len(thn) else 0.0, 4)),
                part=pid, samples=int(len(th_f)), min=_r(th_f.min()) if len(th_f) else None,
                p1=_r(np.percentile(th_f, 1)) if len(th_f) else None, p5=_r(np.percentile(th_f, 5)) if len(th_f) else None,
                share_below_min_wall=_r(s_wall, 4), share_below_min_feature=_r(s_feat, 4),
                loaded_samples=int(inl.sum()), share_loaded_below_1_6=_r(s_load, 4), loaded_zones=len(loaded_boxes),
                role='secondary screen (share-based); local thickness is gated by critical_features',
                thinnest=[dict(t=_r(th_f[i]), at=[_r(x, 1) for x in P_f[i]]) for i in order],
                below_min_wall=[dict(t=_r(th_f[i]), at=[_r(x, 2) for x in P_f[i]])      # r2 R3: for classification
                                for i in np.argsort(th_f)[:200] if th_f[i] < mw - 0.05],
                status='pass' if ok else 'fail',
                method='wall = max over a 30 deg cone of inward rays of hit x cos tilt (7 rays, tessellation 0.08 mm)')


def loaded_boxes(L, pid):
    """Zones where walls must be >= 1.6 (bosses, posts, pads, hooks, lips) for part pid."""
    Z = []
    if pid == 'panel':
        Z += [box_bb(b) for b in list(L.PANEL_BOSSES.values()) + list(L.PANEL_POSTS.values())]
        Z.append(box_bb(L.PANEL_TONGUE))
    if pid == 'tub':
        for p in L.RIGHT_WALL_PADS.values():
            Z.append((p['c'][0] - 6, p['c'][0] + 6, L.YR, p['y'][1], p['c'][1] - 6, p['c'][1] + 6))
        for (hx, hy) in L.PI['holes']:
            Z.append((hx - 3.5, hx + 3.5, hy - 3.5, hy + 3.5, L.T, L.PI_BOSS['z'][1]))
        Z.append(box_bb(L.LIP))
        for k, zb in snap_zones(L).items():          # Pi floor hooks (beam above the floor relief)
            if k.startswith('pih'):
                Z.append((zb[0], zb[1], zb[2], zb[3], L.T, L.PI_HOOK['catch_z'] - 0.3))
    if pid == 'hood':     # hook beams only: from just above the tooth top to the band underside
        for zb in clearance_zones(L)[:4]:
            b = zb[3]
            Z.append((b[0], b[1], b[2], b[3], L.HOOK['tooth_top_z'] + 0.3, b[5]))
        Z.append(box_bb(L.HOOD_RAIL['box']))         # groove lips (J2)
    # r5 (judge 3 s6.9): the collar insert bosses (tub) and the collar feet / pinch lugs (lens_collar) carry the lens
    for b in (getattr(L, 'TUB_INSERT_BOSSES', None) or {}).values() if pid == 'tub' else ():
        r = b['od'] / 2
        Z.append((b['x'][0], b['x'][1], b['c'][0] - r, b['c'][0] + r, b['c'][1] - r, b['c'][1] + r))
    if pid == 'lens_collar':
        C = L.COLLAR
        r = C['foot_d'] / 2
        Z += [(C['foot_x'][0], C['foot_x'][1], y - r, y + r, z - r, z + r) for y, z in C['feet'].values()]
        lg = C['lug']
        front = max(c['front_x'] for c in (L.collar_spec(n) for n in L.LENSES) if c)
        Z.append((lg['x'][0], front if lg['x'][1] is None else lg['x'][1], lg['y_out'], lg['bit_relief_y'],
                  lg['lower_z'][0], lg['upper_z'][1]))
    return Z


# ------------------------------------------------------------------------------------------- 6. straight driver
def check_driver(L, rows, screw_ids=None, audit_set_of=None, context=None):
    """Straight-driver audit. r2 (R3): screw_ids / audit_set_of(screw id) -> ids let the service-path check audit a
    screw in the SERVICE state (removal context) instead of its build step."""
    out = []
    D = L.DRIVER
    audit = audit_set_of or L.screw_audit_set
    for s in L.SCREWS:
        if screw_ids is not None and s['id'] not in screw_ids:
            continue
        hp, ax = s['head_point'], s['axis']
        bit = dc.cyl_along(D['bit_d'] / 2, -D['bit_len'], 0.0, hp, ax)
        handle = dc.cyl_along(D['handle_d'] / 2, -D['bit_len'] - D['handle_len'], -D['bit_len'], hp, ax)
        hits, stub = [], False
        for pid in audit(s['id']):
            r = rows.get(pid)
            if r is None or r.get('shape') is None:
                continue
            for nm, tool in (('bit', bit), ('handle', handle)):
                if not bb_overlap(bb_tuple(r['shape']), bb_tuple(tool)):
                    continue
                v, cs = common(r['shape'], tool)
                if v > VOL_TOL:
                    hits.append(dict(part=pid, tool=nm, volume_mm3=_r(v, 3), stub=bool(r.get('stub'))))
                    stub |= bool(r.get('stub'))
        clear = {}
        # r5 (brief choice 8): the audit applies to every kind; the head height comes from the screw's kind (PT / M3)
        hh = (getattr(L, 'M3', None) or L.PT)['head_h'] if s.get('kind', 'PT') == 'M3' else L.PT['head_h']
        bit_back = dc.cyl_along(D['bit_d'] / 2, -D['bit_len'], -hh - 0.1, hp, ax)   # behind the head
        for nm, tool in (('bit', bit_back), ('handle', handle)):   # nearest present solid (within 15 mm of the tool)
            tb = bb_tuple(tool)
            best = None
            for pid in audit(s['id']):
                r = rows.get(pid)
                if r is None or r.get('shape') is None or not bb_overlap(bb_tuple(r['shape']), tb, 15.0):
                    continue
                try:
                    d = r['shape'].distance(tool)
                except Exception:  # noqa: BLE001
                    continue
                if best is None or d < best[0]:
                    best = (d, pid)
            clear[nm] = None if best is None else dict(gap=_r(best[0], 2), part=best[1])
        st = 'pass' if not hits else ('stub' if all(h['stub'] for h in hits) else 'fail')
        out.append(dict(nearest=clear, screw=s['id'], step=s['step'], axis=list(ax), head_point=list(hp), bit=[D['bit_d'], D['bit_len']],
                        handle=[D['handle_d'], D['handle_len']], audit_set=audit(s['id']), hits=hits,
                        status=st, **({} if context is None else dict(context=context))))
    return out


# ------------------------------------------------------------------------------------------- 7. insertion sweeps
def snap_zones(L):
    z = {}
    for zb in clearance_zones(L)[:4]:
        z[zb[0].split()[2]] = zb[3]
    for h in L.PI_HOOKS:
        ax, v = h['face']
        if ax == 'x':
            z[h['id']] = (v - 4.0, v + 2.0, h['at'] - 5.0, h['at'] + 5.0, 0.0, 10.5)
        else:
            z[h['id']] = (h['at'] - 5.0, h['at'] + 5.0, v - 2.0, v + 4.0, 0.0, 10.5)
    if 'skirt_l' in L.PARTS and getattr(L, 'SKIRT_JOINT', None):   # r2 (R3): skb zones only while the skirts exist
        sj, bx = L.SKIRT_JOINT, L.BASE    # J5 skirt barbs (INTEGRATOR): the barb rides the groove floor for its last mm
        gz, xb = sj['groove_z'], sj['barb']['x']
        z['skb_l'] = (bx['x'][0] - 2.0, xb + 3.0, bx['y'][1] - 3.0, bx['y'][1] + 0.5, gz[0] - 0.5, gz[1] + 0.5)
        z['skb_r'] = (bx['x'][0] - 2.0, xb + 3.0, bx['y'][0] - 0.5, bx['y'][0] + 3.0, gz[0] - 0.5, gz[1] + 0.5)
    for k, zb in (getattr(L, 'SNAP_ZONES_EXTRA', None) or {}).items():   # r2: R1/R2 latch zones, dict id -> B() box
        z[k] = box_bb(zb)
    return z


def _path_points(path, step=2.0):
    pts = []
    for p0, p1 in zip(path[:-1], path[1:]):
        d = math.dist(p0, p1)
        n = max(1, int(math.ceil(d / step)))
        for i in range(n):
            f = i / n
            pts.append(tuple(p0[k] + (p1[k] - p0[k]) * f for k in range(3)))
    last = path[-2]
    d = math.dist(last, path[-1])
    for e in (1.0, 0.5):                                    # close approach before the final pose
        if d > e:
            pts.append(tuple(path[-1][k] + (last[k] - path[-1][k]) * e / d for k in range(3)))
    return pts


def reach_margin(L, length):
    """r7 (PLAN s2): the one lead-reach allowance, shared by mate_reach and lead_access: max(MATE_MARGIN,
    ROUTE_ALLOWANCE[0], ROUTE_ALLOWANCE[1] x length) (= SPEC-C3's allowance(L) with ROUTE_ALLOWANCE (10, 0.10))."""
    return max(getattr(L, 'MATE_MARGIN', ROUTE_ALLOWANCE[0]), ROUTE_ALLOWANCE[0], ROUTE_ALLOWANCE[1] * length)


def _ins_seq(L, ins_id):
    for n, i in enumerate(L.INSERTIONS):
        if i['id'] == ins_id:
            return (i['step'], float(n))
    return None


def plug_seq(L, mated):
    """r7 C1: sort key of a PLUGS `mated` moment: ('bench', s) -> (s, -1); ('before'|'after', J) -> J -+ 0.5."""
    kind, ref = mated
    if kind == 'bench':
        return (ref, -1.0)
    s = _ins_seq(L, ref)
    if s is None:
        return None
    return (s[0], s[1] + (-0.5 if kind == 'before' else 0.5))


def _plug_box(L, p):
    b = p.get('box')
    if b is None:
        return None
    return box_bb(L.KEEPOUTS[b]) if isinstance(b, str) else box_bb(b)


def _plug_name(p):
    return p['box'] if isinstance(p.get('box'), str) else p['id']


def carried_plugs(L, ins, n=None, removal=False):
    """r7 C1 (s4.1): rigid boxed PLUGS whose end moves with `ins` and that are mated before it. For a removal the
    service state has every plug mated: carried unless the plug is in rem['unplug']."""
    out = []
    for p in getattr(L, 'PLUGS', []) or []:
        if not (p.get('rigid') and p.get('box') and p['end'] in ins['moving']):
            continue
        if removal:
            if p['id'] not in (ins.get('unplug') or []):
                out.append(p)
            continue
        sq, si = plug_seq(L, p['mated']), (ins['step'], float(n))
        if sq is not None and sq < si:
            out.append(p)
    return out


def fixed_end_plugs(L, ins, n=None, removal=False, present=()):
    """r7 C1 (s4.1, second half of the defect class): for every cable with exactly one end moved by `ins`, the rigid
    boxed plug at the other (fixed) end stays a hard obstacle when it is mated at that moment (and its part present)."""
    out = []
    mv = set(ins['moving'])
    ends_of = getattr(L, 'CABLE_ENDS', None) or CABLE_ENDS
    for cab, ends in ends_of.items():
        moved = [e for e in ends if e in mv]
        if len(moved) != 1:
            continue
        fixed = [e for e in ends if e not in mv]
        for p in getattr(L, 'PLUGS', []) or []:
            if p['cable'] != cab or p['end'] not in fixed or not p.get('box') or p['end'] not in present:
                continue
            if removal:
                ok = p['id'] not in (ins.get('unplug') or [])
            else:
                sq = plug_seq(L, p['mated'])
                ok = sq is not None and sq < (ins['step'], float(n))
            if ok:
                out.append(p)
    return out


def _bb_cube(m3, b):
    return m3.Manifold.cube([b[1] - b[0], b[3] - b[2], b[5] - b[4]]).translate([b[0], b[2], b[4]])


def keepout_kind_of(L, k):
    """r7 C1: 'plug' (rigid connector body) or 'cable' (default) per layout.KEEPOUT_KIND."""
    return (getattr(L, 'KEEPOUT_KIND', None) or {}).get(k, 'cable')


def _own_via(L, cable_id):
    for c in L.CABLES:
        if c['id'] == cable_id:
            s = c.get('stow')      # r7 C2: `stow` is one KEEPOUTS id (a str), not a list
            return set(c.get('via') or []) | ({s} if isinstance(s, str) else set(s or []))
    return set()


def carry_boxes(L, ins, n=None, removal=False):
    """r7 (PLAN s2): the carried boxes of one insertion (or removal): rigid boxed PLUGS (kind 'plug') and C3 `riders`
    (kind 'rider', taped lead lanes). Each ignores its own cable's route and stow boxes and itself.
    -> [(name, bbox, kind, exclude set)]"""
    out = []
    for p in carried_plugs(L, ins, n, removal=removal):
        out.append((p['id'], _plug_box(L, p), 'plug', _own_via(L, p['cable']) | {_plug_name(p)}))
    for k in ins.get('riders') or []:
        if k not in L.KEEPOUTS:      # r7 C3: check_sweeps fails the row ('rider not in KEEPOUTS')
            continue
        own = set()
        for c in L.CABLES:
            if k in (c.get('via') or []):
                own |= _own_via(L, c['id'])
        out.append((k, box_bb(L.KEEPOUTS[k]), 'rider', own | {k}))
    return out


def _carried_sweep(L, m3, cboxes, pts, targets, kinds):
    """r7 (PLAN s2): ONE carried-box routine. cboxes: [(name, bb, kind 'plug'|'rider', exclude set)]; targets:
    [(id, manifold, bb)]; kinds: id -> 'solid' | 'plug' | 'cable'. kind 'plug' is hard against solids and 'plug'
    keep-outs and soft (<= CARRY_SOFT_MM, smallest extent of the overlap box) against 'cable' keep-outs; kind
    'rider' is hard against everything. Returns (worst hard hits {(name, o): (v, p, bbox)}, soft contacts)."""
    worst, soft = {}, {}
    for name, cb, ckind, excl in cboxes:
        cm = _bb_cube(m3, cb)
        for o, om, obb in targets:
            if o in excl or om is None:
                continue
            for p in pts:
                sbb = (cb[0] + p[0], cb[1] + p[0], cb[2] + p[1], cb[3] + p[1], cb[4] + p[2], cb[5] + p[2])
                if not bb_overlap(sbb, obb, -1e-6):
                    continue
                inter = cm.translate(list(p)) ^ om
                v = inter.volume()
                if v <= 1e-9:
                    continue
                ib = inter.bounding_box()
                if ckind == 'plug' and kinds.get(o) == 'cable':
                    pen = min(ib[3] - ib[0], ib[4] - ib[1], ib[5] - ib[2])
                    if pen > soft.get((name, o), (0.0,))[0]:
                        soft[(name, o)] = (pen, v, p)
                    continue
                if v > SWEEP_TOL and v > worst.get((name, o), (0.0,))[0]:
                    worst[(name, o)] = (v, p, [_r(x, 1) for x in ib])
    soft_rows = [dict(carried=n_, keepout=o, penetration_mm=_r(pen, 3), volume_mm3=_r(v, 2),
                      at_offset=[_r(x, 1) for x in p], limit_mm=CARRY_SOFT_MM, ok=pen <= CARRY_SOFT_MM + 1e-6)
                 for (n_, o), (pen, v, p) in sorted(soft.items())]
    return worst, soft_rows


def check_sweeps(L, rows, step_mm=2.0, only=None):
    import manifold3d as m3
    mates = mate_table(L)
    zones = snap_zones(L)
    man_cache = {}

    def man(i):
        if i not in man_cache:
            man_cache[i] = manifold_of(rows[i]['shape']) if rows.get(i, {}).get('shape') is not None else None
        return man_cache[i]

    out = []
    carried_final = {}      # r7: step -> [(name, final bbox)] of carried boxes already home (PLAN s2, C3's rule)
    for n, ins in enumerate(L.INSERTIONS):
        if only is not None and only not in ins['moving'] and only not in L.present_at(ins['step']):
            carried_final.setdefault(ins['step'], []).extend((nm, cb) for nm, cb, _k, _e in carry_boxes(L, ins, n))
            continue
        later = set()
        for o in L.INSERTIONS[n + 1:]:
            if o['step'] == ins['step']:
                later |= set(o['moving'])
        moving = [m for m in ins['moving'] if m in rows]
        obst = [i for i in L.present_at(ins['step']) if i not in ins['moving'] and i not in later
                and not i.startswith('s_') and i in rows]
        snap_boxes = [zb for k, zb in zones.items() if k in ins.get('snaps', [])]
        allowed_snap = [m3.Manifold.cube([zb[1] - zb[0], zb[3] - zb[2], zb[5] - zb[4]]).translate([zb[0], zb[2], zb[4]])
                        for k, zb in zones.items() if k in ins.get('snaps', [])]
        active_ko = []
        before = set(L.present_at(ins['step'] - 1))
        for cab in L.CABLES:      # a cable is in the body once one of its ends is (and it was plugged earlier)
            ends = set(cab.get('ends') or CABLE_ENDS.get(cab['id'], ()))
            if min(cab['steps']) < ins['step'] and (ends & before) and not (ends & set(ins['moving'])):
                active_ko += [k for k in cab['via'] if k not in ins.get('ignore', [])]
                if cab.get('stow') and cab['stow'] not in ins.get('ignore', []):   # r7 C2 (SPEC-C2 3.2-6c)
                    active_ko.append(cab['stow'])
        hits, worst, stub, err = [], {}, False, []
        pts = _path_points(ins['path'], step_mm)
        # r7 C1 (PLAN s2): fixed-end rigid plugs stay hard obstacles; carried boxes of earlier same-step insertions are
        #     final-pose obstacles; both are extra box targets for the part movers and for the carried boxes
        here = set(L.present_at(ins['step'])) - later
        fixed = fixed_end_plugs(L, ins, n, present=here)
        xbox = {}
        for p in fixed:
            nm = _plug_name(p)
            if nm not in active_ko:
                xbox[nm] = _plug_box(L, p)
        for nm, cb in carried_final.get(ins['step'], []):
            xbox['carried:' + nm] = cb
        hdr_on = []        # r7 C2 (SPEC-C2 3.2-6d): header housings are obstacles once their header plug is mated
        if getattr(L, 'HEADER_HOUSINGS', None) and 'pi5' in here and 'pi5' not in ins['moving']:
            hp = {p['cable']: p for p in getattr(L, 'PLUGS', []) or [] if p['end'] == 'pi5'}
            for (hc, _t, pins), hb in header_housing_boxes(L):
                sq = plug_seq(L, hp[hc]['mated']) if hc in hp else None
                if sq is not None and sq < (ins['step'], float(n)):
                    xbox['hdr:%s:%s' % (hc, '/'.join(str(x) for x in pins))] = hb
                    hdr_on.append('hdr:%s:%s' % (hc, '/'.join(str(x) for x in pins)))
        box_def = dict(L.KEEPOUTS)
        box_def.update({k: dict(x=(b[0], b[1]), y=(b[2], b[3]), z=(b[4], b[5])) for k, b in xbox.items()})
        xtargets = [(k, _bb_cube(m3, b), b) for k, b in sorted(xbox.items())]
        # r7 C2 (SPEC-C2 3.2-6b): a stow box filled during this insertion is an obstacle for the moving set (part
        #     movers and carried boxes) at path points no further than its waypoint from the final pose
        stw = [(k, float(f), _bb_cube(m3, box_bb(L.KEEPOUTS[k])), box_bb(L.KEEPOUTS[k]))
               for k, f in sorted((ins.get('stowed') or {}).items())]
        for mv in moving:
            for k, f, km, kb in stw:
                mm_ = man(mv)
                if mm_ is None:
                    continue
                mbb_ = bb_tuple(rows[mv]['shape'])
                for p in pts:
                    if math.sqrt(sum(x * x for x in p)) > f + 1e-9:
                        continue
                    sbb = (mbb_[0] + p[0], mbb_[1] + p[0], mbb_[2] + p[1], mbb_[3] + p[1], mbb_[4] + p[2], mbb_[5] + p[2])
                    if not bb_overlap(sbb, kb, -1e-6):
                        continue
                    v = (mm_.translate(list(p)) ^ km).volume()
                    if v > SWEEP_TOL and v > worst.get((mv, k), (0, None))[0]:
                        worst[(mv, k)] = (v, p, [])
        for mv in moving:
            mm = man(mv)
            if mm is None:
                err.append('no manifold mesh for %s (exact OCP fallback used)' % mv)
            mbb = bb_tuple(rows[mv]['shape'])
            targets = [(o, man(o), bb_tuple(rows[o]['shape'])) for o in obst]
            kind_skip = {o for o in obst if (mates.get(frozenset((mv, o))) or '').split(' ')[0] in
                         ('press', 'thread', 'interference')}
            targets += [(k, m3.Manifold.cube([b['x'][1] - b['x'][0], b['y'][1] - b['y'][0], b['z'][1] - b['z'][0]])
                         .translate([b['x'][0], b['y'][0], b['z'][0]]), box_bb(b))
                        for k, b in ((k, L.KEEPOUTS[k]) for k in sorted(set(active_ko)))]
            targets += xtargets
            for o, om, obb in targets:
                if o in kind_skip:
                    continue
                exact = mm is None or om is None
                if om is None and o in rows:
                    err.append('no manifold mesh for %s (exact OCP fallback used)' % o)
                for p in pts:
                    sbb = (mbb[0] + p[0], mbb[1] + p[0], mbb[2] + p[1], mbb[3] + p[1], mbb[4] + p[2], mbb[5] + p[2])
                    if not bb_overlap(sbb, obb, -1e-6):
                        continue
                    if exact:
                        osh = rows[o]['shape'] if o in rows else dc.box_solid(box_def[o])
                        inter = rows[mv]['shape'].translate(V(*p)).intersect(osh)
                        try:
                            v0 = inter.Volume()
                        except Exception:  # noqa: BLE001 - null result = no overlap
                            v0 = 0.0
                        if v0 > 1e-9:
                            for zb in snap_boxes:
                                try:
                                    inter = inter.cut(cq.Solid.makeBox(zb[1] - zb[0], zb[3] - zb[2], zb[5] - zb[4],
                                                                       V(zb[0], zb[2], zb[4])))
                                except Exception:  # noqa: BLE001
                                    break
                        try:
                            v = inter.Volume() if v0 > 1e-9 else 0.0
                        except Exception:  # noqa: BLE001
                            v = 0.0
                        ibb = list(bb_tuple(inter)) if v > 1e-9 else []
                    else:
                        inter = mm.translate(list(p)) ^ om
                        for z in allowed_snap:
                            inter = inter - z
                        v = inter.volume()
                        ibb = list(inter.bounding_box()) if v > 1e-9 else []
                    if v > SWEEP_TOL:
                        key = (mv, o)
                        if v > worst.get(key, (0, None))[0]:
                            worst[key] = (v, p, [_r(x, 1) for x in ibb])
                        stub |= bool(rows[mv].get('stub') or (o in rows and rows[o].get('stub')))
        for (mv, o), (v, p, bbx) in worst.items():
            hits.append(dict(moving=mv, obstacle=o, max_volume_mm3=_r(v, 2), at_offset=[_r(x, 1) for x in p],
                             where=bbx, stub=bool(rows[mv].get('stub') or (o in rows and rows[o].get('stub')))))
        # r7 C1 (PLAN s2, SPEC-C1 4.1): the carried boxes (rigid plugs mated earlier whose end moves; C3 riders)
        cbx = carry_boxes(L, ins, n)
        err += ['rider not in KEEPOUTS: %s' % k for k in ins.get('riders') or [] if k not in L.KEEPOUTS]   # r7 C3
        ctargets =[(o, man(o), bb_tuple(rows[o]['shape'])) for o in obst]
        ctargets += [(k, _bb_cube(m3, box_bb(L.KEEPOUTS[k])), box_bb(L.KEEPOUTS[k])) for k in sorted(set(active_ko))]
        ctargets += xtargets
        kinds = {o: 'solid' for o in obst}
        kinds.update({k: keepout_kind_of(L, k) for k in set(active_ko)})
        kinds.update({k: 'plug' for k in xbox})
        cworst, soft_rows = _carried_sweep(L, m3, cbx, pts, ctargets, kinds)
        for k, f, km, kb in stw:       # r7 C2: the stow box against the carried boxes from its waypoint on
            sw_, ss_ = _carried_sweep(L, m3, cbx, [p for p in pts if math.sqrt(sum(x * x for x in p)) <= f + 1e-9],
                                      [(k, km, kb)], {k: keepout_kind_of(L, k)})
            cworst.update(sw_)
            soft_rows += ss_
        for (nm, o), (v, p, bbx) in cworst.items():
            hits.append(dict(moving=nm, obstacle=o, max_volume_mm3=_r(v, 2), at_offset=[_r(x, 1) for x in p],
                             where=bbx, carried=True, stub=bool(o in rows and rows[o].get('stub'))))
        for s in soft_rows:
            if not s['ok']:
                hits.append(dict(moving=s['carried'], obstacle=s['keepout'], max_volume_mm3=s['volume_mm3'],
                                 at_offset=s['at_offset'], carried=True, stub=False,
                                 error='soft contact %.2f mm > CARRY_SOFT_MM %.1f' % (s['penetration_mm'],
                                                                                     CARRY_SOFT_MM)))
        carried_final.setdefault(ins['step'], []).extend((nm, cb) for nm, cb, _k, _e in cbx)
        fx = []
        for p in fixed:
            nm = _plug_name(p)
            vs = [h['max_volume_mm3'] for h in hits if h['obstacle'] == nm]
            fx.append(dict(plug=p['id'], keepout=nm, max_volume_mm3=max(vs) if vs else 0.0))
        hard_err = [e for e in err if 'fallback' not in e]
        st = 'pass' if not hits and not hard_err else ('stub' if hits and all(h['stub'] for h in hits) and not hard_err
                                                      else 'fail')
        out.append(dict(insertion=ins['id'], step=ins['step'], moving=ins['moving'], obstacles=obst,
                        keepouts=sorted(set(active_ko)), snaps=ins.get('snaps', []), positions=len(pts), hits=hits,
                        carried=[c[0] for c in cbx], soft_contacts=[s for s in soft_rows if s['ok']],
                        fixed_end_obstacles=fx, stowed=list(ins.get('stowed') or []), header_housings=hdr_on,
                        riders=list(ins.get('riders') or []),
                        errors=err, status=st, method='manifold3d mesh boolean, tessellation 0.05 mm, tol %.1f mm3'
                        % SWEEP_TOL))
    return out


# ------------------------------------------------------------------------------------------- 7b. mate paths (r7 C1)
def _ins_index(L, ins_id):
    return next((n for n, i in enumerate(L.INSERTIONS) if i['id'] == ins_id), None)


def _moment(L, rows, after=None, state=None, screws=True):
    """r7 C1: (ids present with a shape, step, removal or None) at a moment: after=<insertion id> (its step, its movers
    home, later same-step movers absent) or state='service:<REMOVALS id>' (service state, moving set still in place)."""
    if state:
        rem = next(r for r in registry(L, 'REMOVALS') if r['id'] == state.split(':', 1)[1])
        ids = service_context(L, rows, rem) + [m for m in rem['moving'] if m in rows]
        step = max(s['step'] for s in L.STEPS)
    else:
        n = _ins_index(L, after)
        ins = L.INSERTIONS[n]
        step = ins['step']
        later = set()
        for o in L.INSERTIONS[n + 1:]:
            if o['step'] == step:
                later |= set(o['moving'])
        ids = [i for i in L.present_at(step) if i not in later]
        rem = None
    ids = [i for i in ids if i in rows and rows[i].get('shape') is not None and (screws or not i.startswith('s_'))]
    return ids, step, rem


def _moment_keepouts(L, ids, step):
    """Cable keep-outs active at a moment: cables plugged by then with an end present."""
    out = set()
    for cab in L.CABLES:
        ends = set(cab.get('ends') or CABLE_ENDS.get(cab['id'], ()))
        if min(cab['steps']) <= step and (ends & set(ids)):
            out |= set(cab['via'])
    return out


def _box_vol(a, b):
    d = [min(a[2 * i + 1], b[2 * i + 1]) - max(a[2 * i], b[2 * i]) for i in range(3)]
    return d[0] * d[1] * d[2] if min(d) > 0 else 0.0


def _solid_hits(m3, man, rows, ids, cb, tol=SWEEP_TOL):
    cm, out = _bb_cube(m3, cb), []
    for o in ids:
        if not bb_overlap(cb, bb_tuple(rows[o]['shape']), -1e-6):
            continue
        om = man(o)
        if om is None:
            out.append(dict(obstacle=o, error='no manifold mesh'))
            continue
        v = (cm ^ om).volume()
        if v > tol:
            out.append(dict(obstacle=o, volume_mm3=_r(v, 2)))
    return out


def check_mate_paths(L, rows, sweep_rows=None, step_mm=1.0):
    """r7 C1 (SPEC-C1 4.2 + Plan edits P1-4/P1-6/P1-9): plug_in (in-situ plug paths), access (hand/tool corridors)
    and coverage (PLUGS per cable end, carried lists, ACCESS ignores). Pass = 0 mm3 (SWEEP_TOL) everywhere."""
    import manifold3d as m3
    cache = {}

    def man(i):
        if i not in cache:
            cache[i] = manifold_of(rows[i]['shape'])
        return cache[i]

    plugs = {p['id']: p for p in getattr(L, 'PLUGS', []) or []}
    out = []
    for p in plugs.values():                                   # 1. plug_in
        if not p.get('path'):
            continue
        kind, ref = p['mated']
        ids, step, _ = _moment(L, rows, after=ref if kind == 'after' else None, screws=False) if kind == 'after' \
            else (None, None, None)
        if ids is None:
            out.append(dict(kind='plug_in', id=p['id'], status='fail', error='in-situ path needs mated (after, J)'))
            continue
        body, head, stroke = _plug_box(L, p), (box_bb(p['head']) if p.get('head') else None), p.get('stroke', 0.0)
        own = _own_via(L, p['cable'])
        hard_ko = sorted(k for k in _moment_keepouts(L, ids, step) if keepout_kind_of(L, k) == 'plug' and k not in own)
        pts = _path_points(p['path'], step_mm) + [tuple(p['path'][-1])]
        worst = {}
        for nm, bb in (('body', body), ('head', head)):
            if bb is None:
                continue
            for q in pts:
                sb = (bb[0] + q[0], bb[1] + q[0], bb[2] + q[1], bb[3] + q[1], bb[4] + q[2], bb[5] + q[2])
                mating = nm == 'head' and math.dist(q, p['path'][-1]) <= stroke + 1e-9
                tids = [o for o in ids if not (mating and o == p['end'])]
                for h in _solid_hits(m3, man, rows, tids, sb):
                    if h.get('volume_mm3', 0) > worst.get((nm, h['obstacle']), (0,))[0] or 'error' in h:
                        worst[(nm, h['obstacle'])] = (h.get('volume_mm3', 0), q, h.get('error'))
                for k in hard_ko:
                    v = _box_vol(sb, box_bb(L.KEEPOUTS[k]))
                    if v > VOL_TOL and v > worst.get((nm, k), (0,))[0]:
                        worst[(nm, k)] = (_r(v, 2), q, None)
        hits = [dict(part=nm, obstacle=o, max_volume_mm3=v, at_offset=[_r(x, 1) for x in q], error=e)
                for (nm, o), (v, q, e) in sorted(worst.items())]
        eb = bb_tuple(rows[p['end']]['shape']) if p['end'] in rows else None
        out.append(dict(kind='plug_in', id=p['id'], cable=p['cable'], end=p['end'], moment=list(p['mated']),
                        path=[list(x) for x in p['path']], stroke=stroke, positions=len(pts) * (2 if head else 1),
                        obstacles=ids, hard_keepouts=hard_ko, hits=hits,
                        final_gap_to_end=None if eb is None else _r(_box_gap(body, eb), 3),
                        head_top_lowest=None if head is None else _r(head[5] + min(q[2] for q in p['path']), 2),
                        status='fail' if hits else 'pass'))
    out += _mate_access_rows(L, rows, plugs, man, m3)          # 2. access
    out += _mate_coverage_rows(L, plugs, sweep_rows)           # 3. coverage
    return out


def _mate_access_rows(L, rows, plugs, man, m3):
    """r7 C1: every ACCESS corridor is empty at its moment (parts present then + active cable keep-outs - ignore)."""
    out = []
    fmm = getattr(L, 'FINGERTIP_MM', 9.0)
    for a in getattr(L, 'ACCESS', []) or []:
        row = dict(kind='access', id=a['id'], moment=a.get('after') or a.get('state'), tool=a.get('tool', ''),
                   ignore=list(a.get('ignore') or []))
        try:
            ids, step, _ = _moment(L, rows, after=a.get('after'), state=a.get('state'))
        except (StopIteration, TypeError, IndexError):
            out.append(dict(row, status='fail', error='unknown moment'))
            continue
        boxes = [box_bb(b) for b in (a.get('boxes') or [a['box']])]
        if a.get('push_of'):
            p = plugs.get(a['push_of'])
            if p is None or _plug_box(L, p) is None:
                out.append(dict(row, status='fail', error='push_of plug %s missing' % a['push_of']))
                continue
            z1 = _plug_box(L, p)[4] - p.get('stroke', 0.0)
            boxes = [(b[0], b[1], b[2], b[3], b[4], z1) for b in boxes]
            row['push_height_mm'] = _r(z1 - boxes[0][4], 2)
            row['fingertip_mm'] = fmm
            row['push_method'] = 'fingertip' if z1 - boxes[0][4] >= fmm - 1e-9 else 'push_stick'
        kos = sorted(k for k in _moment_keepouts(L, ids, step) if k not in (a.get('ignore') or []))
        hits = []
        for b in boxes:
            if b[5] - b[4] <= 0:
                hits.append(dict(obstacle='(no room)', error='corridor height <= 0'))
                continue
            hits += _solid_hits(m3, man, rows, ids, b)
            hits += [dict(obstacle=k, volume_mm3=_r(_box_vol(b, box_bb(L.KEEPOUTS[k])), 2)) for k in kos
                     if _box_vol(b, box_bb(L.KEEPOUTS[k])) > VOL_TOL]
        out.append(dict(row, boxes=[[_r(x, 2) for x in b] for b in boxes], present=ids, keepouts=kos, hits=hits,
                        status='fail' if hits else 'pass'))
    return out


def _mate_coverage_rows(L, plugs, sweep_rows=None):
    """r7 C1: one PLUGS entry per CABLE_ENDS (cable, end); boxes and mate moments exist; every carried plug shows in
    its insertion's sweeps row; every ACCESS ignore has a sequence reason (P1-9)."""
    ce = getattr(L, 'CABLE_ENDS', None) or CABLE_ENDS
    pairs = [(c, e) for c, ends in ce.items() for e in ends]
    have = {}
    for p in plugs.values():
        have.setdefault((p['cable'], p['end']), []).append(p['id'])
    gaps = ['%s/%s' % ce_ for ce_ in pairs if len(have.get(ce_, [])) != 1]
    extra = ['%s (%s/%s)' % (i, c, e) for (c, e), v in have.items() if (c, e) not in pairs for i in v]
    ins_ids = {i['id'] for i in L.INSERTIONS}
    bad = []
    for p in plugs.values():
        if isinstance(p.get('box'), str) and p['box'] not in L.KEEPOUTS:
            bad.append('%s: box %s not in KEEPOUTS' % (p['id'], p['box']))
        k, ref = p['mated']
        if (k == 'bench' and ref not in {s['step'] for s in L.STEPS}) or (k != 'bench' and ref not in ins_ids) \
                or k not in ('bench', 'before', 'after'):
            bad.append('%s: mated %r unknown' % (p['id'], p['mated']))
    out = [dict(kind='coverage', id='plugs_per_cable_end', n=len(pairs), covered=len(pairs) - len(gaps), gaps=gaps,
                extra=extra, errors=bad, status='fail' if (gaps or extra or bad) else 'pass')]
    srow = {r['insertion']: r for r in (sweep_rows or []) if 'insertion' in r}
    miss = []
    for m, ins in enumerate(L.INSERTIONS):
        names = srow[ins['id']].get('carried', []) if ins['id'] in srow else [c[0] for c in carry_boxes(L, ins, m)]
        for p in plugs.values():
            if p.get('rigid') and p.get('box') and p['end'] in ins['moving']:
                sq = plug_seq(L, p['mated'])
                if sq is not None and sq < (ins['step'], float(m)) and p['id'] not in names:
                    miss.append('%s not carried by %s' % (p['id'], ins['id']))
    out.append(dict(kind='coverage', id='carried_lists', source='sweeps rows' if srow else 'carry_boxes',
                    missing=miss, status='fail' if miss else 'pass'))
    ign = []
    rems = {r['id']: r for r in registry(L, 'REMOVALS')}
    for a in getattr(L, 'ACCESS', []) or []:
        st = a.get('state')
        unplug = set((rems.get(st.split(':', 1)[1]) or {}).get('unplug') or []) if st else set()
        for k in a.get('ignore') or []:
            if k == a.get('dest'):
                continue
            ok = False
            for c in L.CABLES:
                if k not in (c.get('via') or []):
                    continue
                for p in plugs.values():
                    if p['cable'] == c['id'] and ((not st and tuple(p['mated']) == ('after', a.get('after')))
                                                  or (st and p['id'] in unplug)):
                        ok = True
            if not ok:
                ign.append('%s ignores %s without a sequence reason' % (a['id'], k))
    out.append(dict(kind='coverage', id='access_ignores', n=sum(len(a.get('ignore') or []) for a in
                                                                getattr(L, 'ACCESS', []) or []),
                    errors=ign, status='fail' if ign else 'pass'))
    out.append(_mate_pose_coverage_row(L, plugs))
    return out


def _mate_pose_coverage_row(L, plugs):
    """r7 (PLAN s2, Plan edit P1-5, lands with SPEC-C2): for every insertion J and every cable with exactly one end E
    moved by J, if the plug at E and the plug (or inline junction) at the other end are both mated before J, a
    MATE_POSES row for (cable, J) must exist. Rows whose both ends move are 'info' (not required). Every MATE_POSES
    row names an existing PLUGS id of its cable (or inline_of=<its cable>)."""
    ce = getattr(L, 'CABLE_ENDS', None) or CABLE_ENDS
    mps = getattr(L, 'MATE_POSES', None) or []
    have = {(m.get('cable'), m.get('insertion')) for m in mps}
    need, missing, info = [], [], []
    for n, ins in enumerate(L.INSERTIONS):
        mv, si = set(ins['moving']), (ins['step'], float(n))
        for cab, ends in ce.items():
            moved = [e for e in ends if e in mv]
            if len(moved) == 2:
                info.append('%s/%s' % (cab, ins['id']))
                continue
            if len(moved) != 1:
                continue
            other = [e for e in ends if e not in mv]
            pe = [p for p in plugs.values() if p['cable'] == cab and p['end'] == moved[0]]
            po = [p for p in plugs.values() if p['cable'] == cab and other and p['end'] == other[0]]
            seqs = [plug_seq(L, p['mated']) for p in pe + po]
            if pe and po and all(s is not None and s < si for s in seqs):
                need.append('%s/%s' % (cab, ins['id']))
                if (cab, ins['id']) not in have:
                    missing.append('%s/%s' % (cab, ins['id']))
    bad = []
    for m in mps:
        if m.get('plug'):
            p = plugs.get(m['plug'])
            if p is None or p['cable'] != m.get('cable'):
                bad.append('%s: plug %s is not a PLUGS id of %s' % (m.get('id'), m['plug'], m.get('cable')))
        elif m.get('inline_of') != m.get('cable'):
            bad.append('%s: names neither a plug nor inline_of=%s' % (m.get('id'), m.get('cable')))
    return dict(kind='coverage', id='mate_poses', required=need, missing=missing, both_moving=sorted(set(info)),
                errors=bad, status='fail' if (missing or bad) else 'pass',
                **({'error': 'no MATE_POSES row for ' + ', '.join(missing)} if missing else {}))


# ------------------------------------------------------------------------------------------- 8. mass and CoM
def mass_com(L, rows, lens_row):
    """Total mass and CoM; printed = volume x density x infill; COTS = listed masses at the proxy centroid."""
    tm, mx = 0.0, np.zeros(3)
    items = []
    for i, r in rows.items():
        if i == 'lens':
            continue
        if r.get('shape') is None:
            continue
        sh = r['shape']
        if r['kind'] == 'printed':
            m = L.mass_g(sh.Volume(), i)
        else:
            m = r.get('mass') or 0.0
        c = r.get('com') or (lambda cc: (cc.x, cc.y, cc.z))(cq.Shape.centerOfMass(sh))
        tm += m
        mx += m * np.array(c)
        items.append(dict(id=i, mass_g=_r(m, 2), com=[_r(x, 1) for x in c], stub=bool(r.get('stub'))))
    lm, lc = lens_row['mass'], lens_row['com']
    tm += lm
    mx += lm * np.array(lc)
    items.append(dict(id='lens', mass_g=lm, com=[_r(x, 1) for x in lc], name=lens_row['name']))
    com = mx / tm
    return dict(total_g=_r(tm, 1), com=[_r(x, 2) for x in com], lens=lens_row['name'],
                com_ahead_of_grip_axis=_r(com[0] - L.GRIP['axis_x'], 2),
                com_above_grip_top=_r(com[2] - L.GRIP['top_z'], 2), items=items,
                note='cables and solder not included; COTS masses are listing/estimate values at proxy centroids')


# ------------------------------------------------------------------------------------------- FIXER P1: groove width
def _raster_faces(faces, px):
    """Rasterise planar +Y faces (x, z) at px mm/pixel; returns a bool image (PIL polygon fill of the triangles)."""
    from PIL import Image, ImageDraw
    tri = []
    for f in faces:
        vs, ts = f.tessellate(0.02, 0.2)
        P = [(v.x, v.z) for v in vs]
        tri += [[P[i] for i in t] for t in ts]
    if not tri:
        return None
    xs = [p[0] for t in tri for p in t]
    zs = [p[1] for t in tri for p in t]
    x0, z0 = min(xs) - 1.0, min(zs) - 1.0
    W, H = int((max(xs) - x0 + 1.0) / px) + 1, int((max(zs) - z0 + 1.0) / px) + 1
    im = Image.new('1', (W, H), 0)
    dr = ImageDraw.Draw(im)
    for t in tri:
        dr.polygon([((p[0] - x0) / px, (p[1] - z0) / px) for p in t], fill=1)
    return np.array(im, dtype=bool)


def _morph(img, r_px, op):
    pad = r_px + 2
    a = np.pad(img, pad)
    out = np.ones_like(a) if op == 'erode' else np.zeros_like(a)
    for dy in range(-r_px, r_px + 1):
        for dx in range(-r_px, r_px + 1):
            if dx * dx + dy * dy > r_px * r_px:
                continue
            sh = np.roll(np.roll(a, dy, 0), dx, 1)
            out = (out & sh) if op == 'erode' else (out | sh)
    return out[pad:-pad, pad:-pad]


def check_engrave(L, px=0.04):
    """Groove width of every engraved glyph/stroke at the face plane: share of its area removed by a morphological
    opening with a disk of dia ENGRAVE_MIN_STROKE (= area narrower than the stroke). Pass: share <= ENGRAVE_MAX_THIN_SHARE
    for every glyph. Sectioned on the cutter solids (prisms normal to the face, so the bed-layer outline is the same)."""
    E, F = L.ENGRAVE, L.FDM
    mn, lim = F['ENGRAVE_MIN_STROKE'], F['ENGRAVE_MAX_THIN_SHARE']
    r_px = max(1, int(round(mn / 2 / px)))
    out = []
    for it in E['items']:
        worst, n = 0.0, 0
        for so in dc.engrave([it], face_y=E['face_y']):
            fs = [f for f in so.Faces() if abs(abs(f.normalAt().y) - 1.0) < 1e-6]
            if not fs:
                continue
            ytop = max(f.Center().y for f in fs)
            img = _raster_faces([f for f in fs if f.Center().y > ytop - 0.01], px)
            if img is None or not img.any():
                continue
            opened = _morph(_morph(img, r_px, 'erode'), r_px, 'dilate') & img
            worst = max(worst, 1.0 - opened.sum() / img.sum())
            n += 1
        out.append(dict(item=it['id'], kind=it['kind'], glyphs=n, worst_thin_share=_r(worst, 3), min_stroke=mn,
                        limit=lim, status='pass' if n and worst <= lim else 'fail'))
    return out


# ------------------------------------------------------------------------------------------- FIXER P5: PT bosses
def _own_copy(x):
    sh = x.val() if hasattr(x, 'val') else x
    return sh.copy()
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
