AubergineShallow/digital8mm/cad/gs8-d2-v1/run_locked.py

# SPDX-License-Identifier: MIT
"""Run one heavy CAD command at a time, and only when enough RAM is free.

The GS8 working tree is shared with other sessions and agents that run CAD builds, so every D2 CAD
process (build, part test, render, audit) goes through this wrapper (copied from cad/gs8-stills-v1):

    .venv-cad/Scripts/python.exe cad/gs8-d2-v1/run_locked.py [--min-free-mb 700] -- <script.py> [args...]

The script runs with the same interpreter as this wrapper. The wrapper:
- on POSIX, holds a kernel flock on a persistent .cad.lock inode; PID metadata is diagnostic only.
  The child inherits the descriptor, so a terminated wrapper cannot unlock a still-running build;
- on Windows, retains the original process-lock implementation;
- waits until free physical RAM is at least --min-free-mb (default 700);
- runs the command with PYTHONDONTWRITEBYTECODE=1 and returns its exit code.
Waiting is bounded by --max-wait-min, after which it exits 75 without running anything.
"""
import argparse
import ctypes
import json
import os
import subprocess
import sys
import time

HERE = os.path.dirname(os.path.abspath(__file__))
LOCK = os.path.join(HERE, ".cad.lock")
_POSIX_LOCK_FD = None


def free_ram_mb():
    if os.name == "nt":
        class MEMORYSTATUSEX(ctypes.Structure):
            _fields_ = [("dwLength", ctypes.c_ulong), ("dwMemoryLoad", ctypes.c_ulong),
                        ("ullTotalPhys", ctypes.c_ulonglong), ("ullAvailPhys", ctypes.c_ulonglong),
                        ("ullTotalPageFile", ctypes.c_ulonglong), ("ullAvailPageFile", ctypes.c_ulonglong),
                        ("ullTotalVirtual", ctypes.c_ulonglong), ("ullAvailVirtual", ctypes.c_ulonglong),
                        ("sullAvailExtendedVirtual", ctypes.c_ulonglong)]
        st = MEMORYSTATUSEX()
        st.dwLength = ctypes.sizeof(MEMORYSTATUSEX)
        ctypes.windll.kernel32.GlobalMemoryStatusEx(ctypes.byref(st))
        return st.ullAvailPhys / 2**20
    with open("/proc/meminfo") as f:
        for line in f:
            if line.startswith("MemAvailable:"):
                return int(line.split()[1]) / 1024
    return float("inf")


def pid_alive(pid):
    if os.name == "nt":
        h = ctypes.windll.kernel32.OpenProcess(0x1000, False, pid)  # PROCESS_QUERY_LIMITED_INFORMATION
        if not h:
            return False
        code = ctypes.c_ulong()
        ctypes.windll.kernel32.GetExitCodeProcess(h, ctypes.byref(code))
        ctypes.windll.kernel32.CloseHandle(h)
        return code.value == 259  # STILL_ACTIVE
    try:
        os.kill(pid, 0)
        return True
    except OSError:
        return False


def _try_windows_lock(cmd, stale_s):
    try:
        fd = os.open(LOCK, os.O_CREAT | os.O_EXCL | os.O_WRONLY)
    except FileExistsError:
        try:
            with open(LOCK, encoding="utf-8") as f:
                info = json.load(f)
            age = time.time() - info.get("t", 0)
            if age > stale_s or not pid_alive(int(info.get("pid", -1))):
                os.remove(LOCK)
                print(f"[run_locked] broke stale lock {info}", flush=True)
        except (OSError, ValueError):
            pass
        return False
    with os.fdopen(fd, "w", encoding="utf-8") as f:
        json.dump({"pid": os.getpid(), "t": time.time(), "cmd": cmd}, f)
    return True
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
